ponikrf/frank/hardware/frank_m1/DOCS/back.png

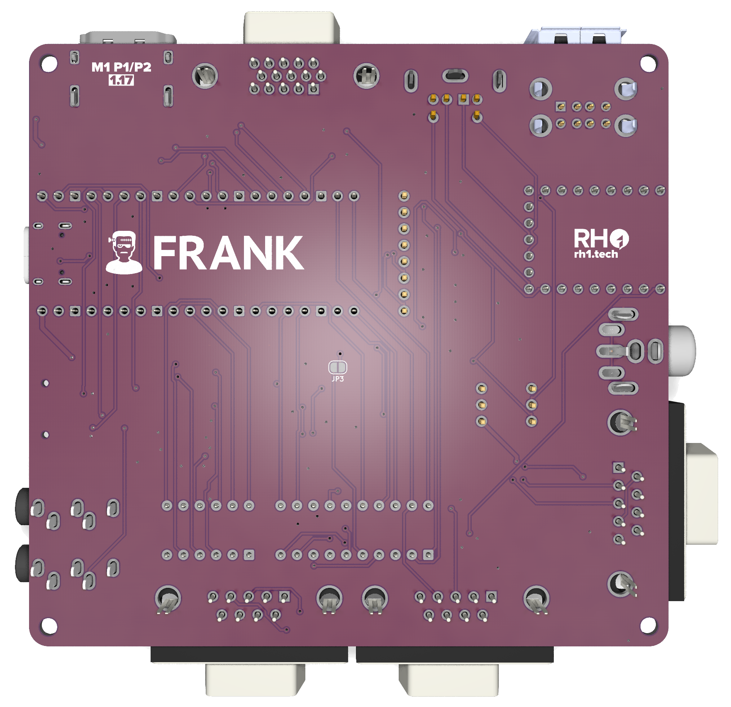
hardware/frank_m1/DOCS/back.png
