ponikrf/frank/hardware/frank_m2/DOCS/front.png

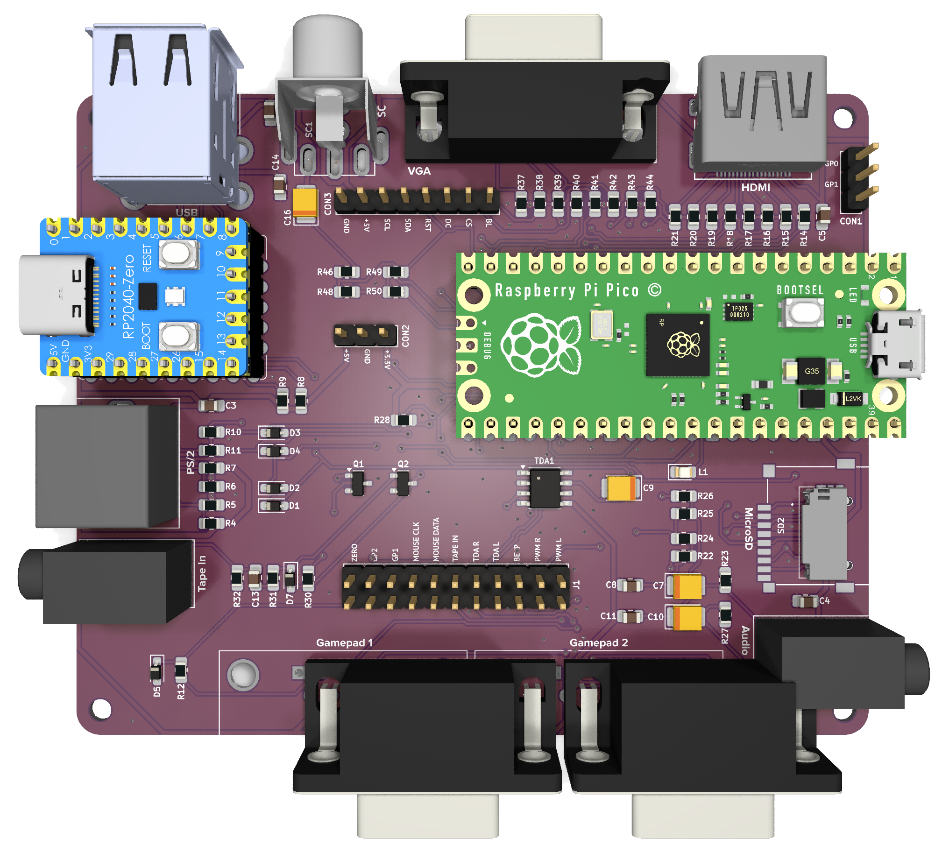
hardware/frank_m2/DOCS/front.png
