ponikrf/frank/hardware/minifrank_rm1/DOCS/front.png

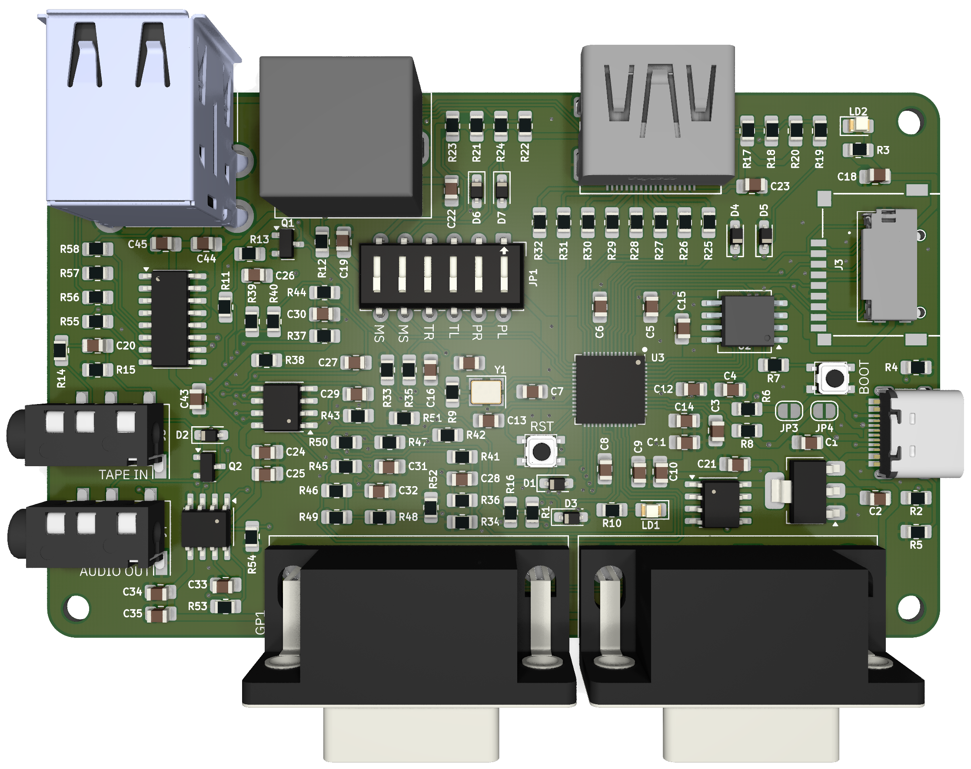
hardware/minifrank_rm1/DOCS/front.png
