ponikrf/frank/hardware/usb2ps2/DOCS/front.png

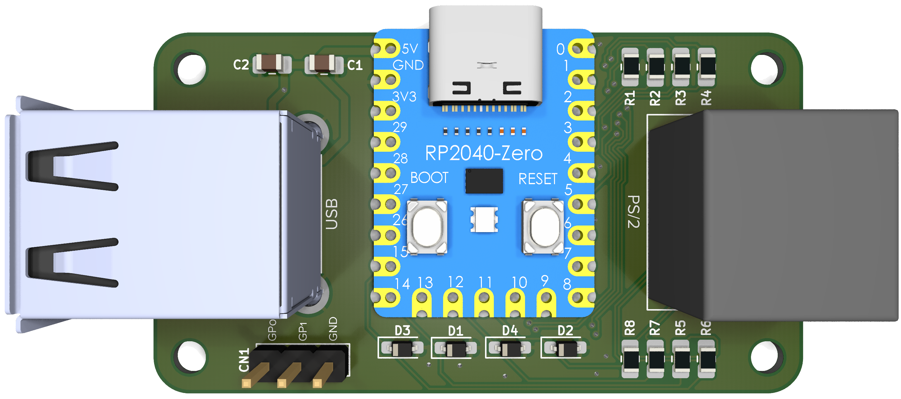
hardware/usb2ps2/DOCS/front.png
