ponikrf/frank/hardware/turbofrank/CASE/1_06/top.stl

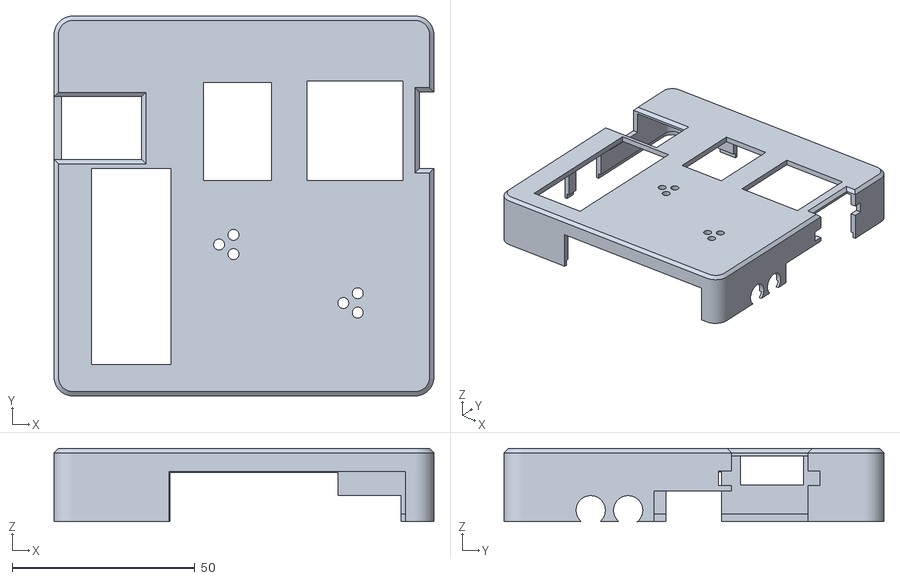
[picture p25: CAD file, 2025-05-07]
hardware/turbofrank/CASE/1_06/top.stl
104.0 x 104.0 x 20.0
