ponikrf/frank/hardware/frank_m1/3D/FHU-1x5.step

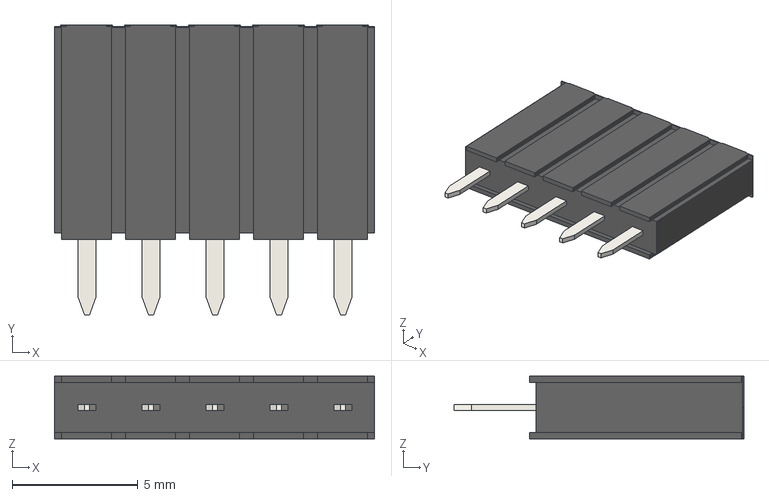
[picture p27: CAD file, 2025-05-07]
hardware/frank_m1/3D/FHU-1x5.step
12.7 x 11.5 x 2.50 mm
