ponikrf/frank/hardware/frank_m2/3D/FHU-1x20.step

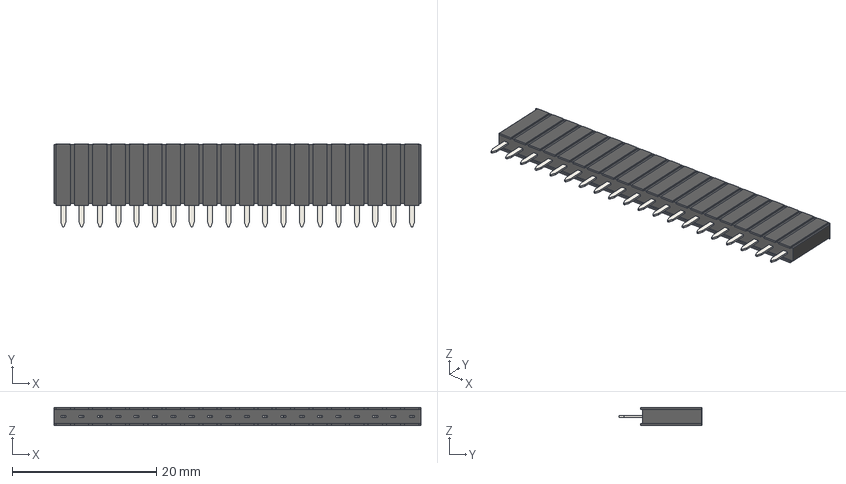
[picture p28: CAD file, 2025-05-07]
hardware/frank_m2/3D/FHU-1x20.step
50.8 x 11.5 x 2.50 mm
