ponikrf/frank/lab/minifrank_rm2/3D/DS05-127-2-04BK-SMT-TR.step

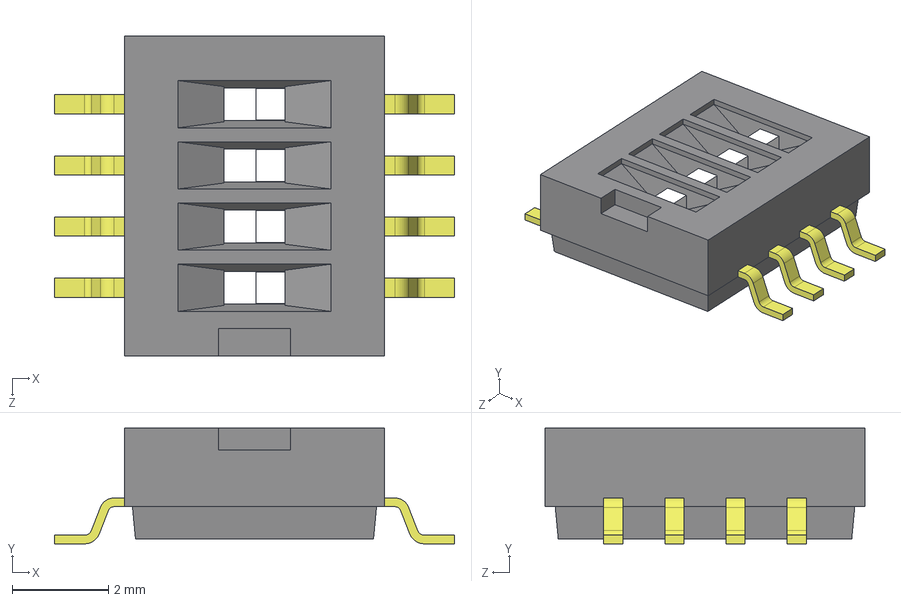
[picture p29: CAD file, 2025-05-07]
lab/minifrank_rm2/3D/DS05-127-2-04BK-SMT-TR.step
8.30 x 2.40 x 6.65 mm
