ponikrf/frank/hardware/turbofrank/3D/Micro_SD_Card_and_Holder.stp

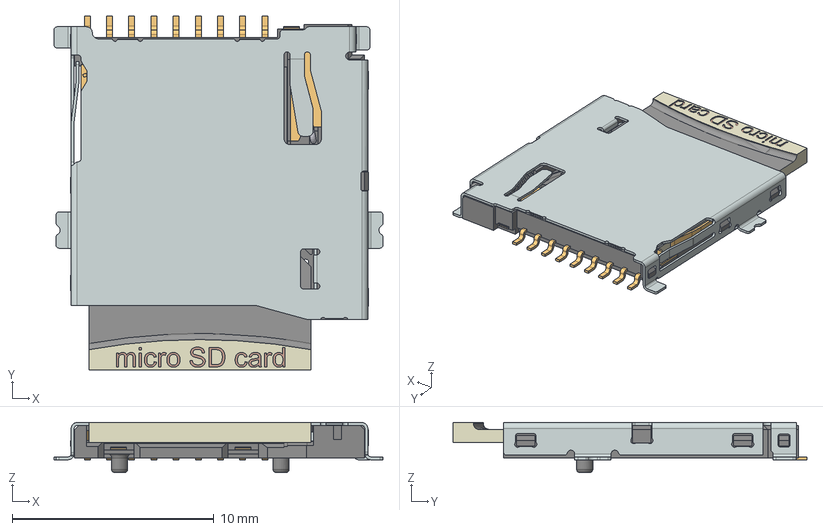
[picture p30: CAD file, 2025-05-07]
hardware/turbofrank/3D/Micro_SD_Card_and_Holder.stp
16.3 x 17.5 x 2.48 mm
693071020811_Housing
693071020811_Guide
693071020811_Spring
693071020811_Contact
693071020811_Hook
693071020811_Agraphe
693071020811_Shielding
MicroSD
