ponikrf/frank/lab/minifrank_rm2/3D/raspberry pi pico with contacts.step

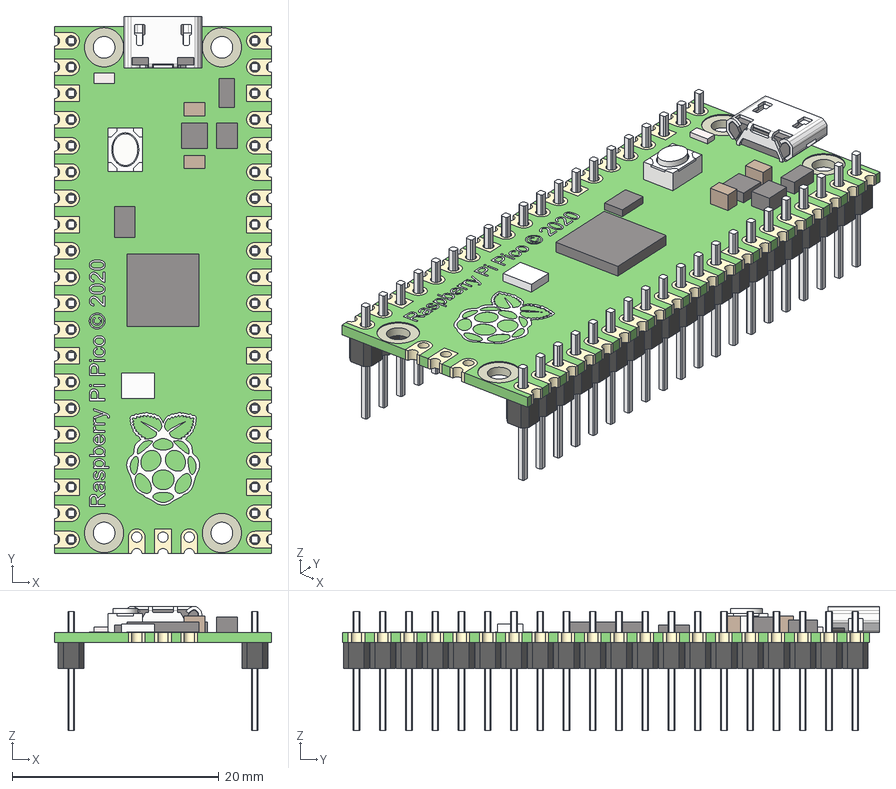
[picture p31: CAD file, 2025-05-07]
lab/minifrank_rm2/3D/raspberry pi pico with contacts.step
21.0 x 52.0 x 12.0 mm
ножка x 20
ножка v3(Mirror) x 20
