ponikrf/frank/hardware/frank_m2/3D/1x20 Male Pin Header.STEP

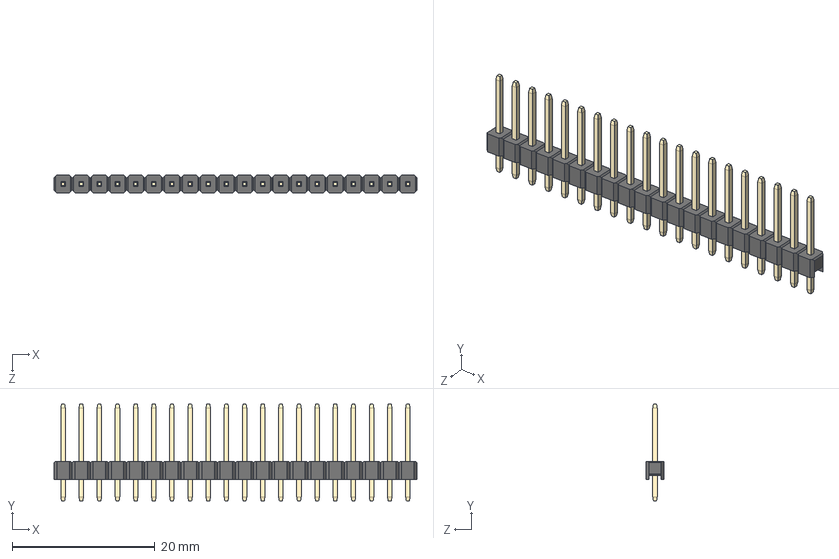
[picture p32: CAD file, 2025-05-07]
hardware/frank_m2/3D/1x20 Male Pin Header.STEP
50.8 x 13.5 x 2.50 mm
