ponikrf/frank/lab/minifrank_rm2/3D/soic-14.stp

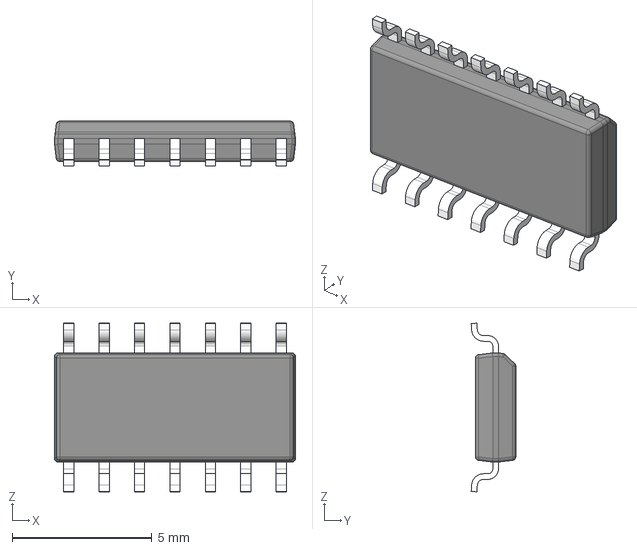
[picture p33: CAD file, 2025-05-07]
lab/minifrank_rm2/3D/soic-14.stp
8.64 x 1.60 x 6.05 mm
BODY_M14A_20
LEAD_M14A_46 x 14
