ponikrf/frank/lab/minifrank_rm2/3D/ESP8266-12E_ESP-12E.step

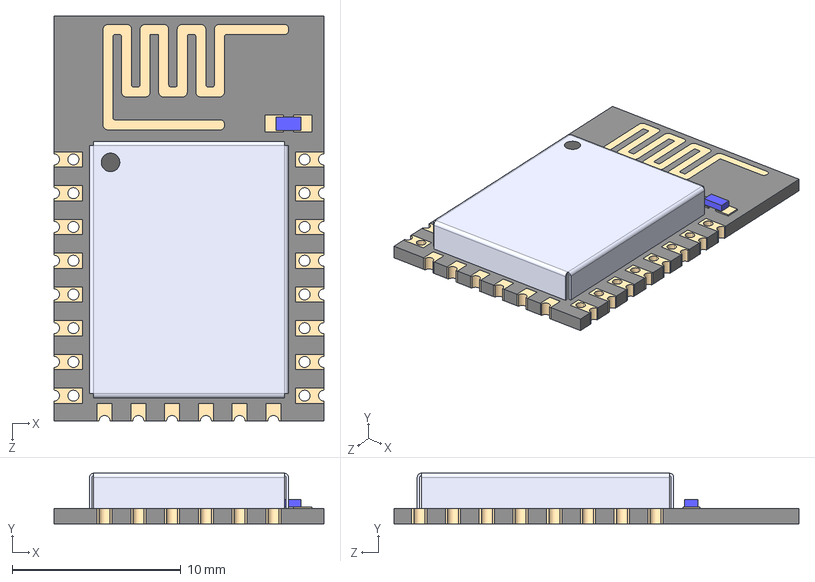
[picture p34: CAD file, 2025-05-07]
lab/minifrank_rm2/3D/ESP8266-12E_ESP-12E.step
16.0 x 3.00 x 24.0 mm
