ponikrf/frank/lab/minifrank_rm2/3D/LQH2MCN100K02L.step

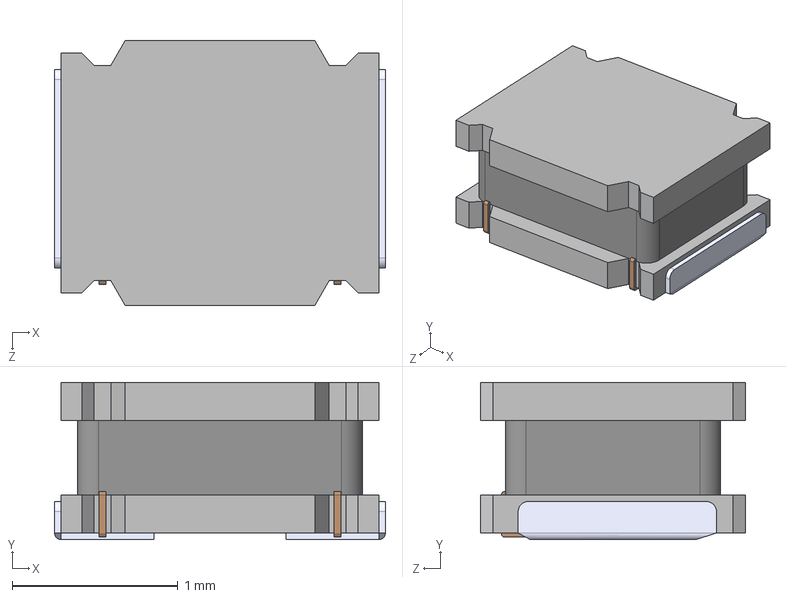
[picture p35: CAD file, 2025-05-07]
lab/minifrank_rm2/3D/LQH2MCN100K02L.step
2.00 x 0.95 x 1.60 mm
