ponikrf/frank/lab/minifrank_rm2/3D/Mini-DIN-6P.step

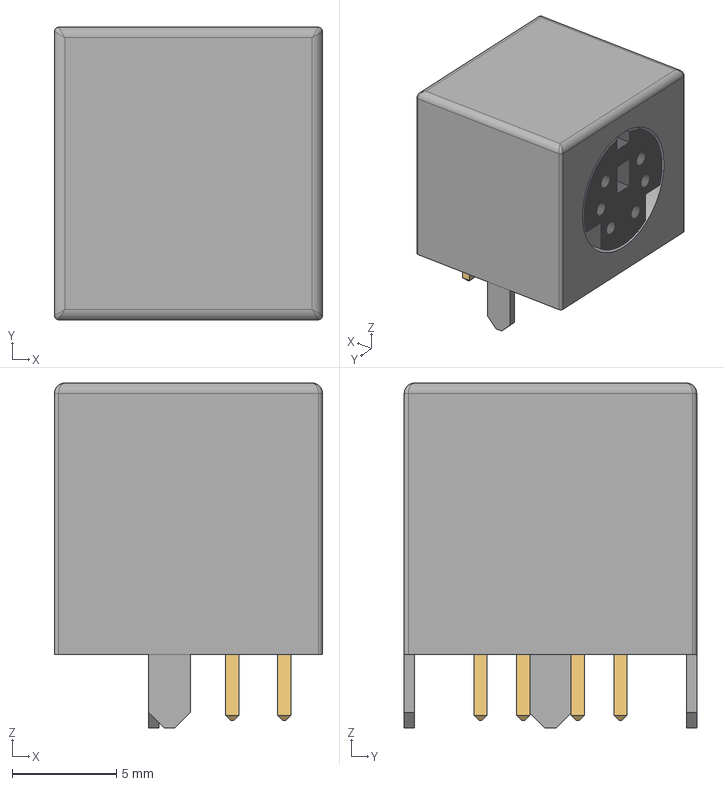
[picture p36: CAD file, 2025-03-16]
lab/minifrank_rm2/3D/Mini-DIN-6P.step
12.8 x 14.0 x 16.5 mm
