ponikrf/frank/lab/minifrank_rm2/3D/SJ1-3535NG.stp

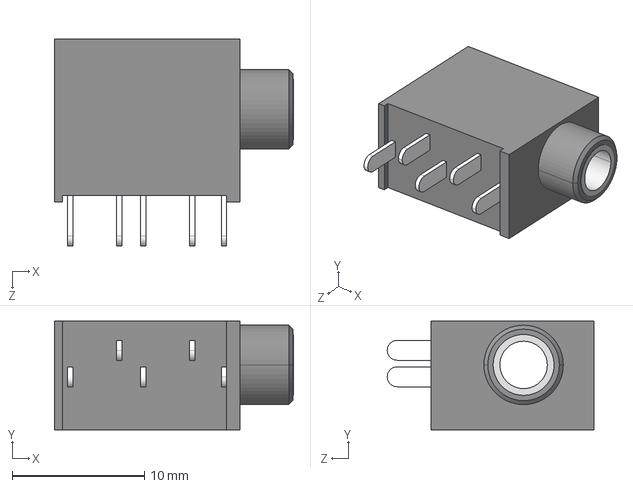
[picture p37: CAD file, 2025-03-16]
lab/minifrank_rm2/3D/SJ1-3535NG.stp
18.1 x 8.20 x 15.6 mm
