ponikrf/frank/lab/minifrank_rm2/3D/MAX232CSE+.stp

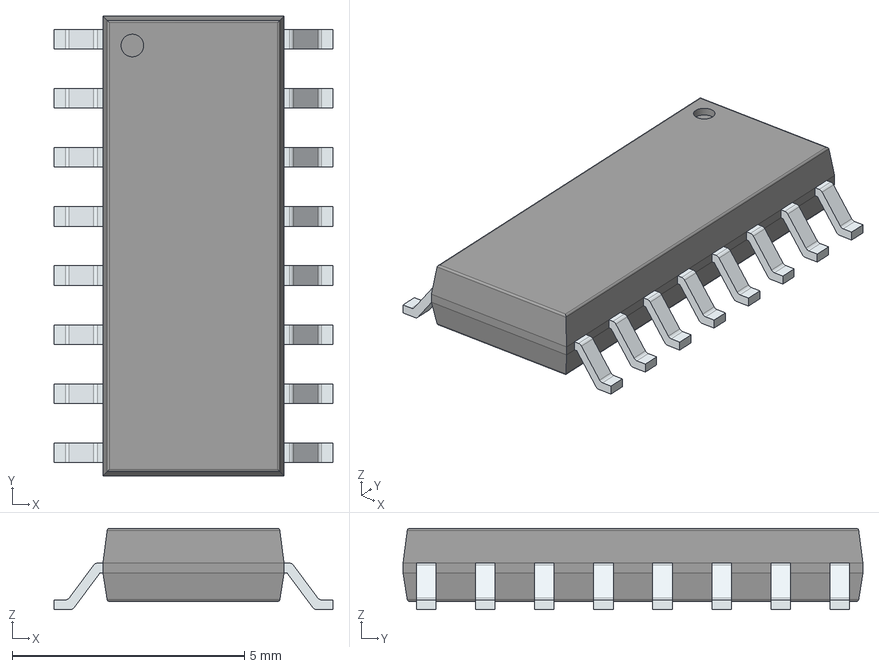
[picture p38: CAD file, 2025-03-16]
lab/minifrank_rm2/3D/MAX232CSE+.stp
6.00 x 9.90 x 1.75 mm
PinsArrayLR
