ponikrf/frank/lab/minifrank_rm2/3D/USB1035-GF-P-0-B-B.stp

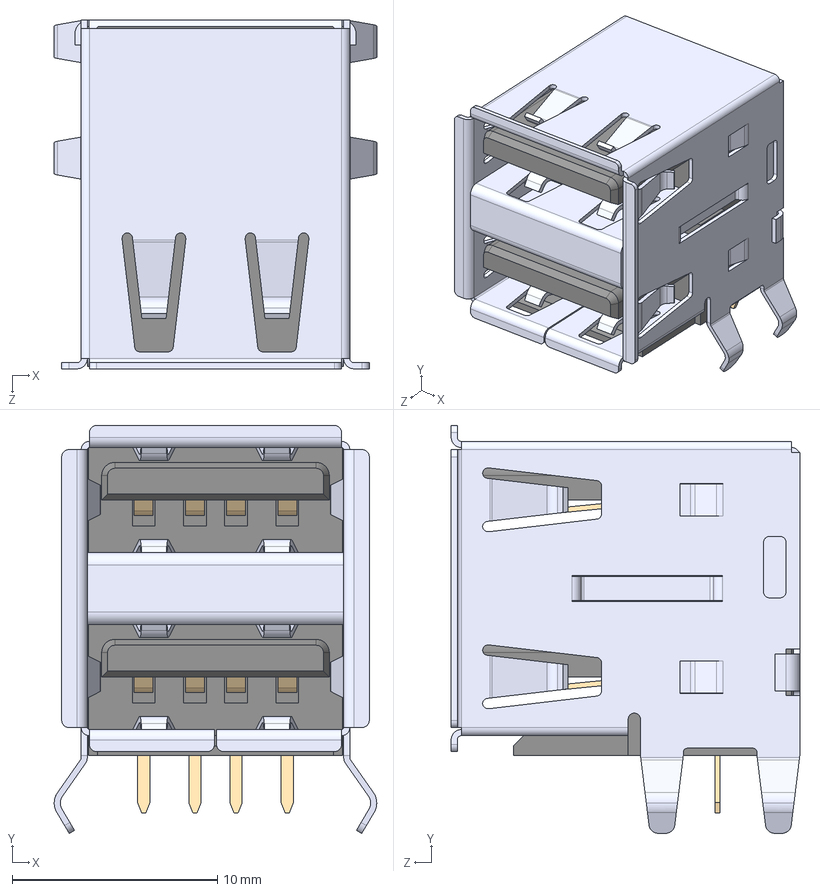
[picture p40: CAD file, 2025-03-16]
lab/minifrank_rm2/3D/USB1035-GF-P-0-B-B.stp
15.7 x 19.9 x 17.0 mm
