ponikrf/frank/lab/minifrank_rm2/3D/3225 SMD Crystal Oscillator.STEP

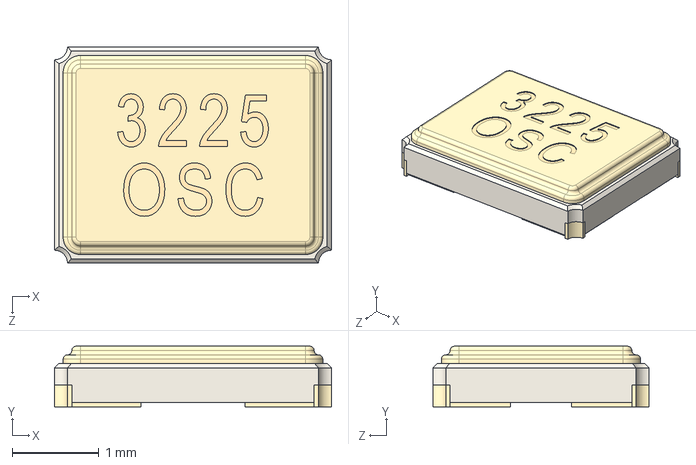
[picture p41: CAD file, 2025-03-16]
lab/minifrank_rm2/3D/3225 SMD Crystal Oscillator.STEP
3.20 x 0.7 x 2.50 mm
