ponikrf/frank/lab/minifrank_rm2/3D/PJ320D.STEP

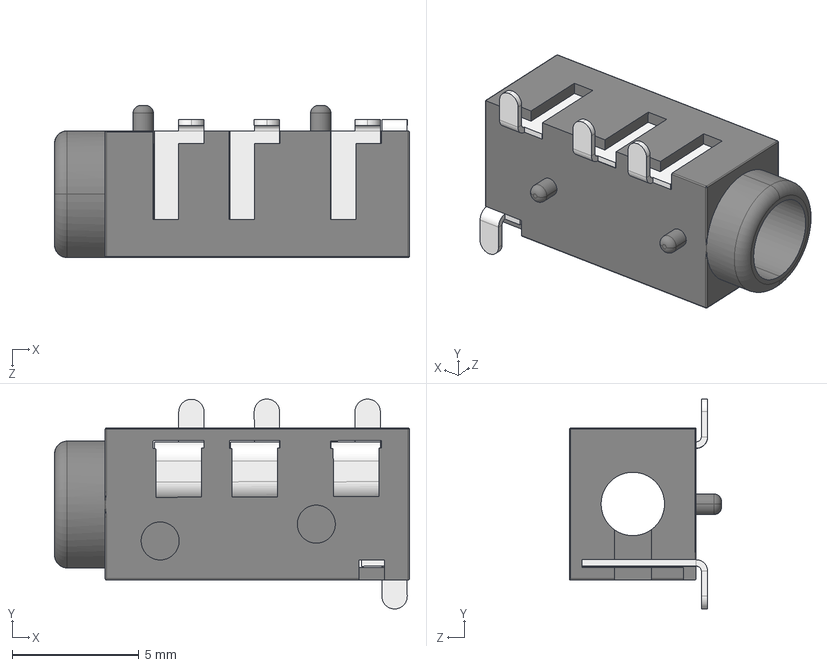
[picture p42: CAD file, 2025-03-16]
lab/minifrank_rm2/3D/PJ320D.STEP
14.0 x 8.28 x 6.00 mm
PJ320A
PJ320D-Pin x 3
PJ320D-Pin-B
