ponikrf/frank/lab/minifrank_rm2/3D/DSUB-15-HD_Male_Horizontal_P2.29x1.98mm_EdgePinOffset3.03mm_Housed_MountingHolesOffset4.94mm.step

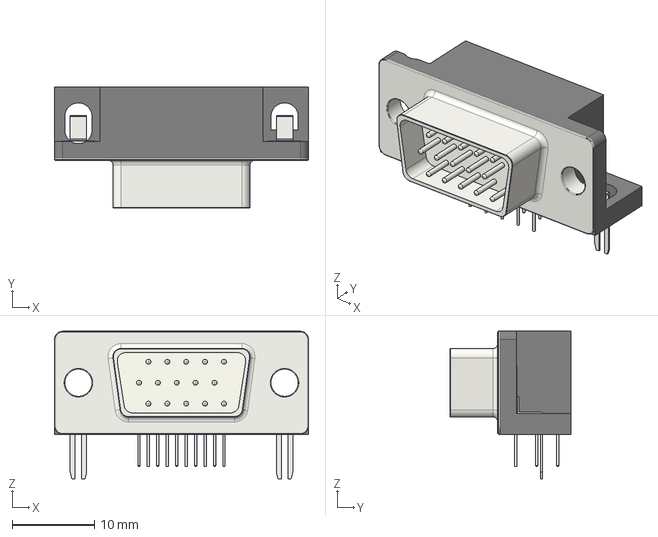
[picture p43: CAD file, 2025-03-16]
lab/minifrank_rm2/3D/DSUB-15-HD_Male_Horizontal_P2.29x1.98mm_EdgePinOffset3.03mm_Housed_MountingHolesOffset4.94mm.step
30.8 x 14.7 x 17.9 mm
