ponikrf/frank/lab/minifrank_rm2/3D/W25Q128JVSIQ.stp

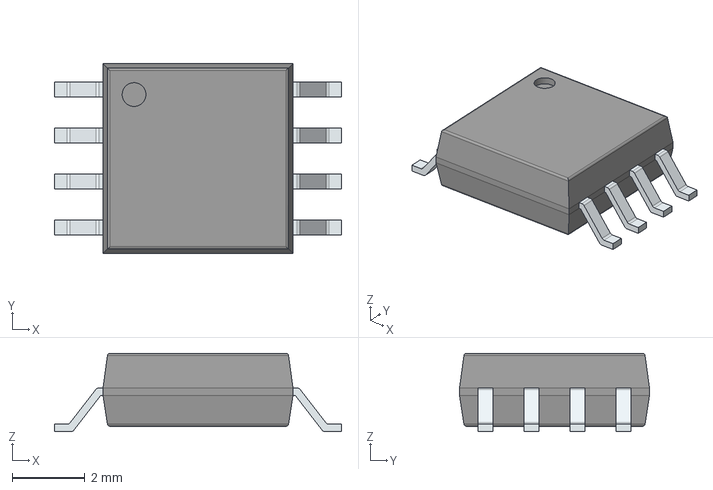
[picture p44: CAD file, 2025-03-16]
lab/minifrank_rm2/3D/W25Q128JVSIQ.stp
7.90 x 5.23 x 2.16 mm
PinsArrayLR
