ponikrf/frank/lab/minifrank_rm2/3D/CUI_DEVICES_RCJ-013.step

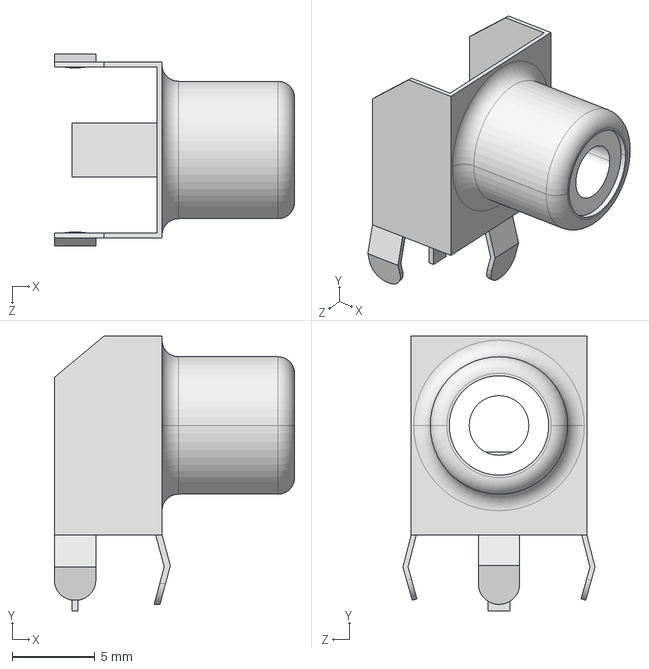
[picture p45: CAD file, 2025-03-16]
lab/minifrank_rm2/3D/CUI_DEVICES_RCJ-013.step
14.5 x 16.6 x 11.6 mm
