ponikrf/frank/lab/minifrank_rm2/3D/HRO_TYPE-C-31-M-12.step

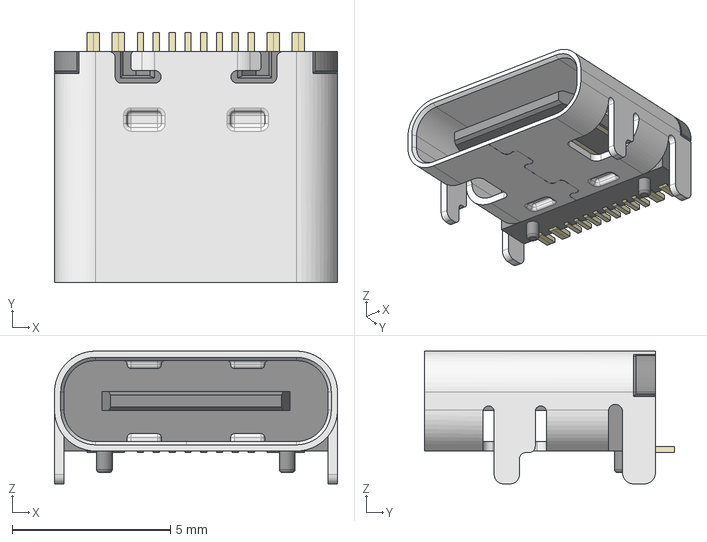
[picture p46: CAD file, 2025-03-16]
lab/minifrank_rm2/3D/HRO_TYPE-C-31-M-12.step
8.95 x 7.90 x 4.20 mm
