ponikrf/frank/lab/minifrank_rm2/3D/SO-8_5.3x6.2mm_P1.27mm.step

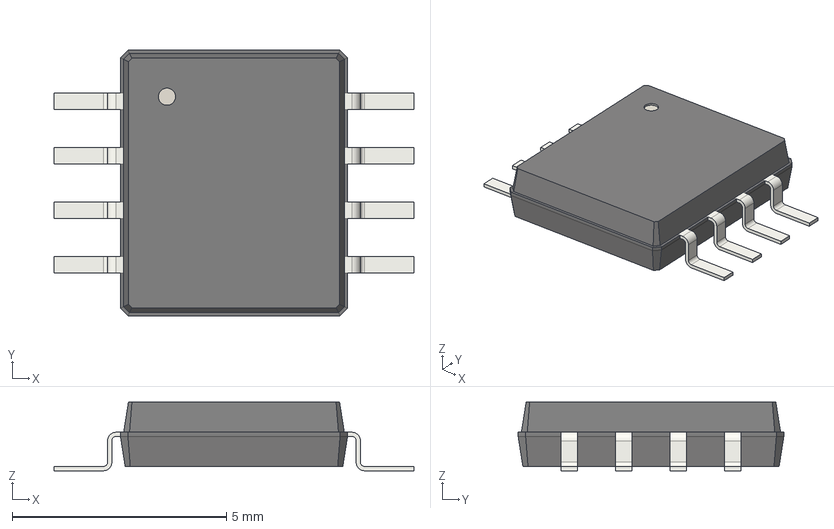
[picture p47: CAD file, 2025-03-16]
lab/minifrank_rm2/3D/SO-8_5.3x6.2mm_P1.27mm.step
8.40 x 6.20 x 1.60 mm
