ponikrf/frank/lab/minifrank_rm2/3D/Ts-1233_1.5.stp

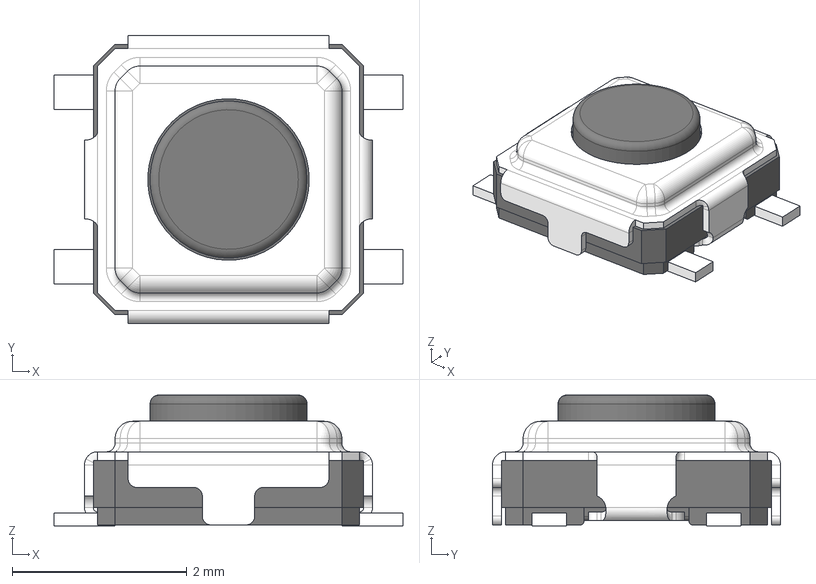
[picture p48: CAD file, 2025-03-16]
lab/minifrank_rm2/3D/Ts-1233_1.5.stp
4.00 x 3.30 x 1.50 mm
