ponikrf/frank/hardware/minifrank_rm1/DOCS/2_04/minifrank_rm1.pdf

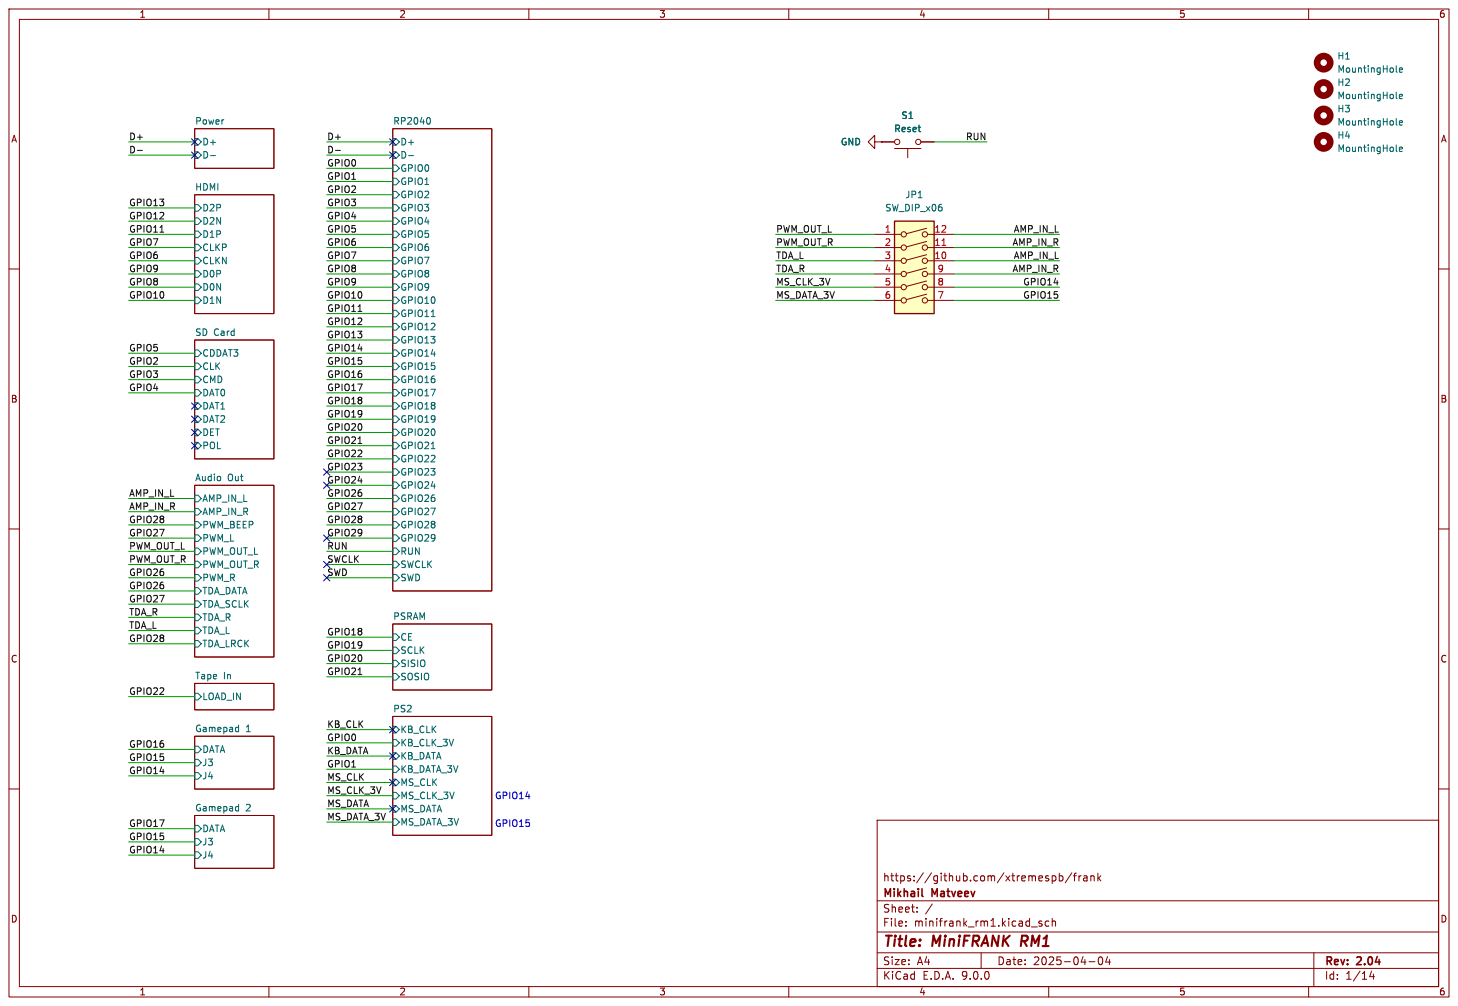
[picture p108: page 1]

https://github.com/xtremespb/frank

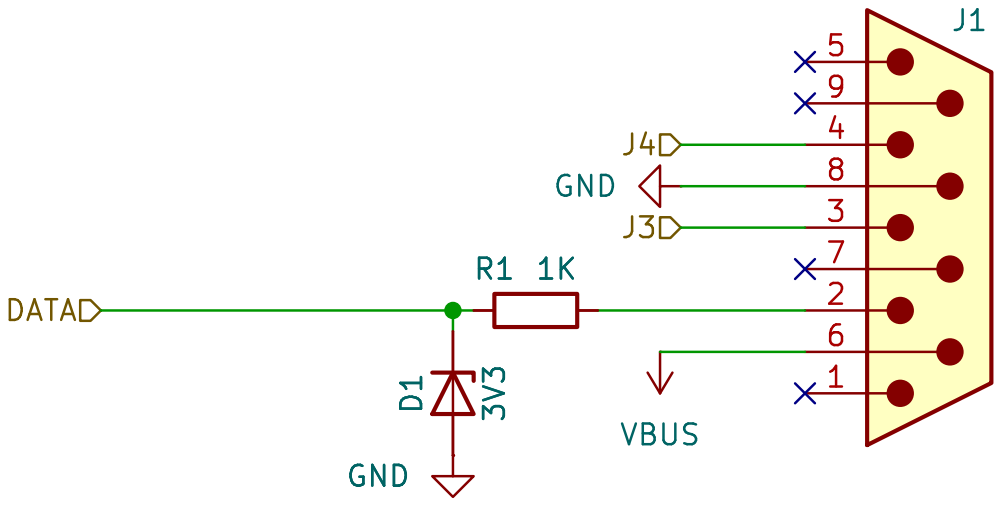
[picture p109: page 2]

https://github.com/xtremespb/frank

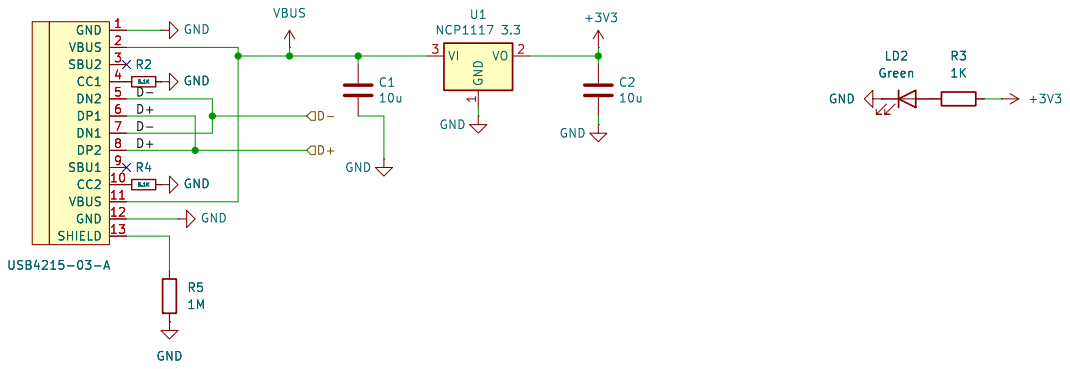
[picture p110: page 3]

https://github.com/xtremespb/frank

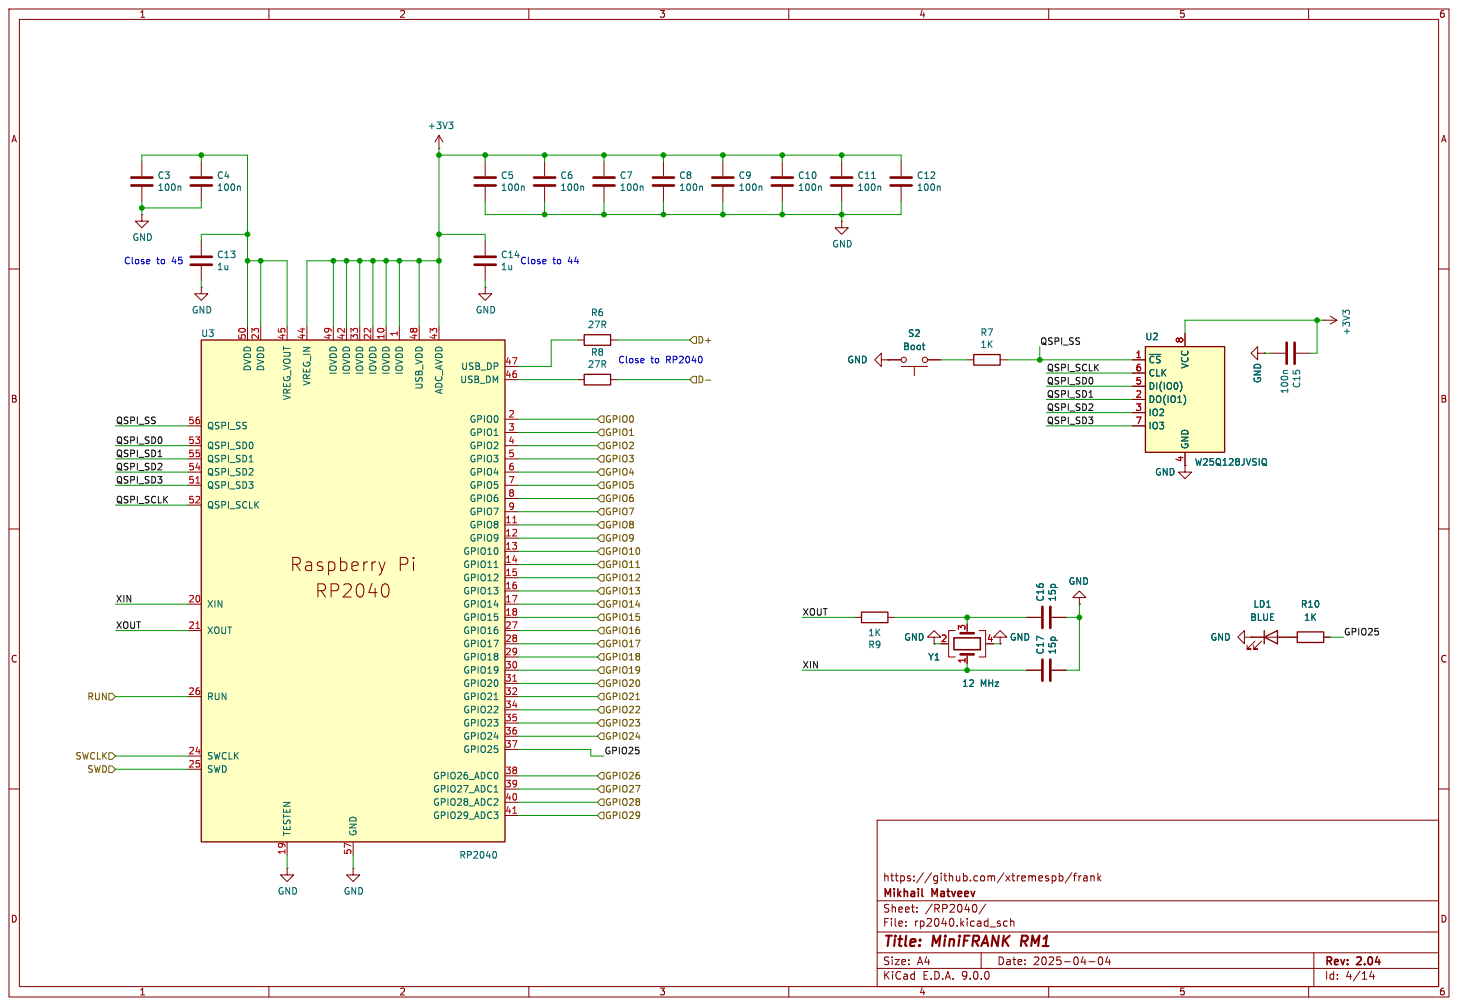
[picture p111: page 4]

https://github.com/xtremespb/frank GND

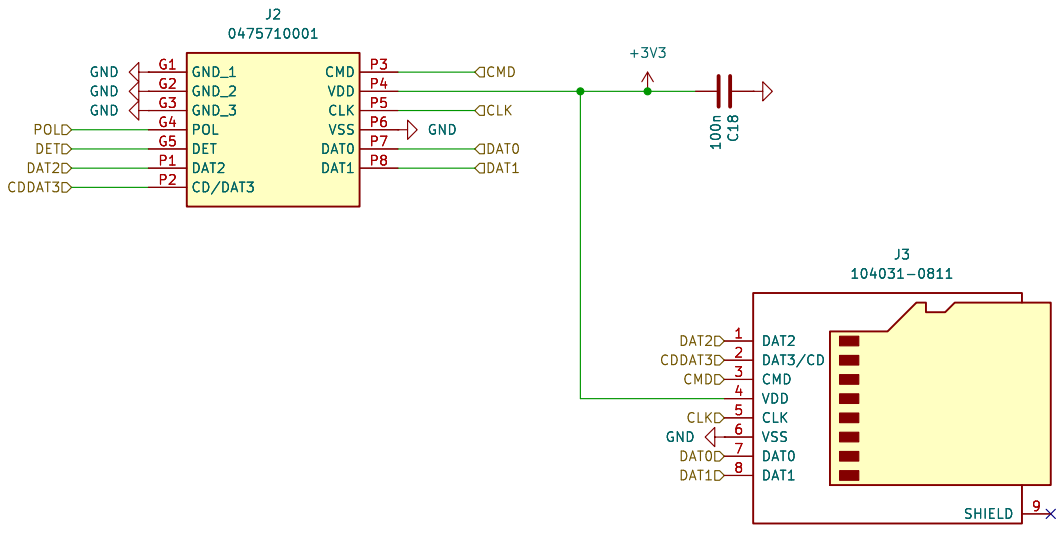
[picture p112: page 5]

https://github.com/xtremespb/frank GND

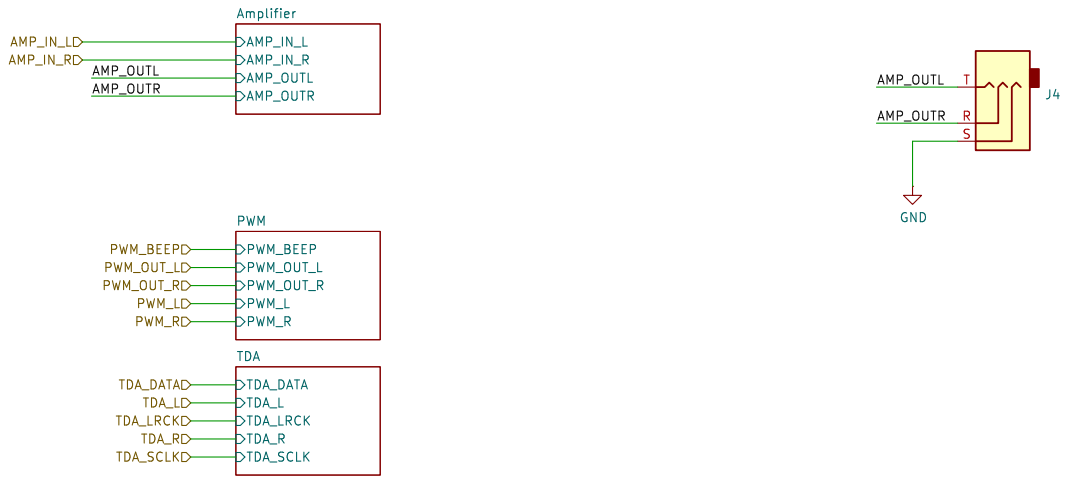
[picture p113: page 6]

https://github.com/xtremespb/frank

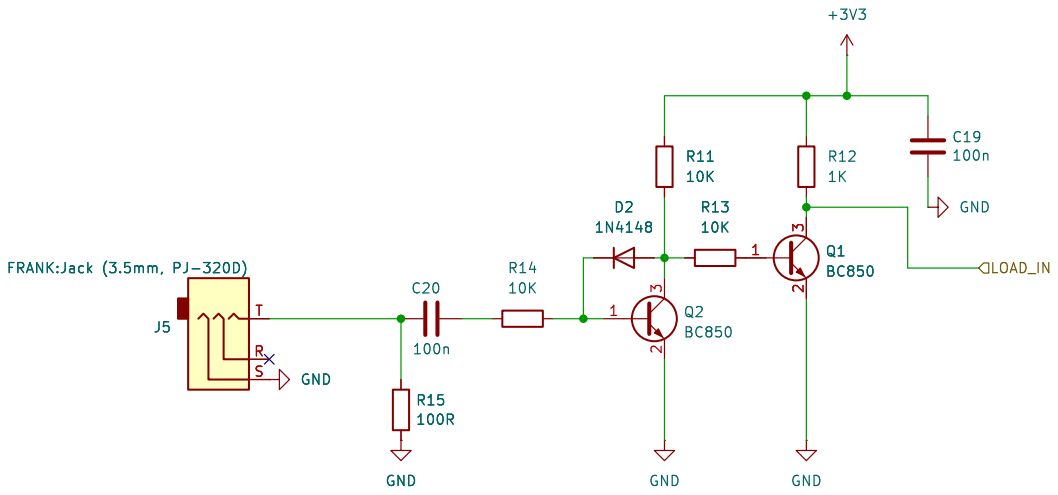
[picture p114: page 7]

https://github.com/xtremespb/frank GND

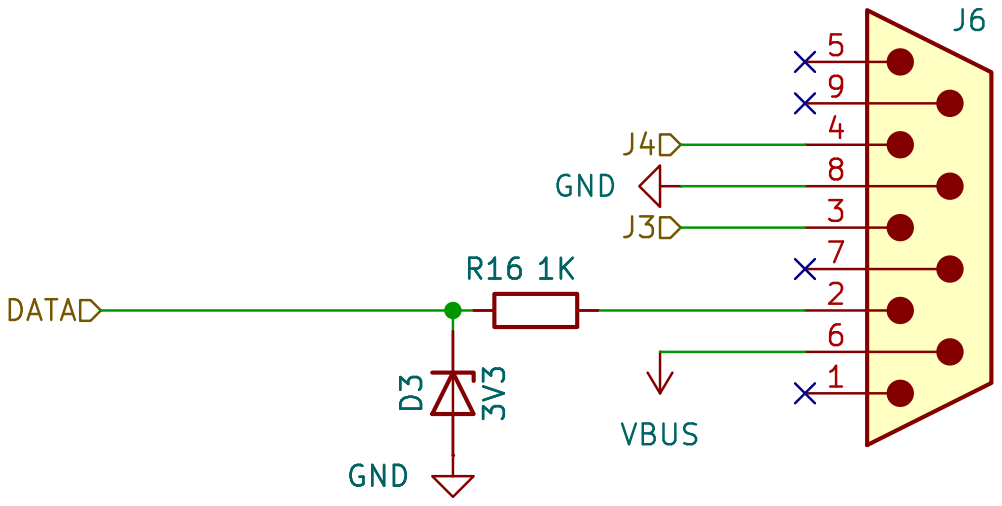
[picture p115: page 8]

https://github.com/xtremespb/frank

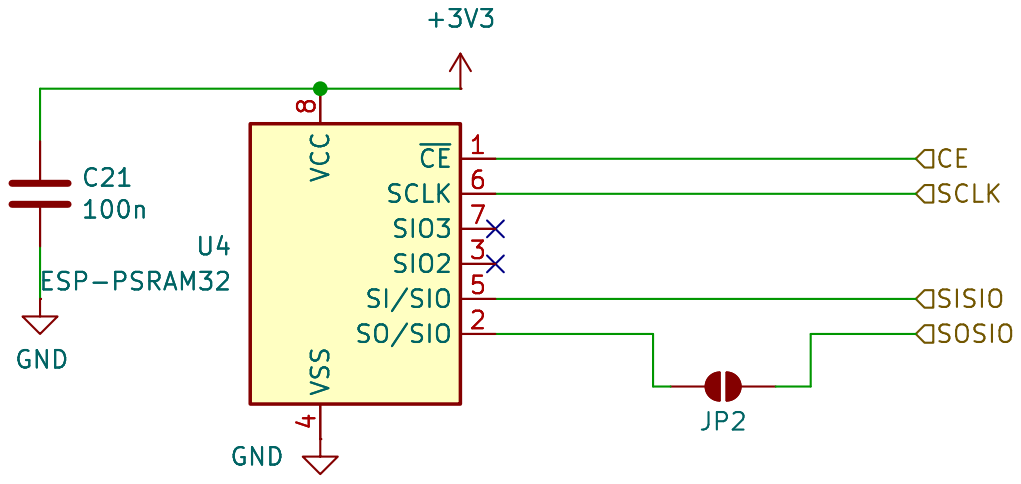
[picture p116: page 9]

4 ~{CE}1 SCLK 6 SIO3 7 SIO2 3 SI/SIO 5 SO/SIO 2 +3V3

4 ~{CE}1 SCLK 6 SIO3 7 SIO2 3 SI/SIO 5 SO/SIO 2 U4 ESP-PSRAM32 GND

https://github.com/xtremespb/frank

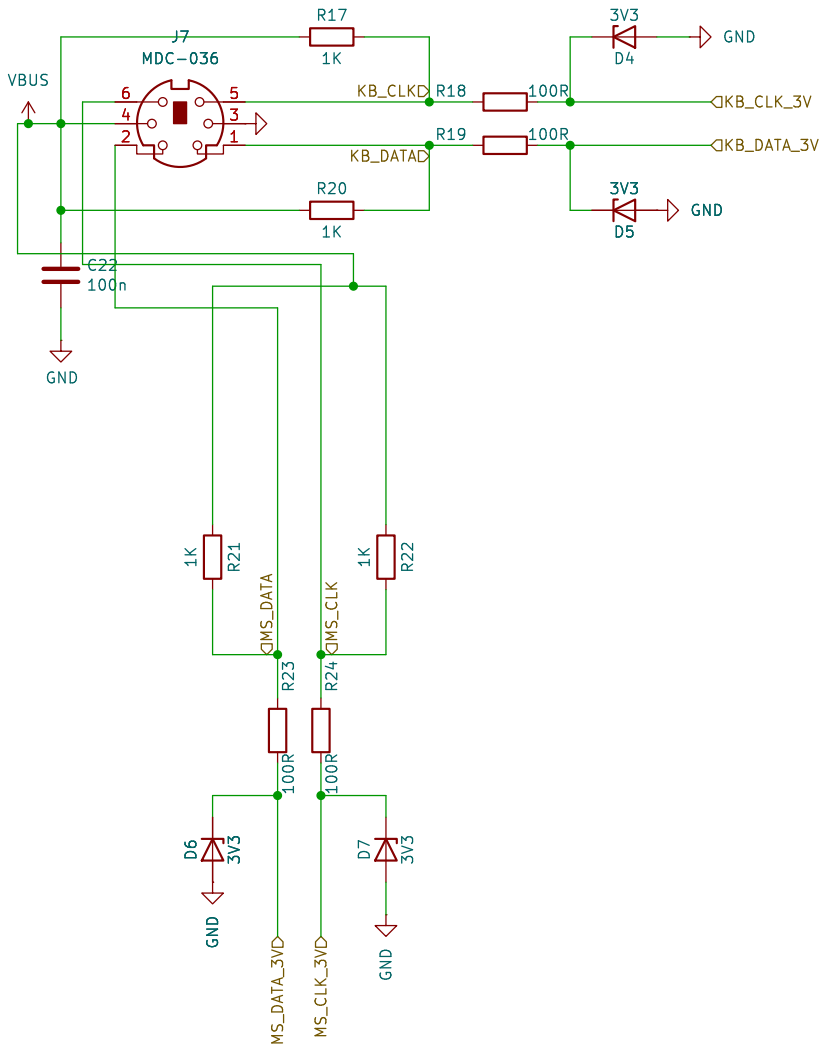
[picture p117: page 10]

https://github.com/xtremespb/frank R22 1K GND

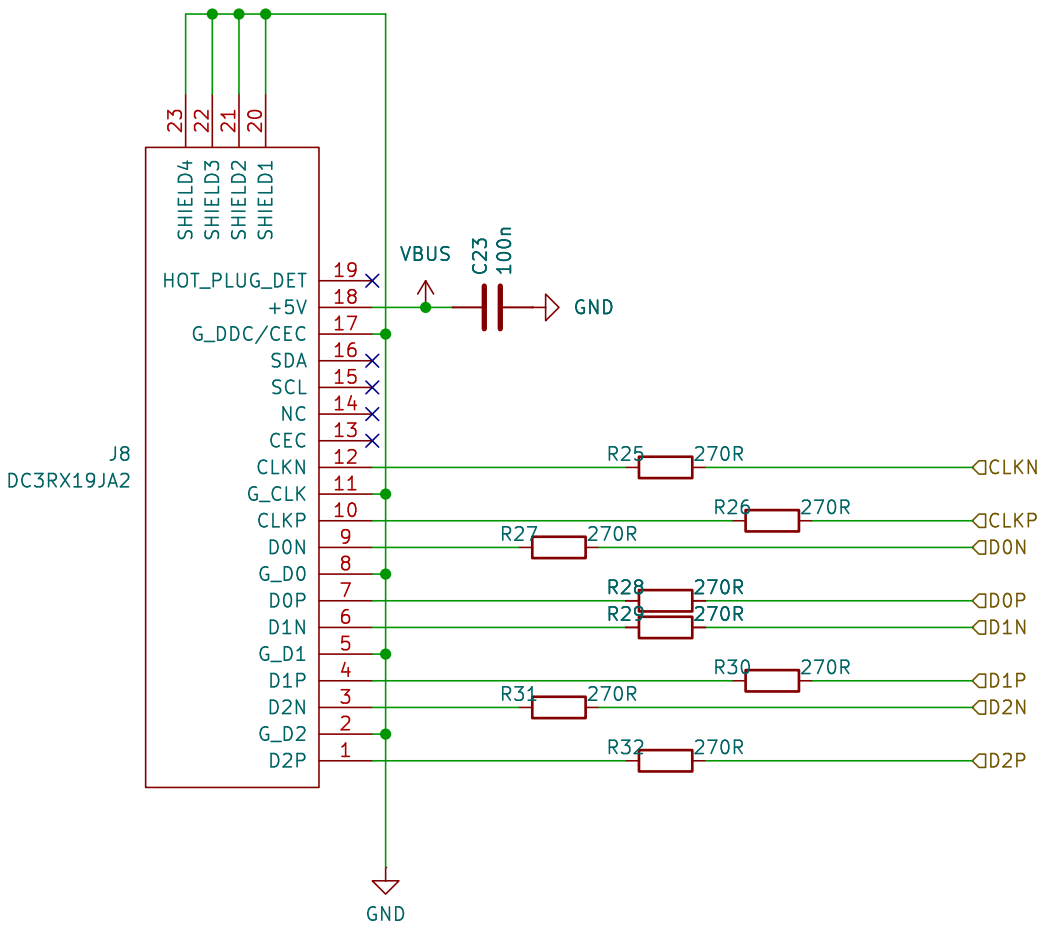
[picture p118: page 11]

https://github.com/xtremespb/frank

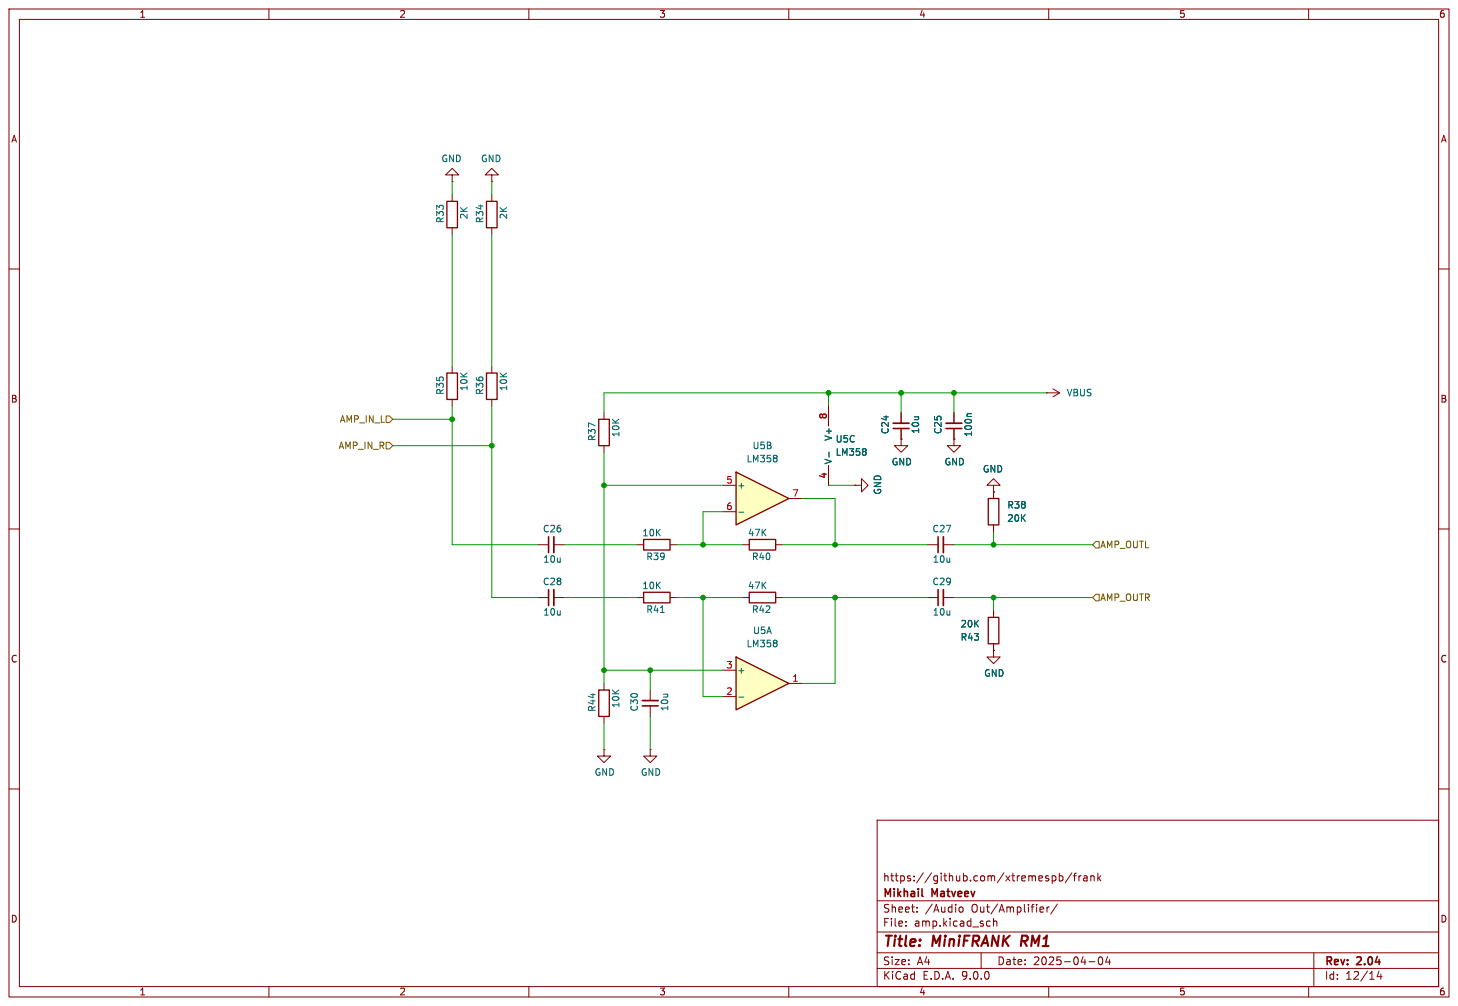
[picture p119: page 12]

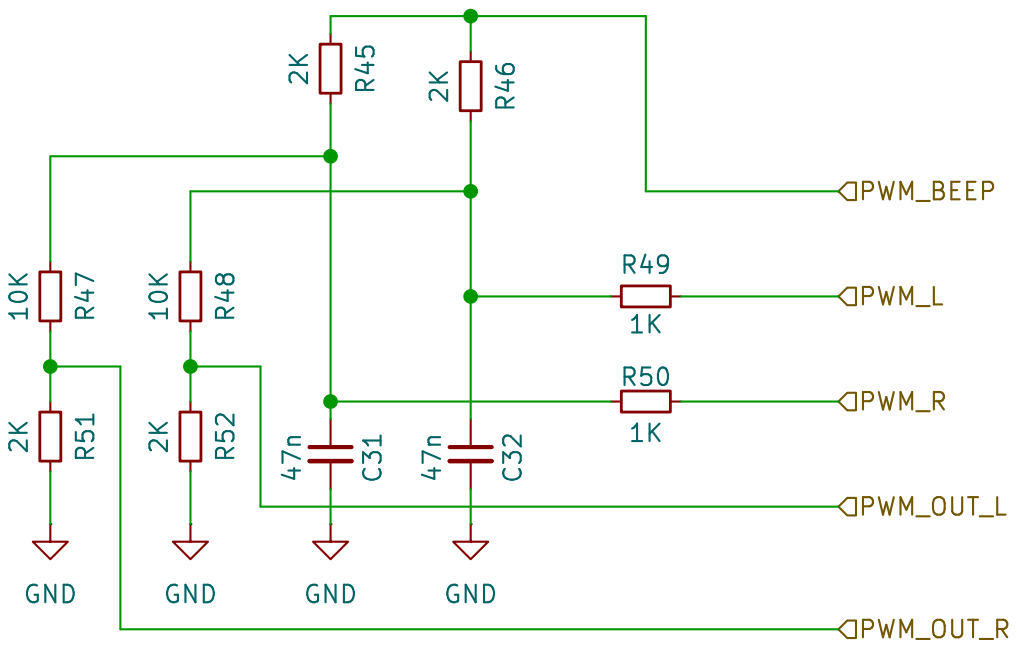
[picture p120: page 13]

https://github.com/xtremespb/frank R49

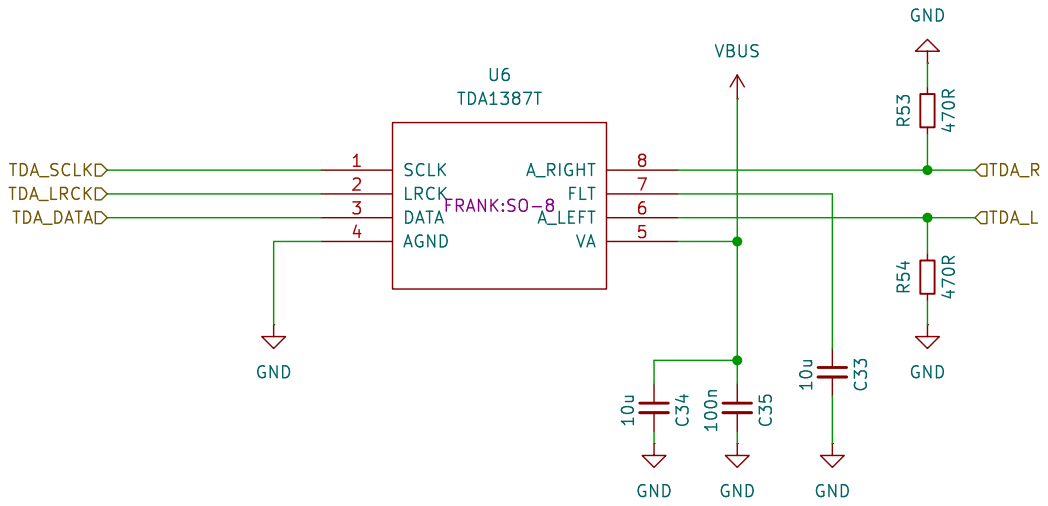
[picture p121: page 14]
