ponikrf/frank/hardware/minifrank_rm1/DOCS/2_05/assembly.pdf

## LD2 S²

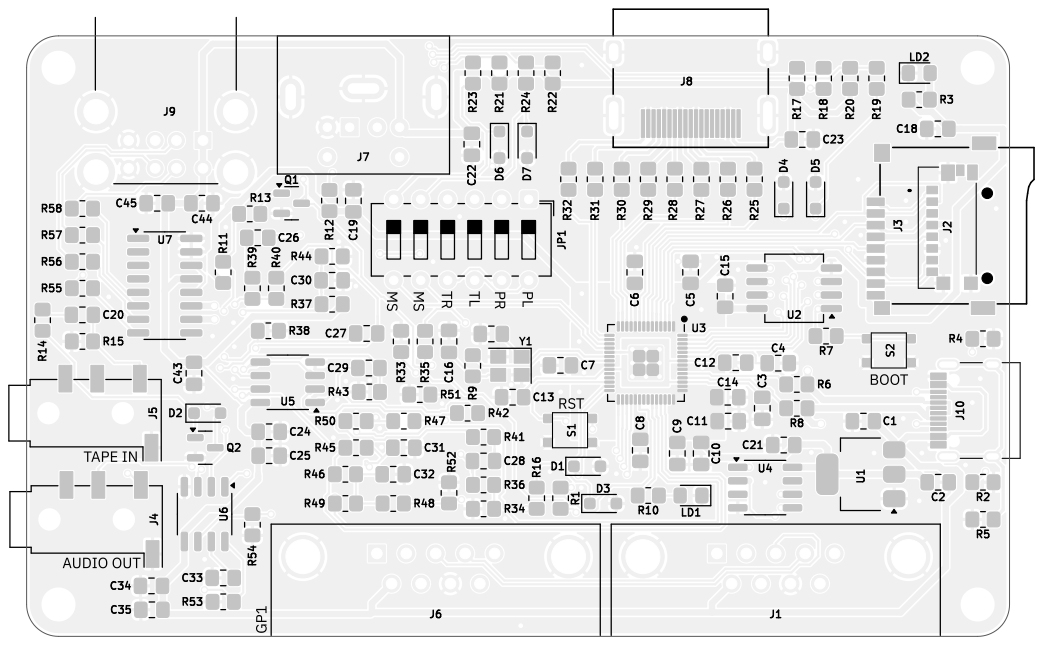
[picture p122: page 1]

https://github.com/xtremespb/frank Black And White TOP - Page 1/4

File: minifrank_rm1.kicad_pcb Sheet: Black And White TOP Mikhail Matveev

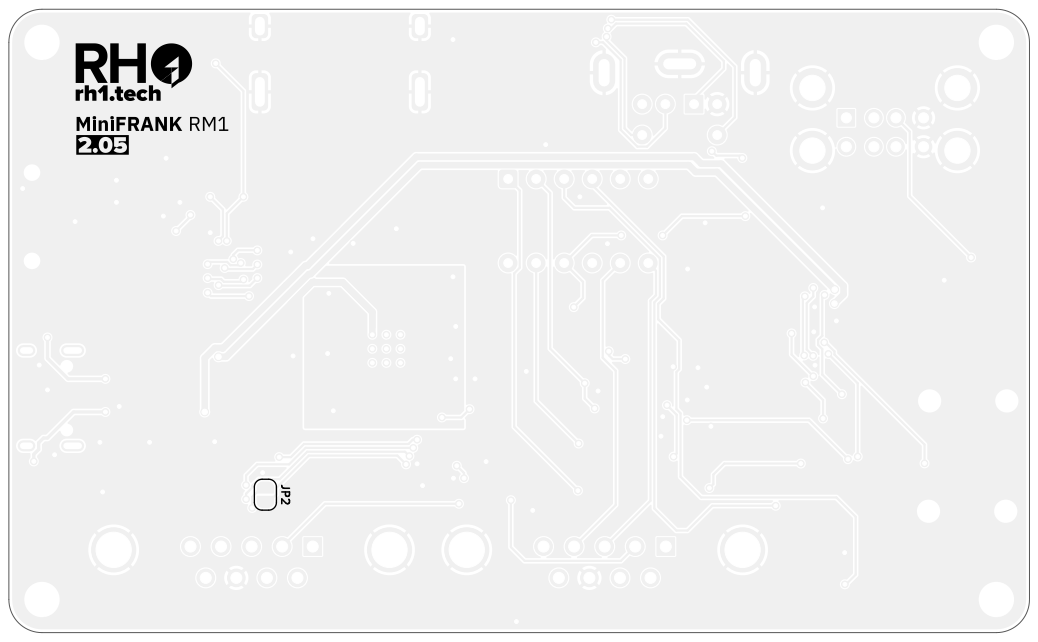
[picture p123: page 2]
D Date: 2025-04-07 KiCad; E.D.A. 9.0.0 Size: A4; Rev: 2.05; File: minifrank_rm1.kicad_pcb Sheet: Black; And; White; BOT Mikhail; Matveev; https://github.com/xtremespb/frank Black; BOT -; Page 2/4

Id: /1 Title: MiniFRANK RM1

## LD2 S²

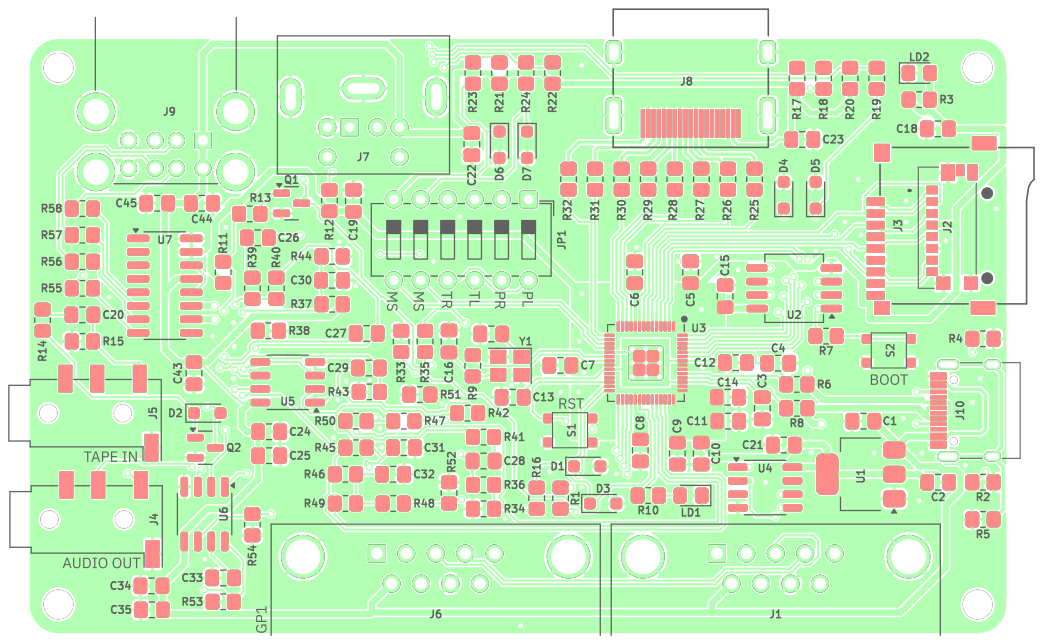
[picture p124: page 3]

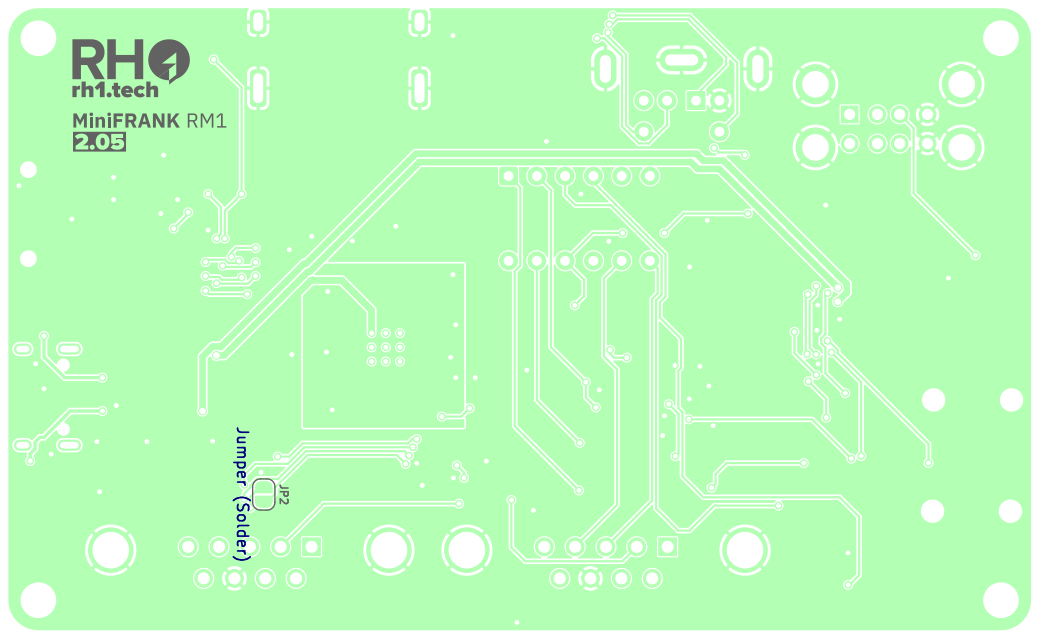
[picture p125: page 4]
D Date: 2025-04-07 KiCad; E.D.A. 9.0.0 Size: A4; Rev: 2.05; File: minifrank_rm1.kicad_pcb Sheet: Colored; BOT Mikhail; Matveev; https://github.com/xtremespb/frank Colored; BOT -; Page 4/4 Jumper (Solder)

Id: /1 Title: MiniFRANK RM1
