ponikrf/frank/hardware/minifrank_rm1/DOCS/2_05/minifrank_rm1.pdf

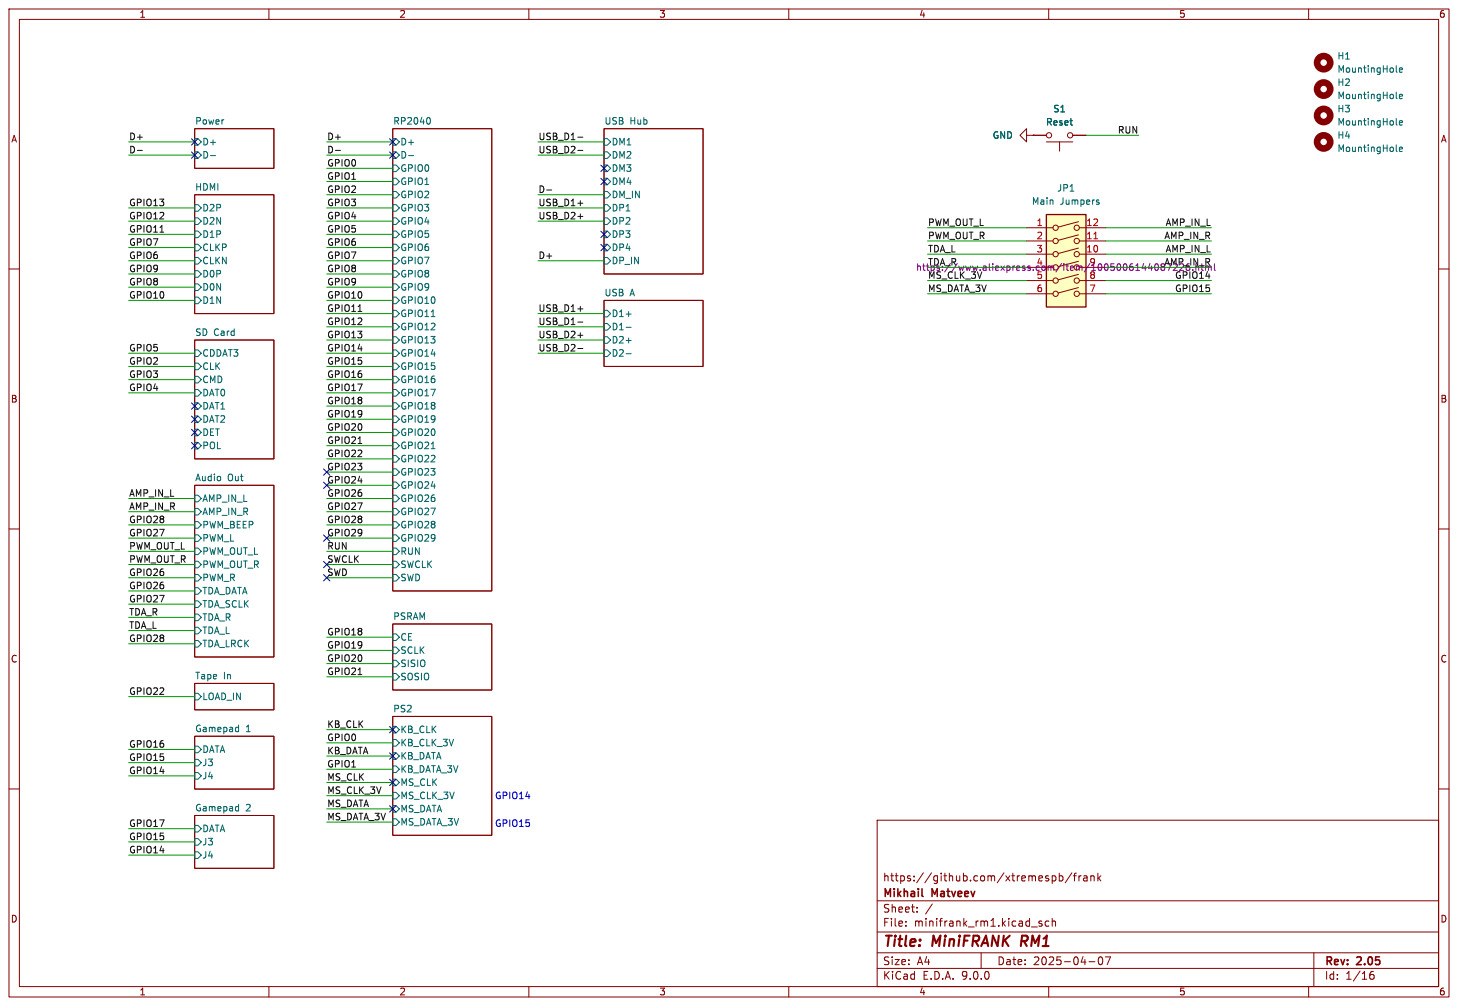
[picture p126: page 1]

PSRAM
https://github.com/xtremespb/frank CE
SCLK
SISIO
SOSIO


https://github.com/xtremespb/frank


https://github.com/xtremespb/frank

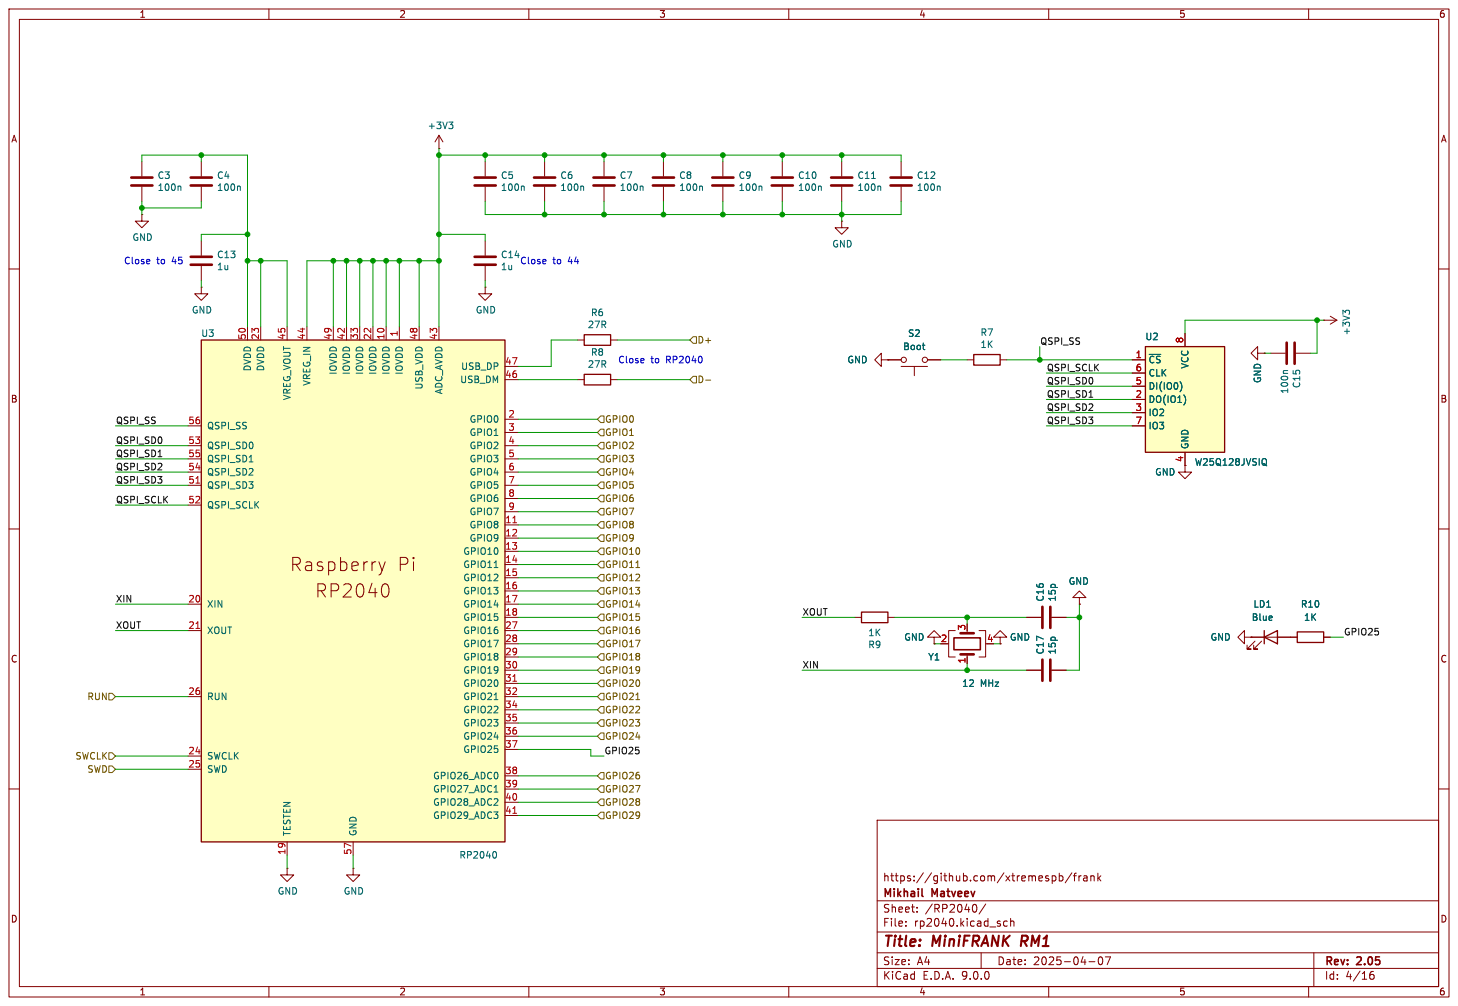
[picture p127: page 4]

https://github.com/xtremespb/frank GND



https://github.com/xtremespb/frank

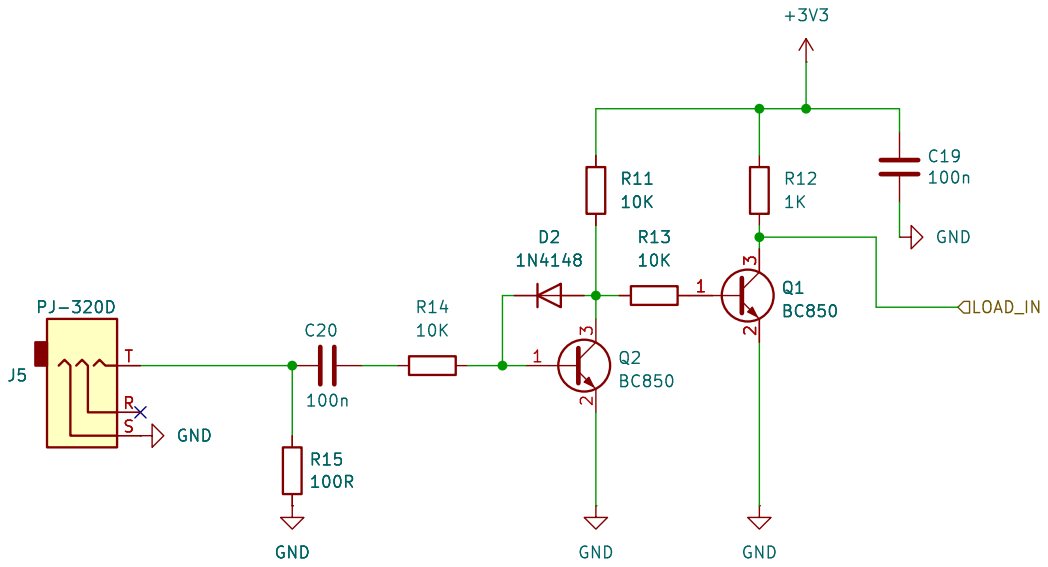
[picture p128: page 7]

https://github.com/xtremespb/frank GND


https://github.com/xtremespb/frank


4 ~{CE}1 SCLK 6 SIO3 7 SIO2 3 SI/SIO 5 SO/SIO 2 +3V3

4 ~{CE}1 SCLK 6 SIO3 7 SIO2 3 SI/SIO 5 SO/SIO 2 U4 ESP-PSRAM32 GND

https://github.com/xtremespb/frank


https://github.com/xtremespb/frank R22 1K GND

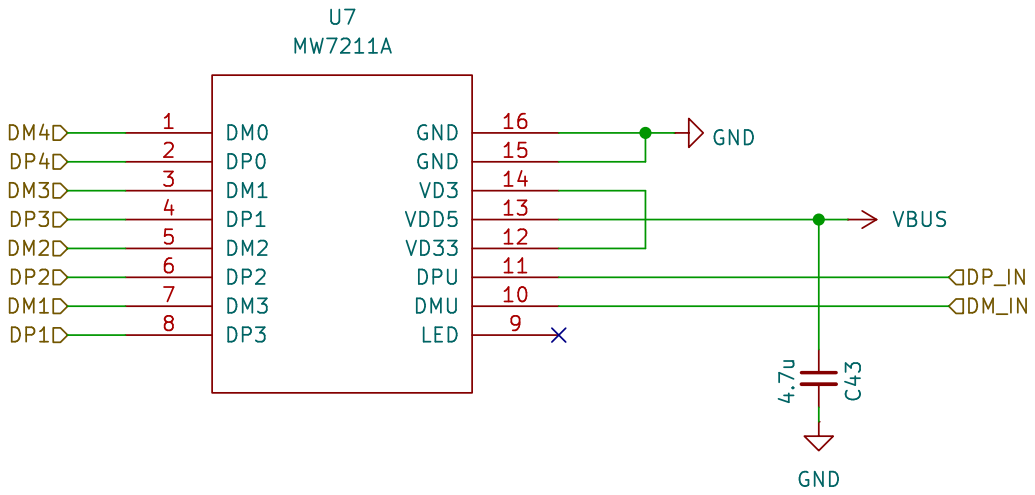
[picture p129: page 11]

https://github.com/xtremespb/frank

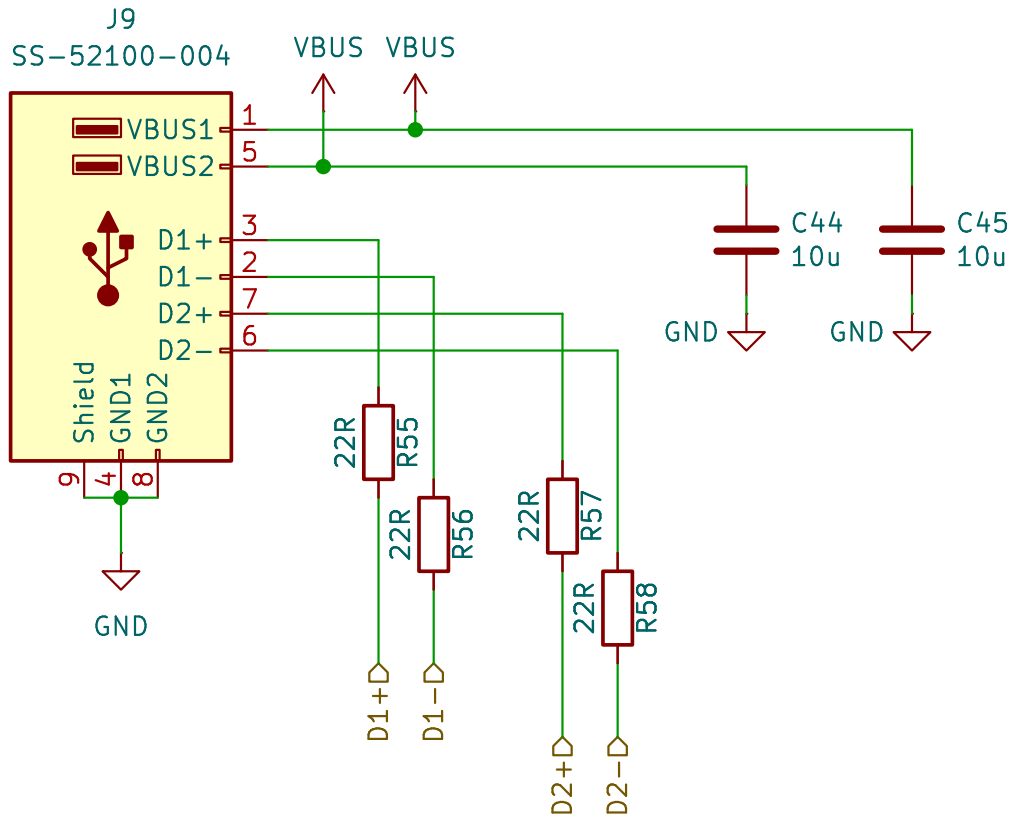
[picture p130: page 12]


https://github.com/xtremespb/frank

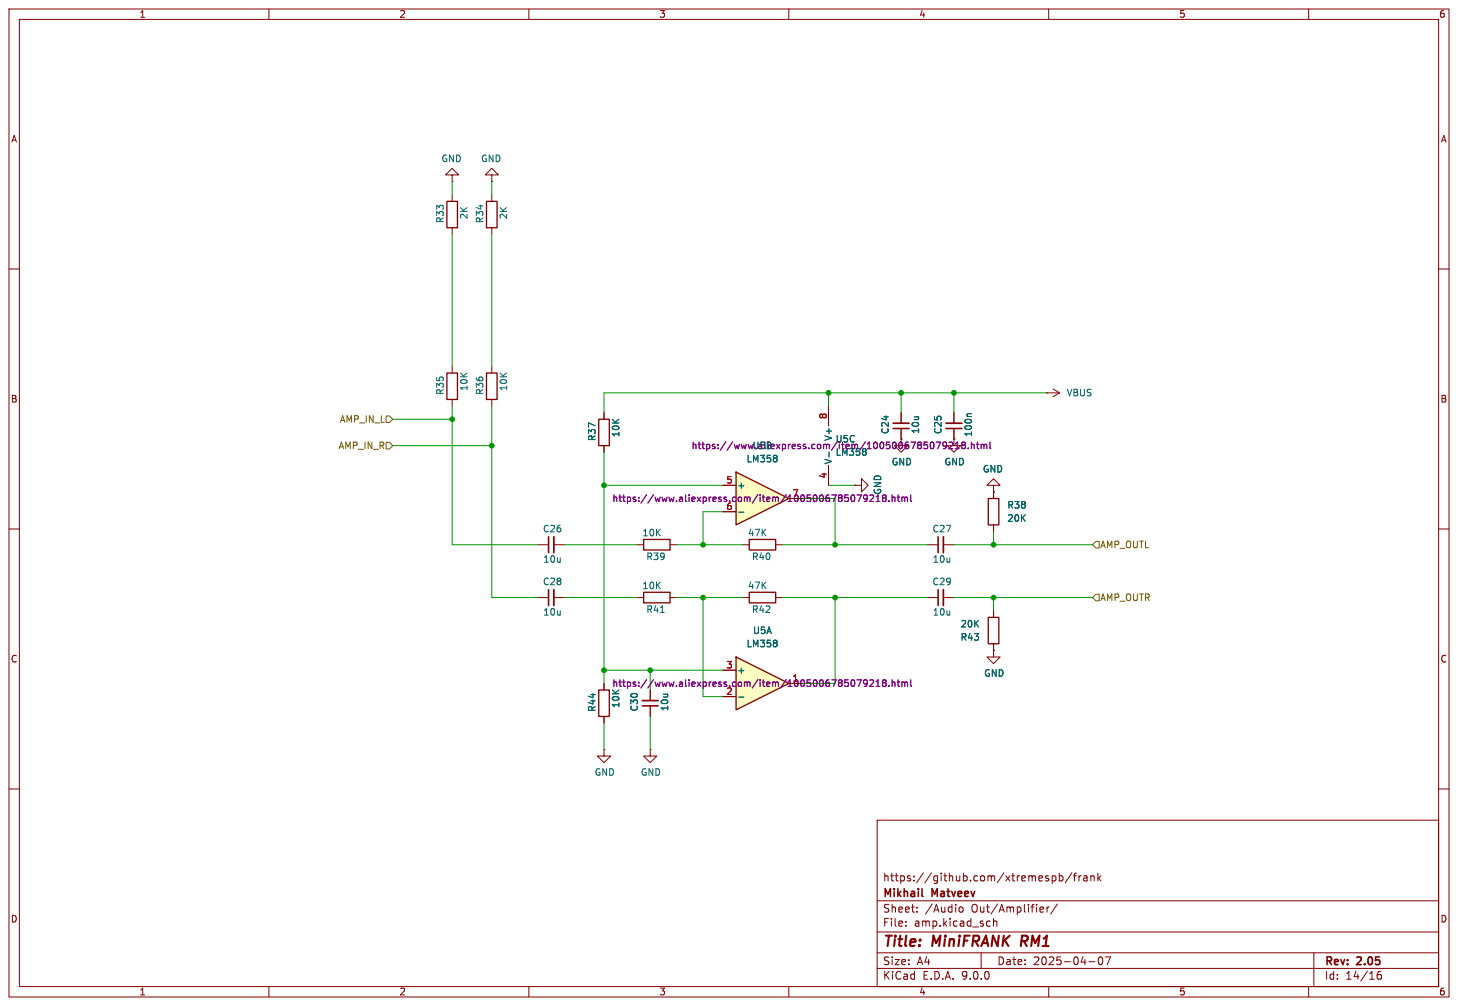
[picture p131: page 14]

LM358 https://www.aliexpress.com/item/1005006785079218.html V+

https://www.aliexpress.com/item/1005006785079218.html +

https://github.com/xtremespb/frank


https://github.com/xtremespb/frank R49
