ponikrf/frank/hardware/minifrank_rm1/DOCS/2_07/minifrank_rm1.pdf

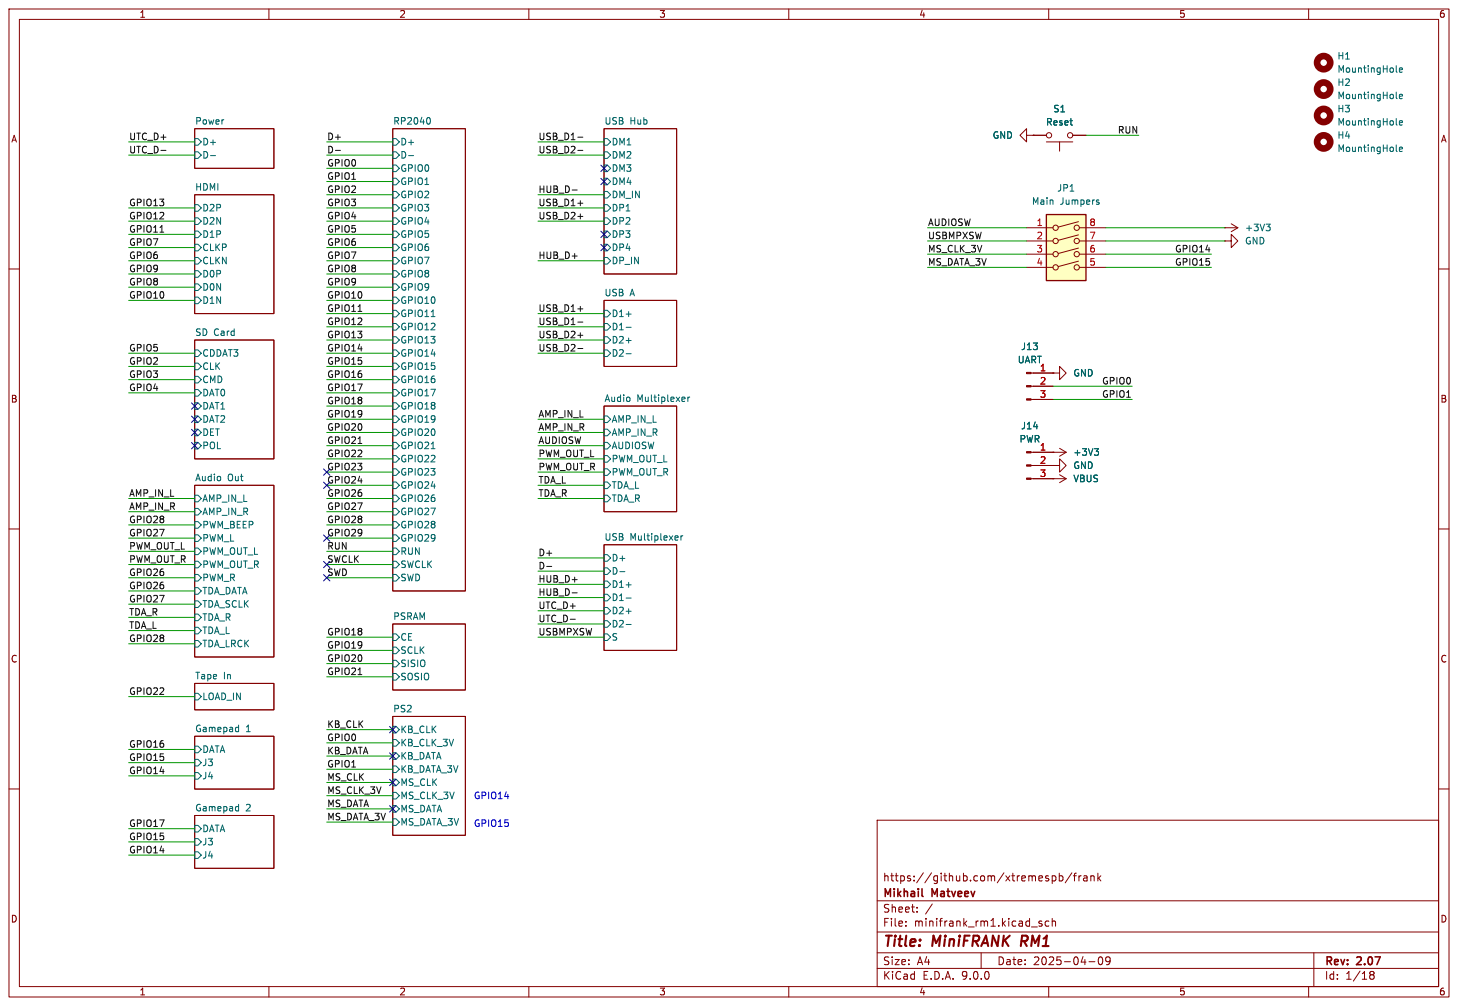
[picture p132: page 1]

https://github.com/xtremespb/frank

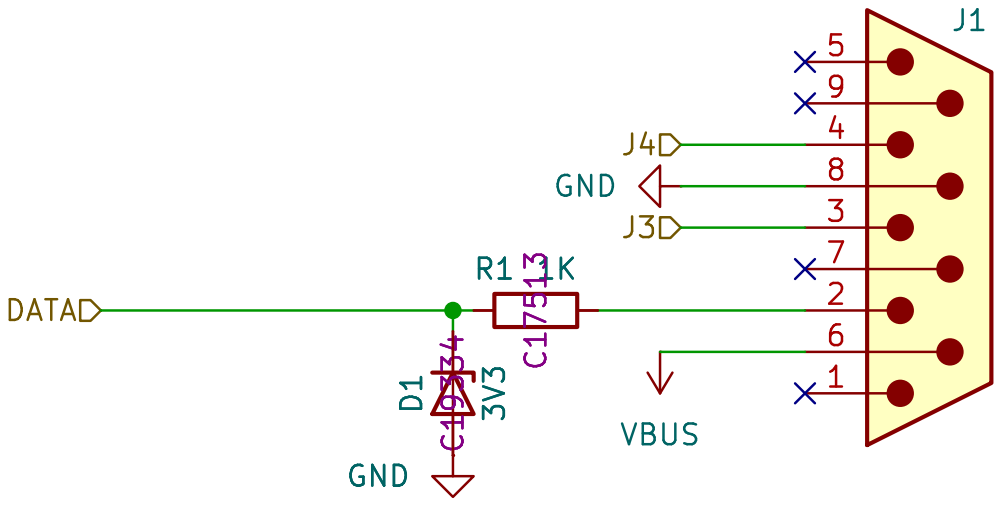
[picture p133: page 2]

https://github.com/xtremespb/frank

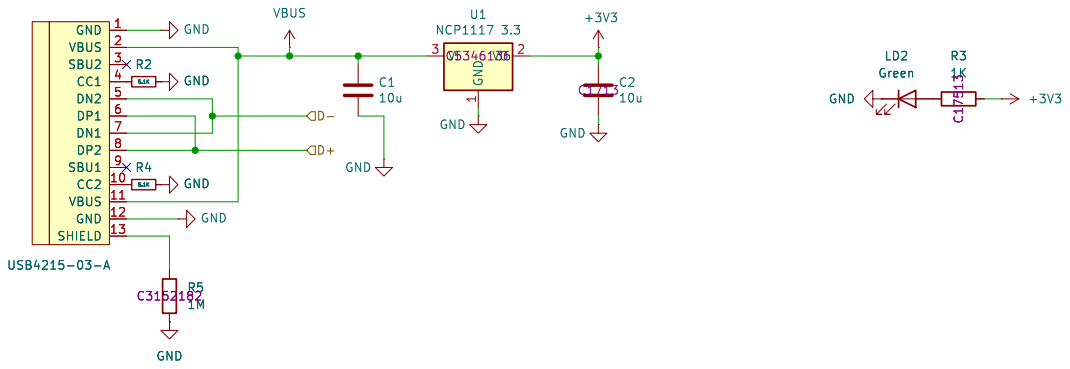
[picture p134: page 3]

https://github.com/xtremespb/frank

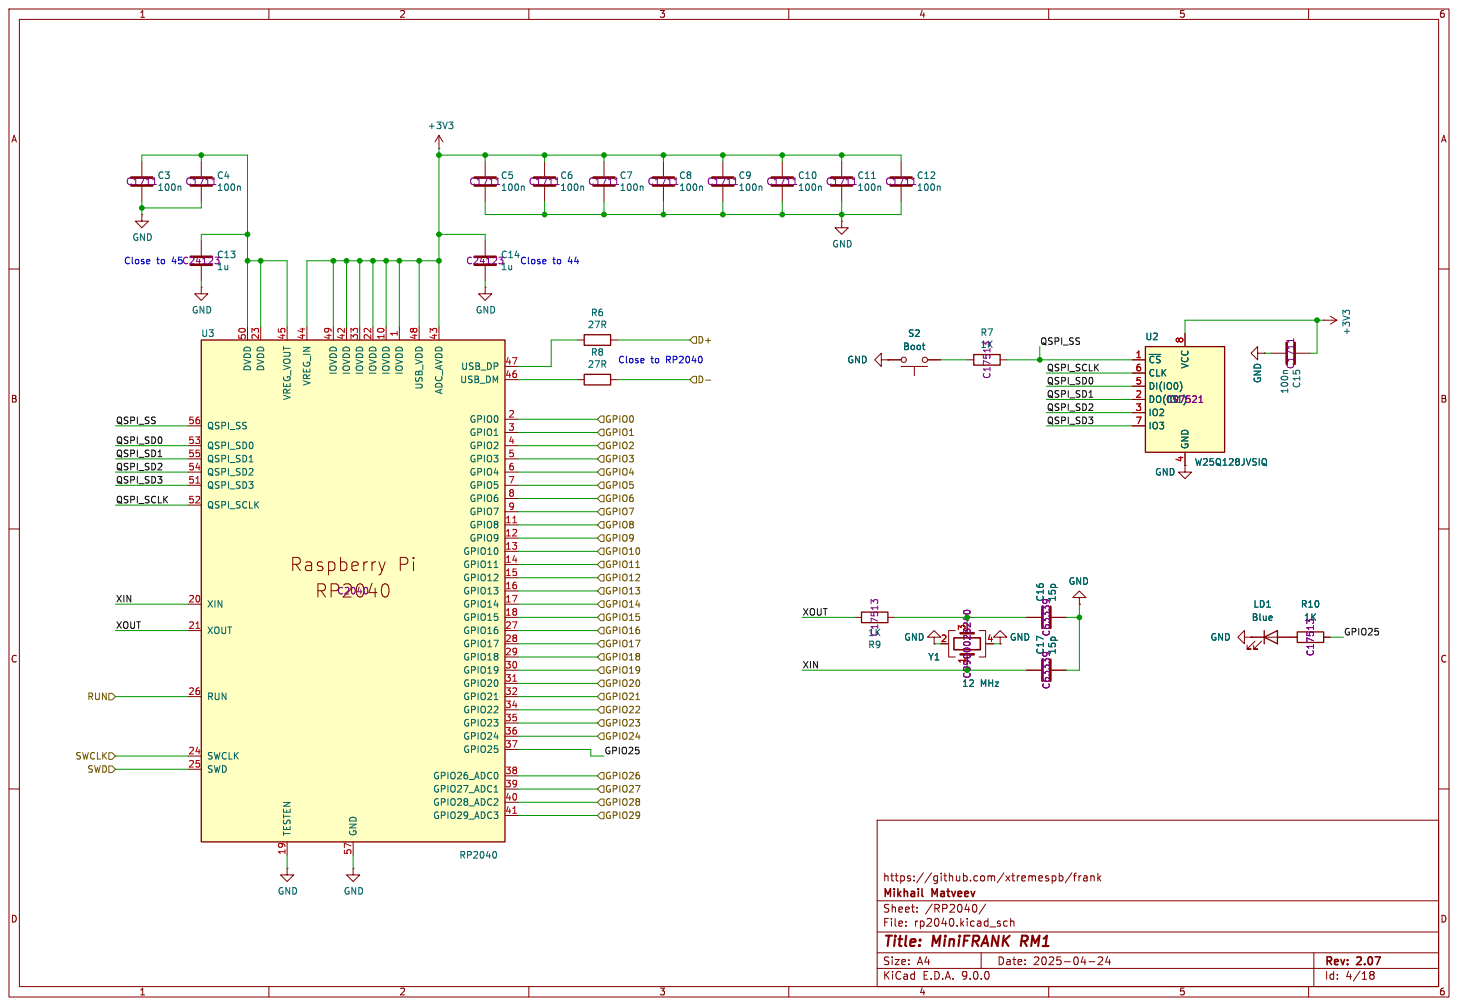
[picture p135: page 4]

https://github.com/xtremespb/frank GND

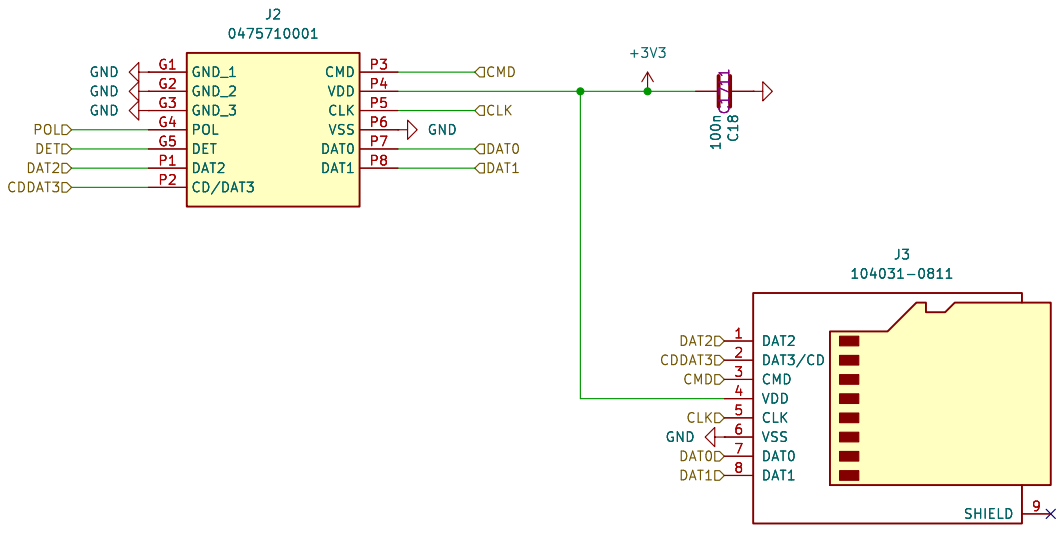
[picture p136: page 5]

https://github.com/xtremespb/frank GND

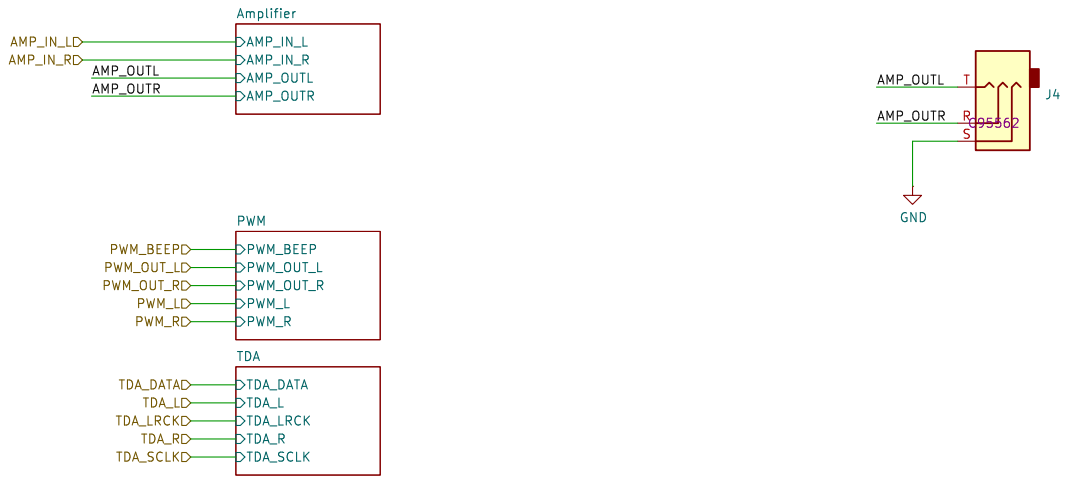
[picture p137: page 6]

https://github.com/xtremespb/frank

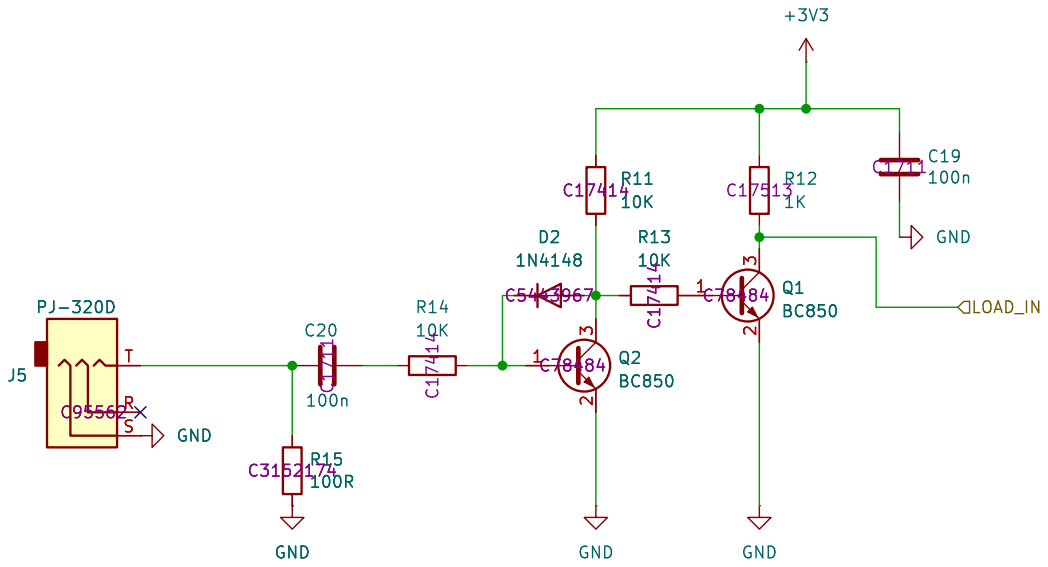
[picture p138: page 7]

https://github.com/xtremespb/frank

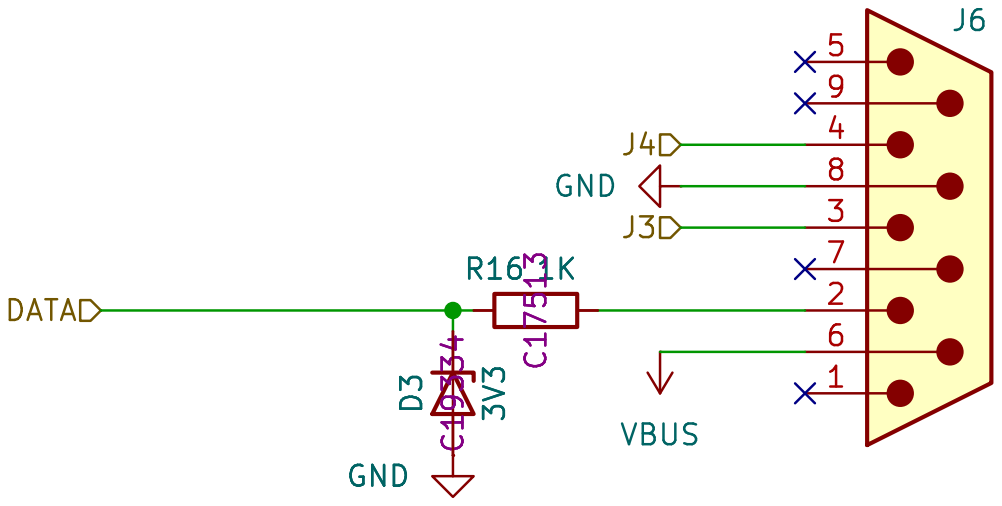
[picture p139: page 8]

https://github.com/xtremespb/frank

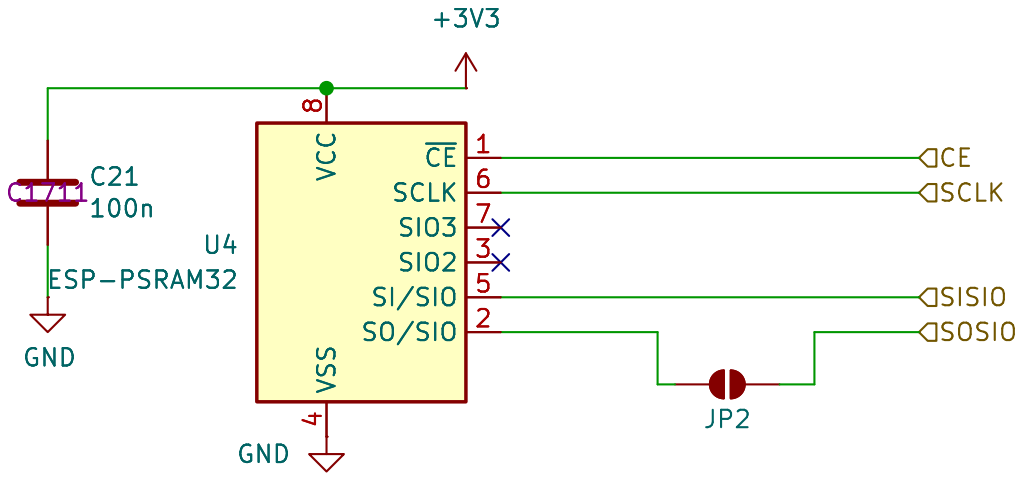
[picture p140: page 9]

4 ~{CE}1 SCLK 6 SIO3 7 SIO2 3 SI/SIO 5 SO/SIO 2 +3V3

4 ~{CE}1 SCLK 6 SIO3 7 SIO2 3 SI/SIO 5 SO/SIO 2 U4 ESP-PSRAM32 GND

https://github.com/xtremespb/frank

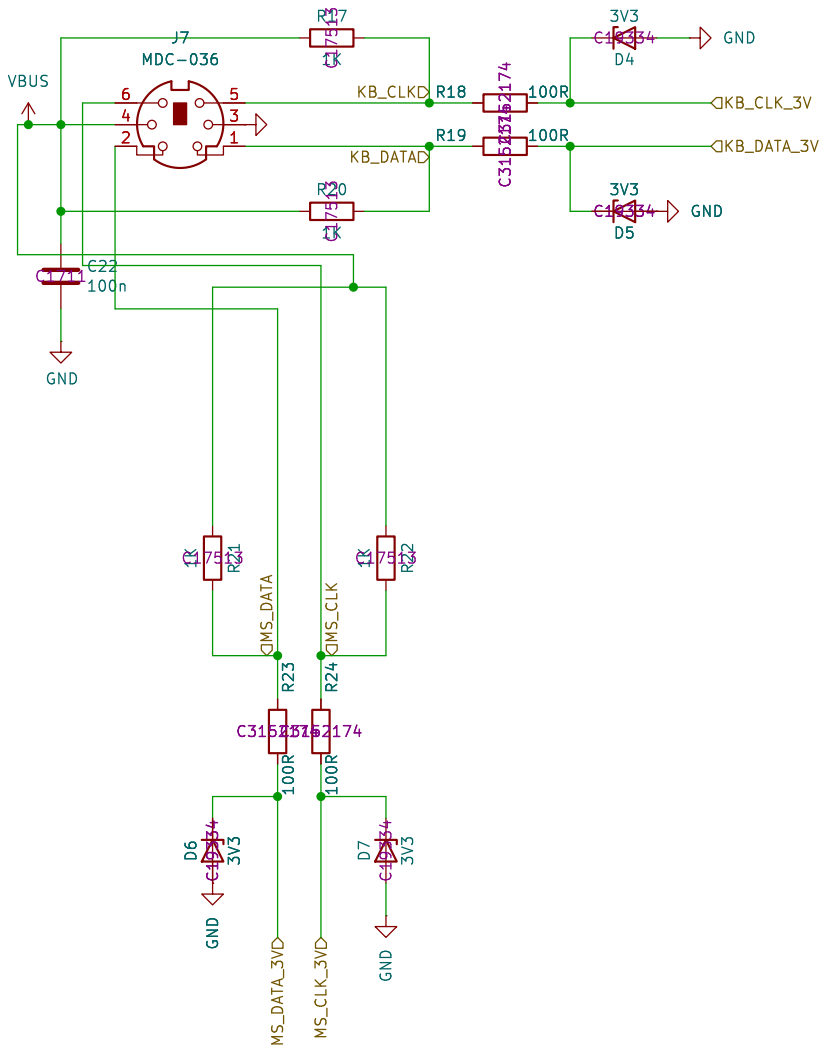
[picture p141: page 10]

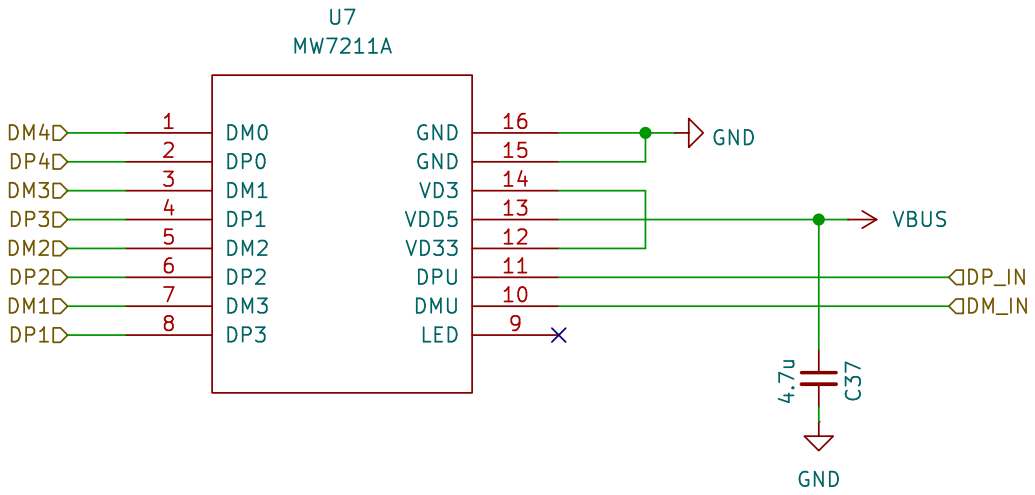
[picture p142: page 11]

https://github.com/xtremespb/frank

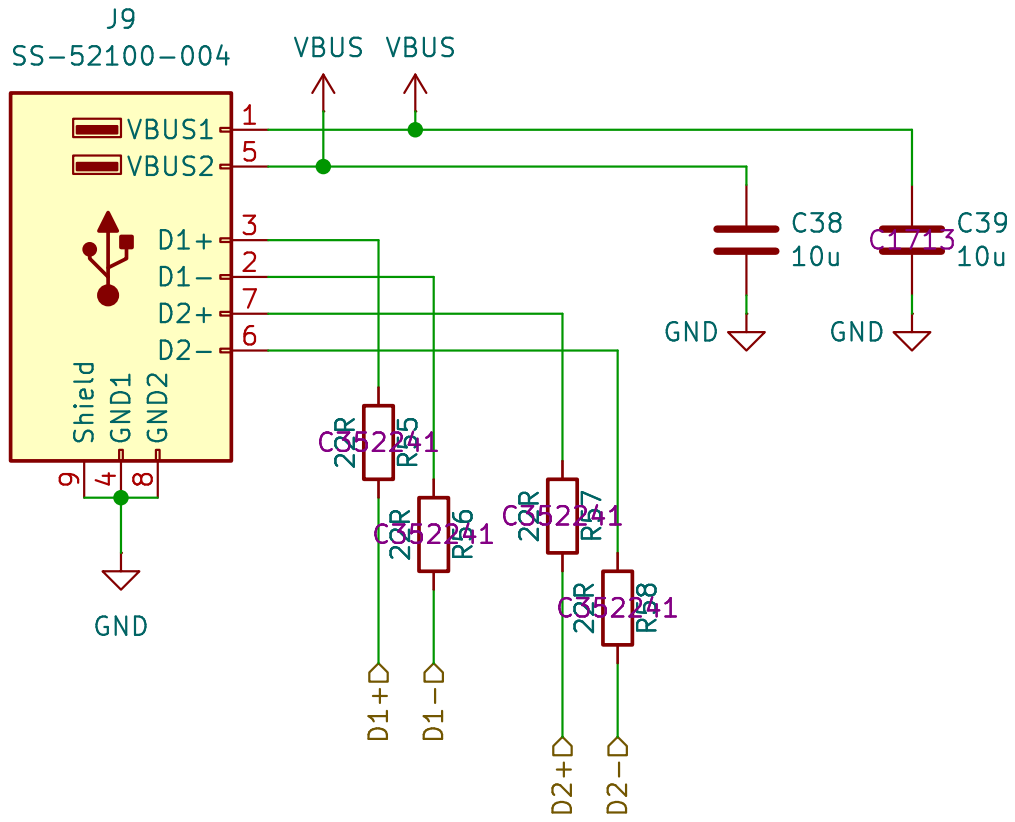
[picture p143: page 12]

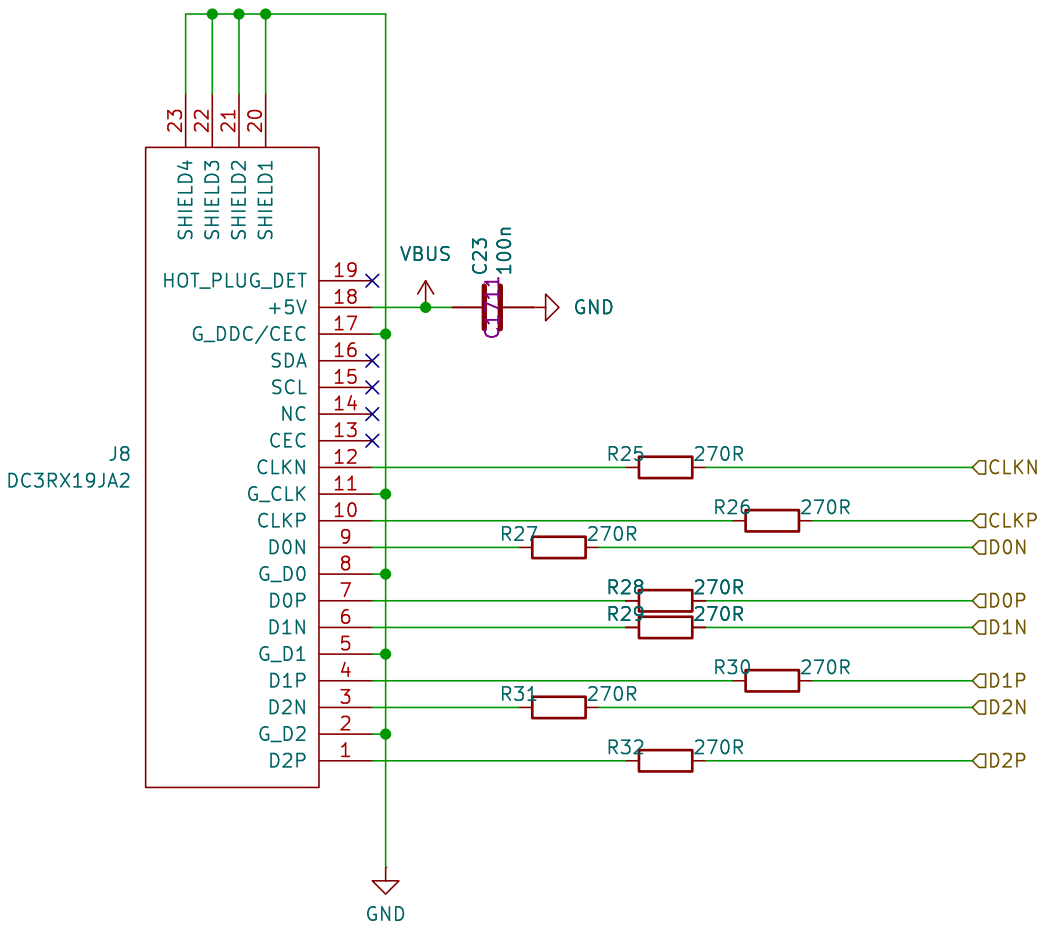
[picture p144: page 13]

https://github.com/xtremespb/frank

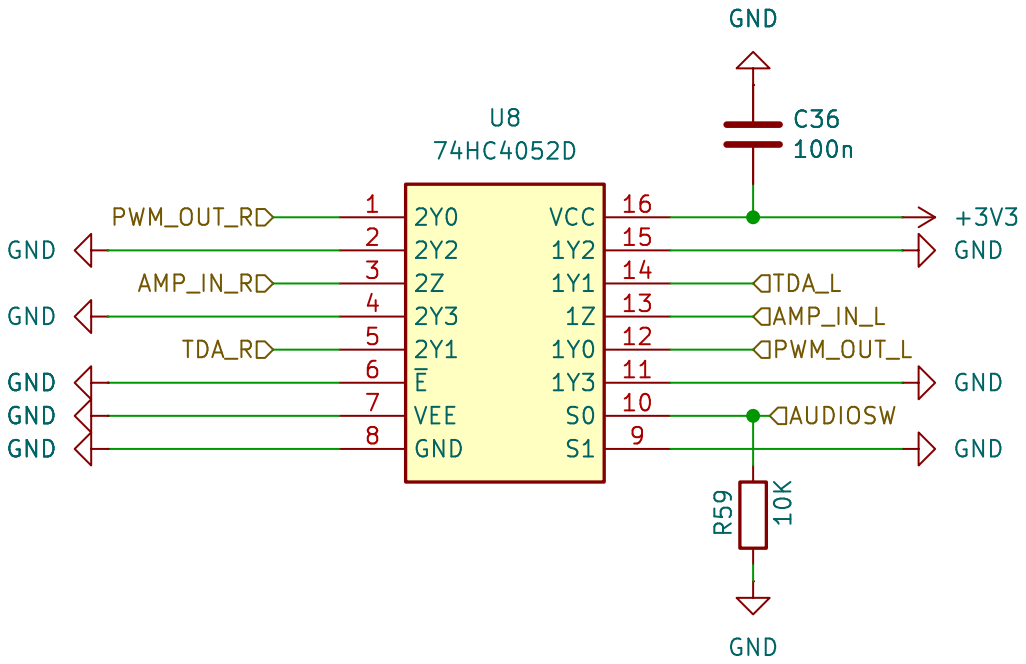
[picture p145: page 14]

+3V3 GND GND GND GND GND

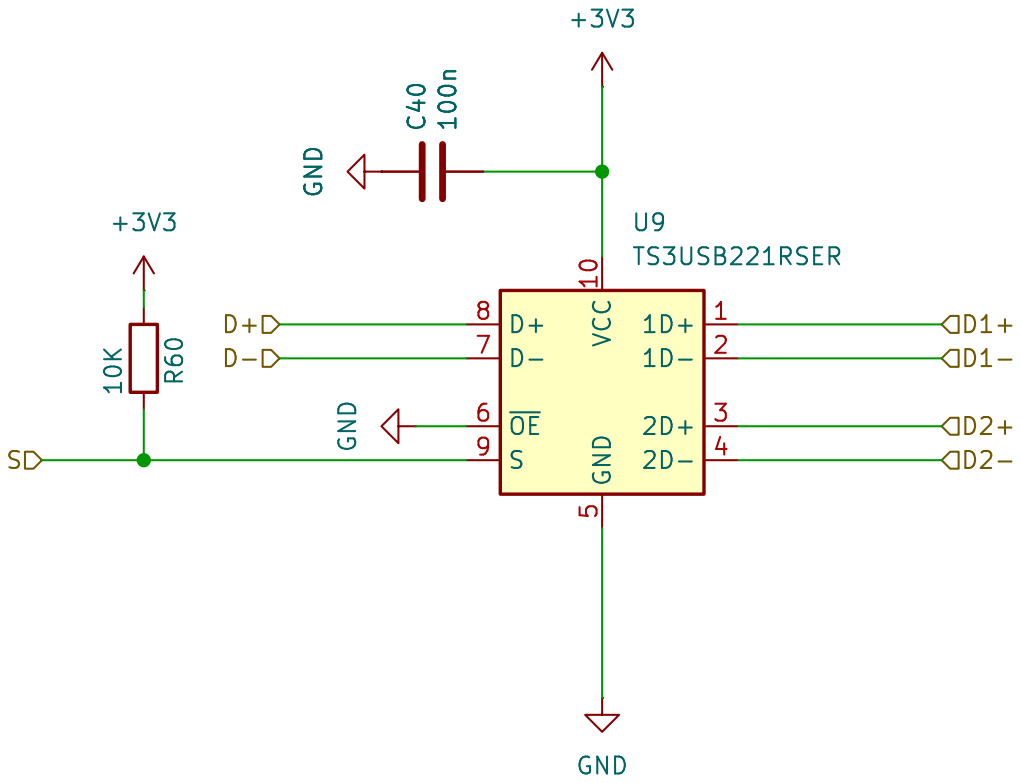
[picture p146: page 15]

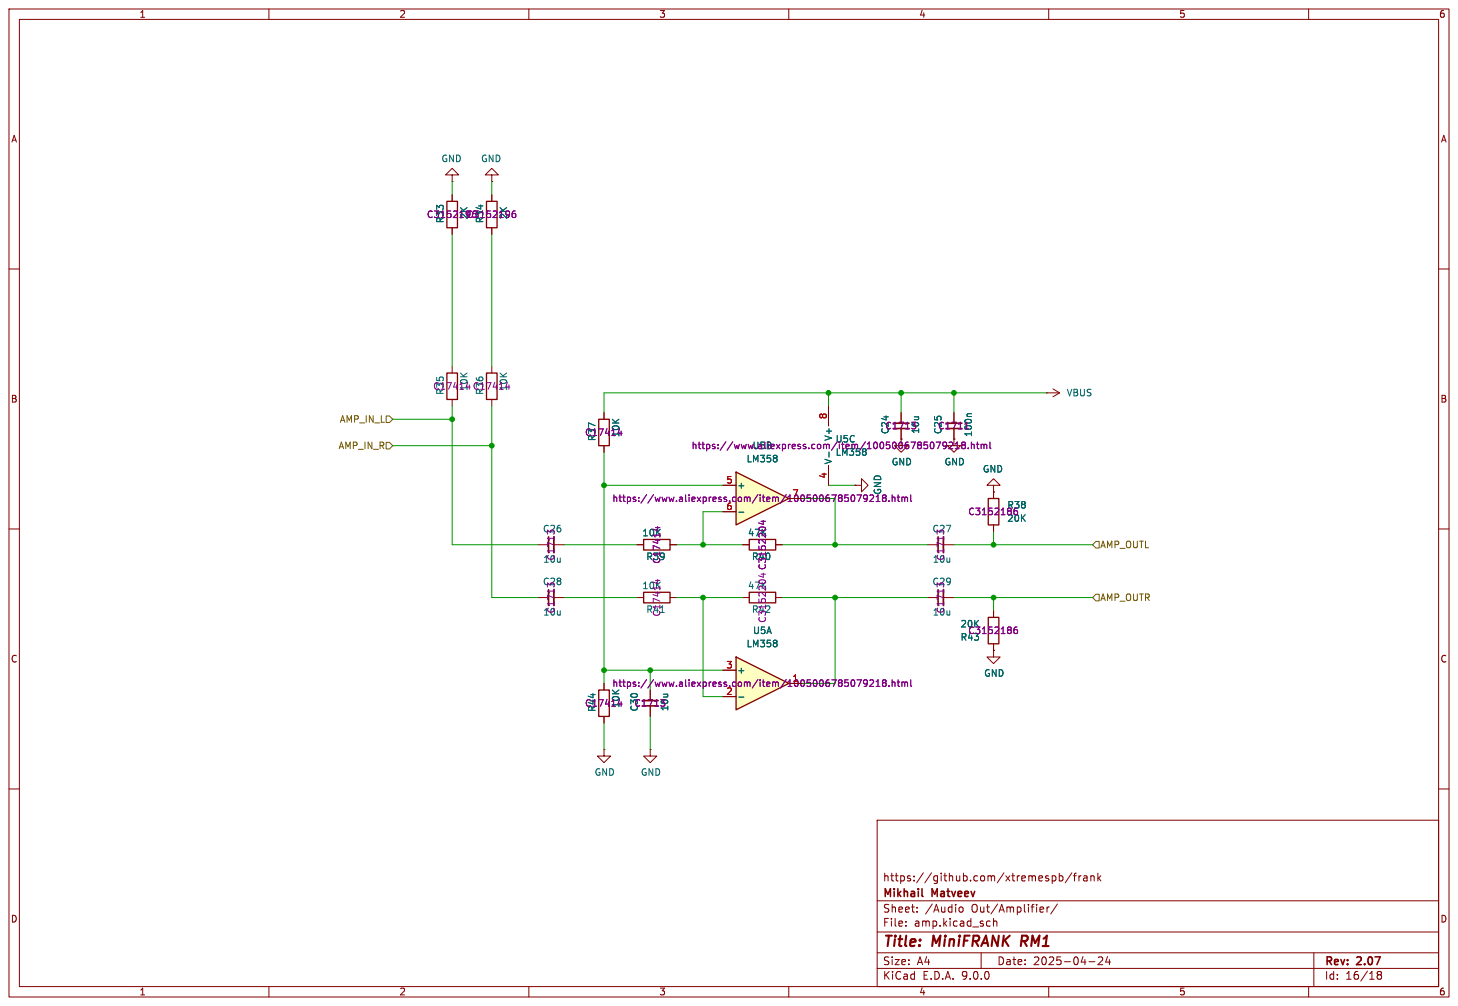
[picture p147: page 16]

LM358 https://www.aliexpress.com/item/1005006785079218.html V+
LM358 https://www.aliexpress.com/item/1005006785079218.html C27

https://www.aliexpress.com/item/1005006785079218.html +

https://www.aliexpress.com/item/1005006785079218.html R41

https://github.com/xtremespb/frank

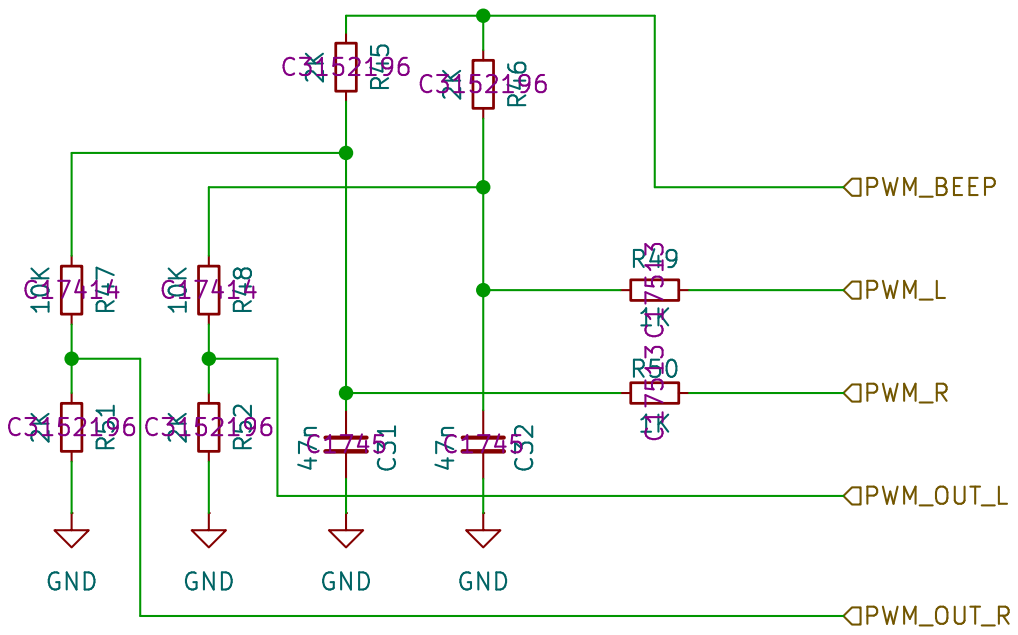
[picture p148: page 17]

https://github.com/xtremespb/frank R49

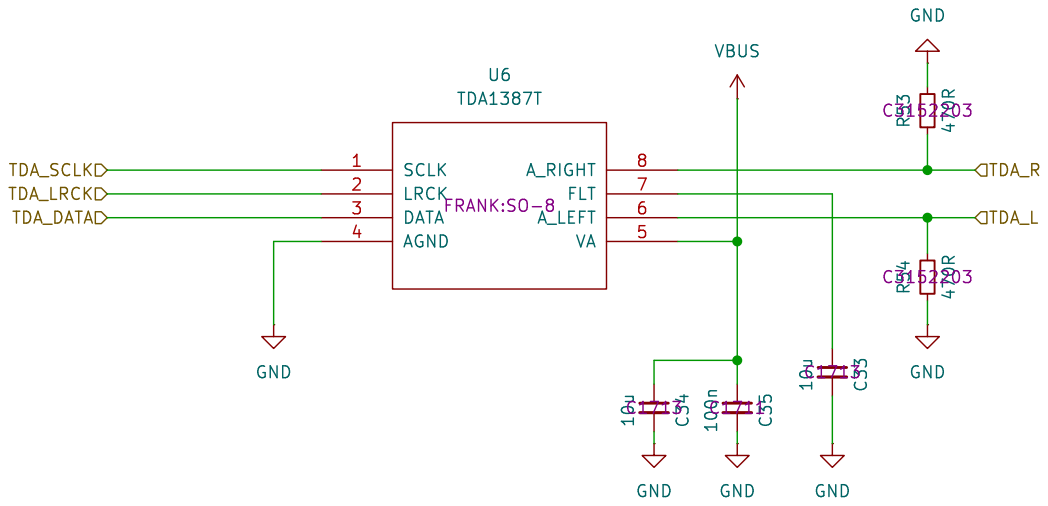
[picture p149: page 18]
