ponikrf/frank/hardware/turbofrank/DOCS/1_05/assembly.pdf

1 | 2 | 3 | 4 | 5 | 6

A

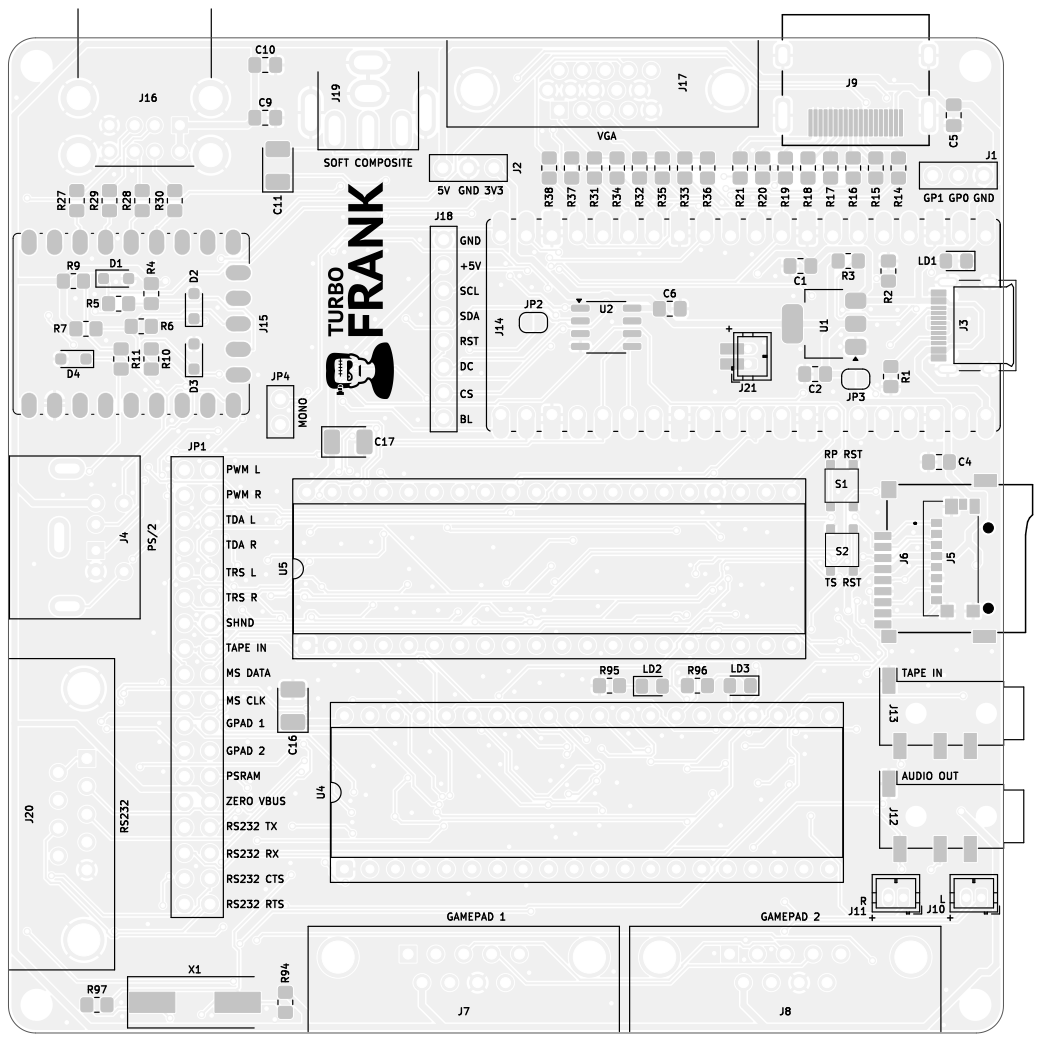
[picture p150: page 1]

https://github.com/xtremespb/frank Black And White TOP - Page 1/4

File: turbofrank.kicad_pcb Sheet: Black And White TOP Mikhail Matveev

R116 R68 R79 R22 C26 | R104 C30R86 | U10 | R42 R39 C34R107 1 | 2 | 3 | 4 | 5 | 6 1 | 2 | 3 | 4 | 5 | 6 ABCD | ABCD Date: 2025-04-05 KiCad E.D.A. 9.0.0 Size: A4 | Rev: 1.05

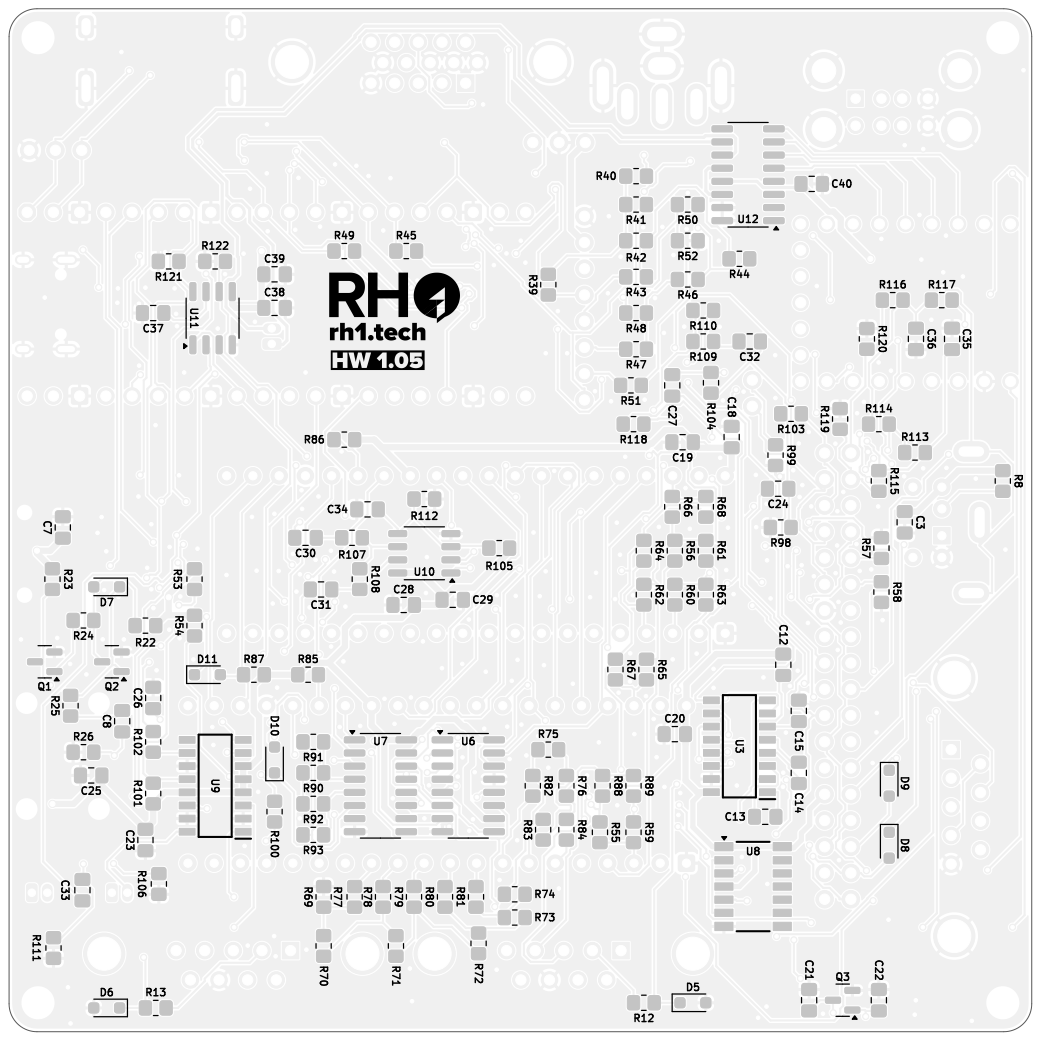
[picture p151: page 2]

https://github.com/xtremespb/frank Black And White BOT - Page 2/4

File: turbofrank.kicad_pcb Sheet: Black And White BOT Mikhail Matveev

1 | 2 | 3 | 4 | 5 | 6

A

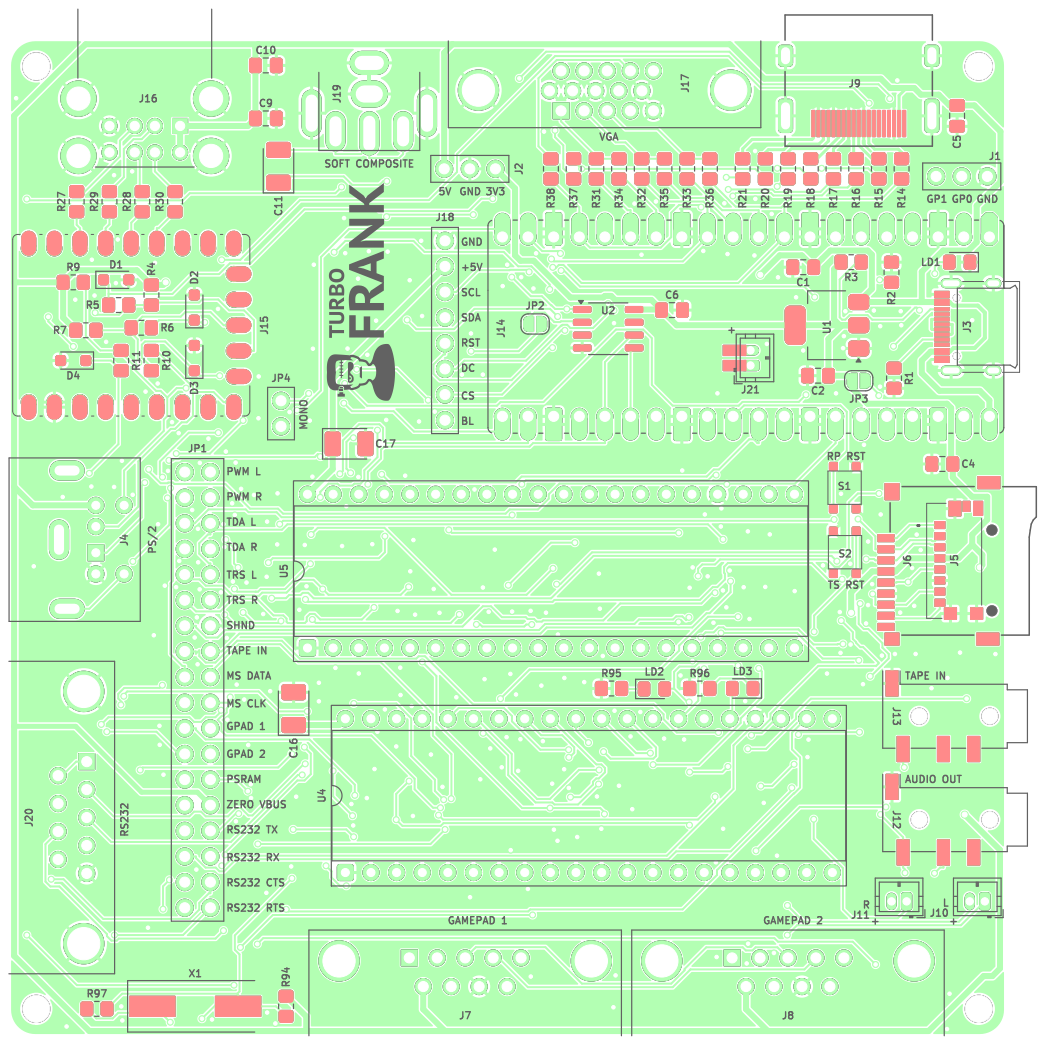
[picture p152: page 3]

R116 R68 R79 R22 C26 | R104 C30R86 | U10 | R42 R39 C34R107 1 | 2 | 3 | 4 | 5 | 6 1 | 2 | 3 | 4 | 5 | 6 ABCD | ABCD Date: 2025-04-05 KiCad E.D.A. 9.0.0 Size: A4 | Rev: 1.05
R40 | 300R

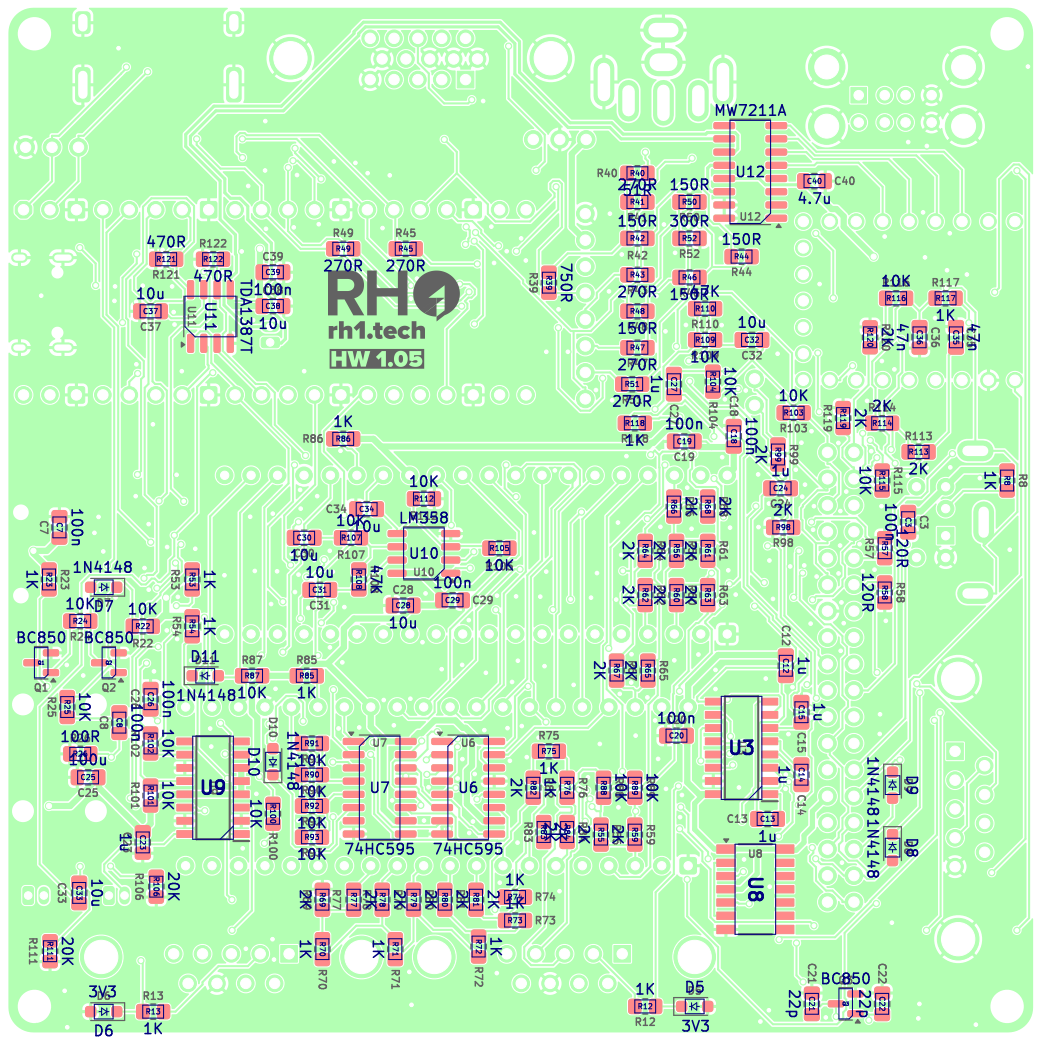
[picture p153: page 4]

https://github.com/xtremespb/frank Colored BOT - Page 4/4

File: turbofrank.kicad_pcb Sheet: Colored BOT Mikhail Matveev
