ponikrf/frank/hardware/turbofrank/DOCS/1_05/turbofrank.pdf

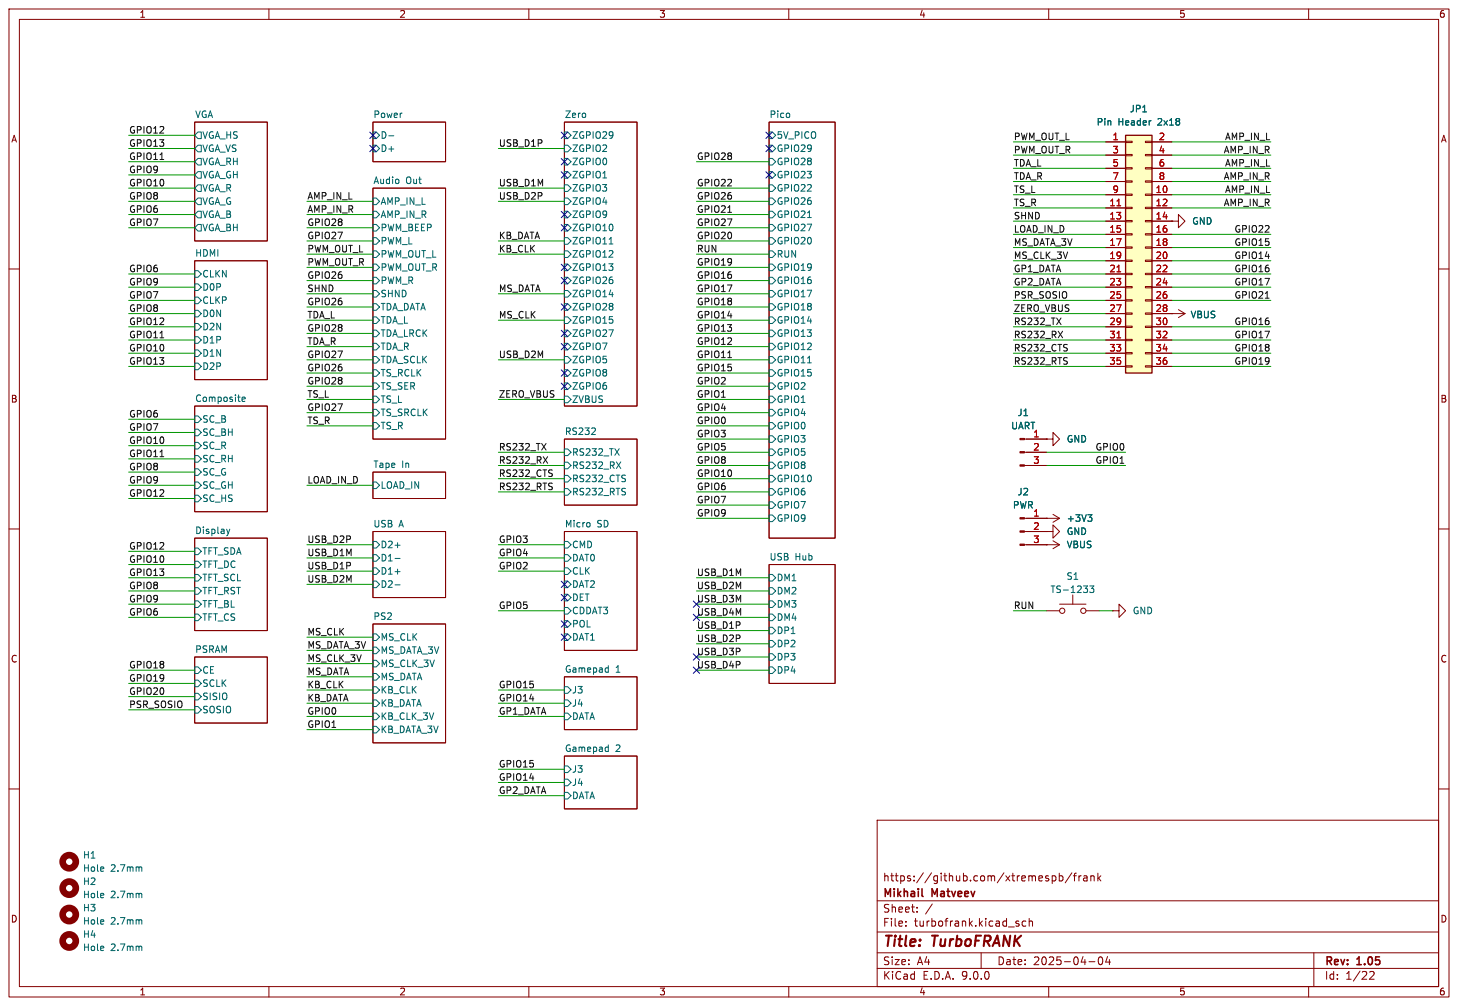
[picture p154: page 1]

Tape In D2+ D1- D1+ D2- USB A D- D+ Power
USB_D2P GP2_DATA GP1_DATA USB_D2M

DAT0 CLK DAT2 DET CDDAT3 POL DAT1 Micro SD

https://github.com/xtremespb/frank

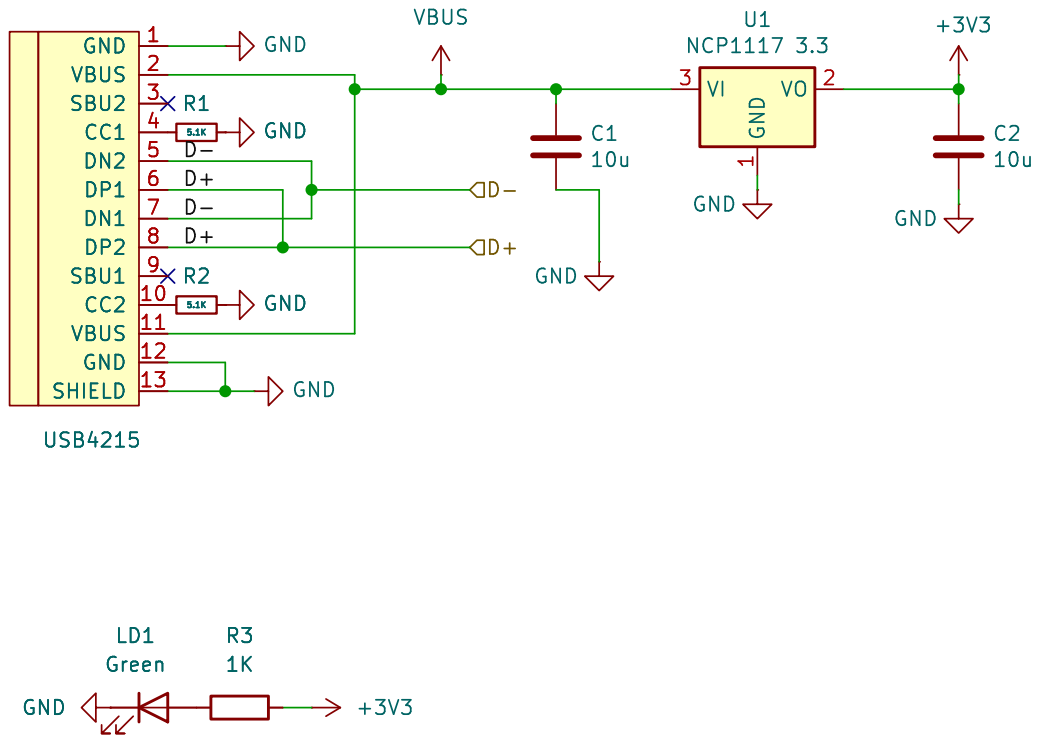
[picture p155: page 2]

https://github.com/xtremespb/frank

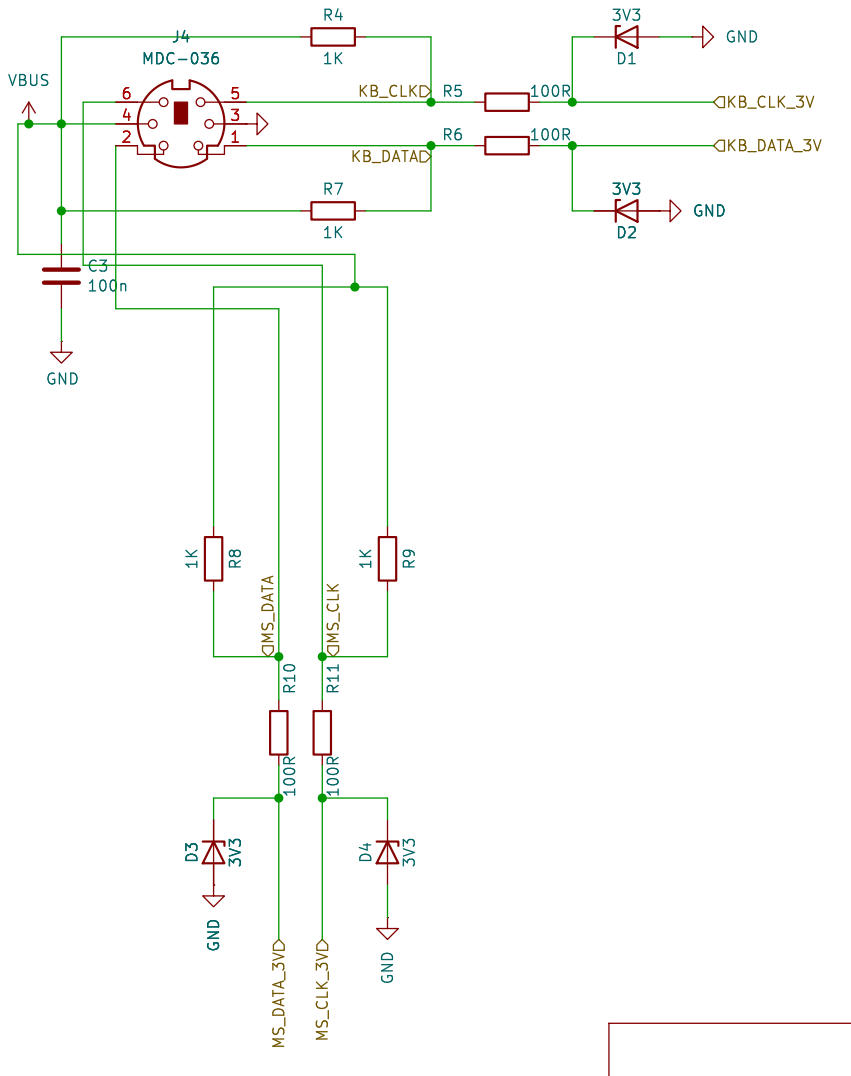
[picture p156: page 3]

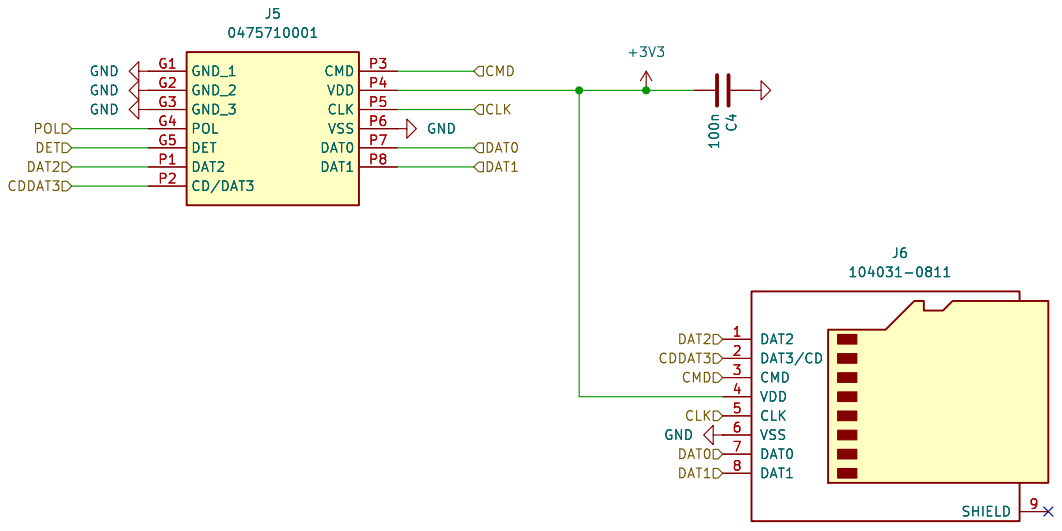
[picture p157: page 4]

https://github.com/xtremespb/frank

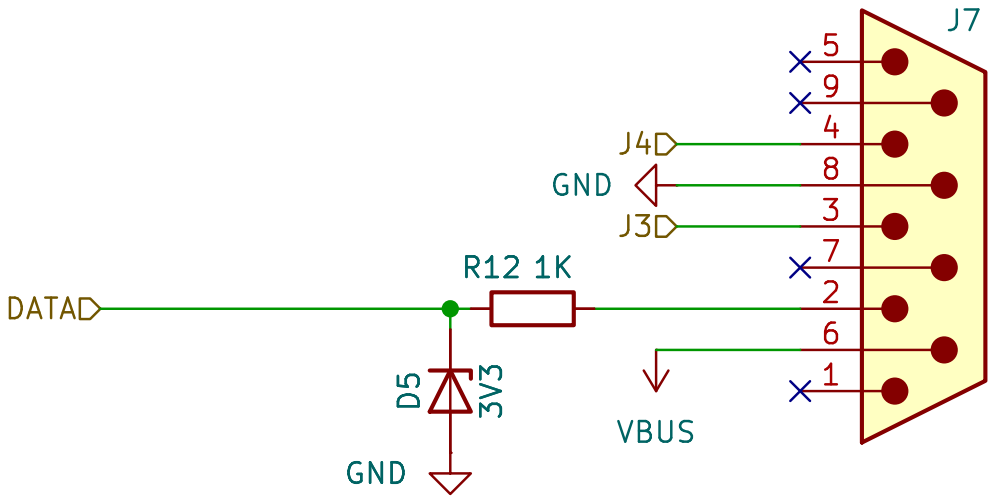
[picture p158: page 5]

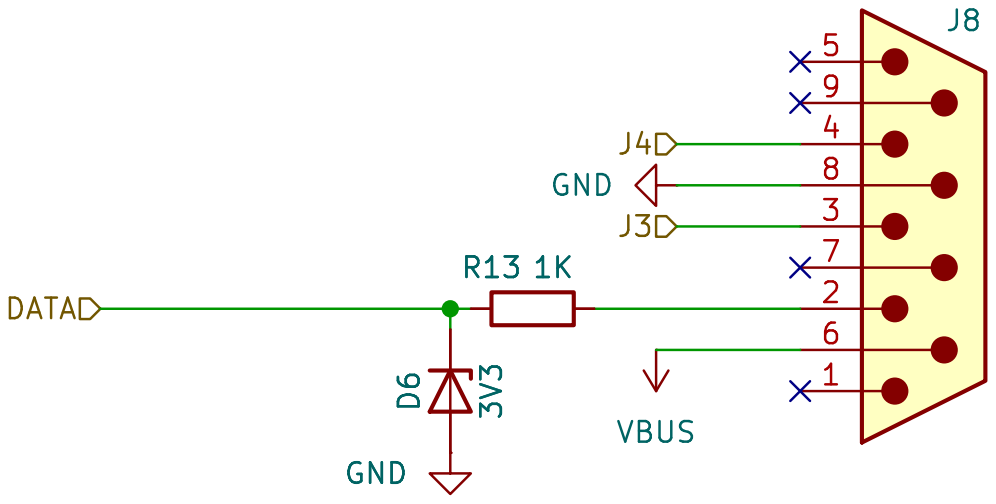
[picture p159: page 6]

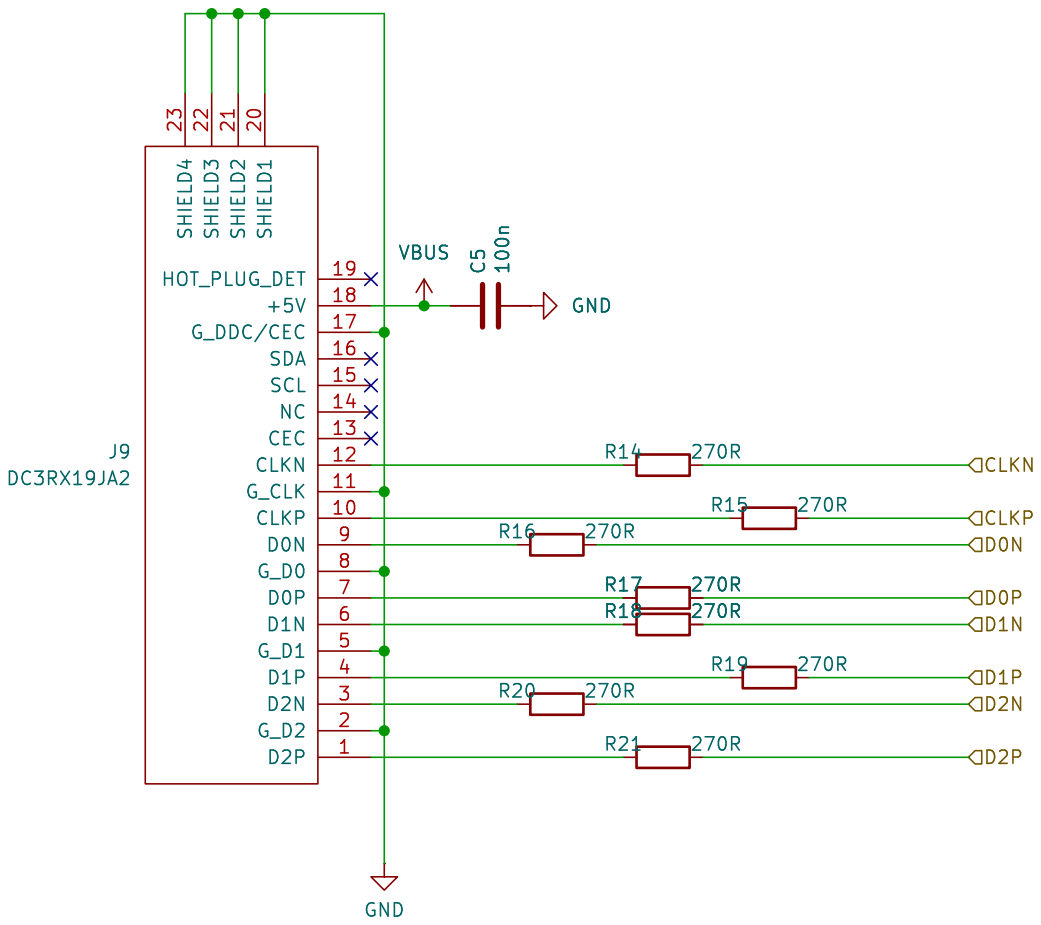
[picture p160: page 7]

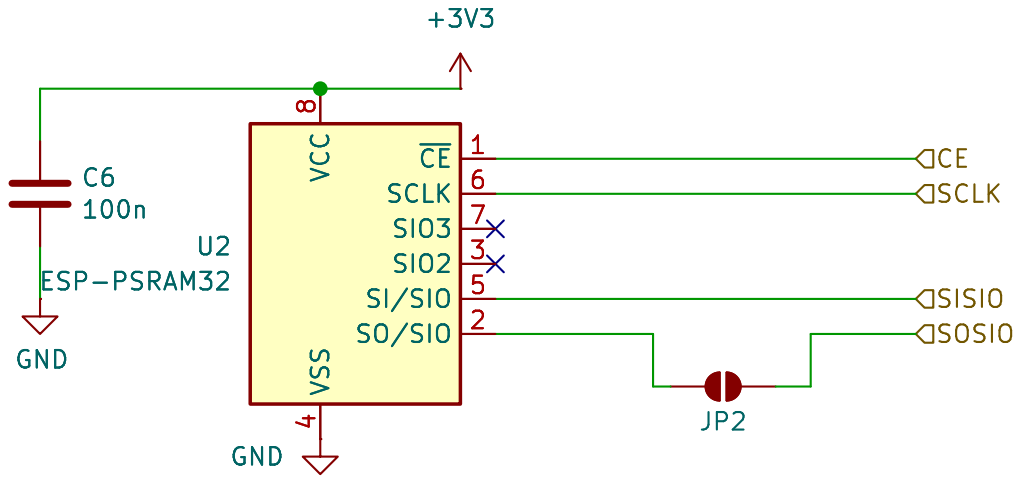
[picture p161: page 8]

4 ~{CE}1 SCLK 6 SIO3 7 SIO2 3 SI/SIO 5 SO/SIO 2 U2 ESP-PSRAM32 C6

4 ~{CE}1 SCLK 6 SIO3 7 SIO2 3 SI/SIO 5 SO/SIO 2 GND

https://github.com/xtremespb/frank

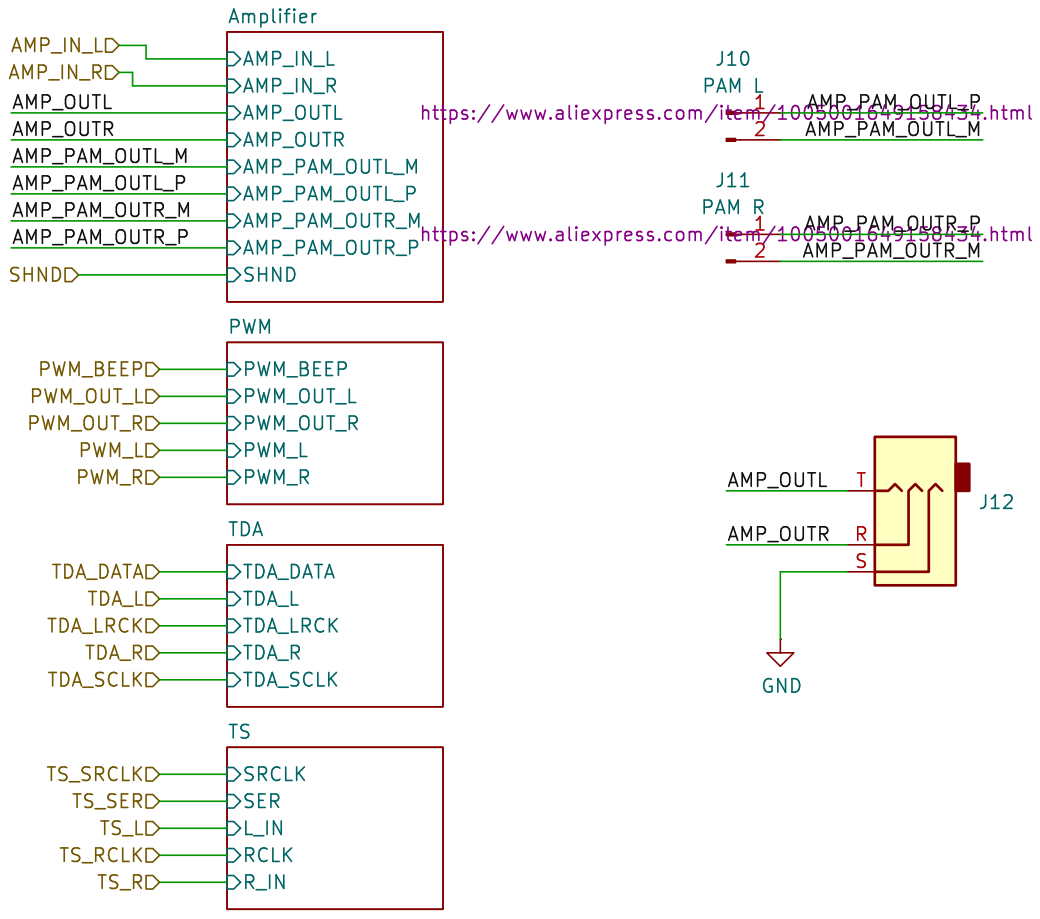
[picture p162: page 9]

https://www.aliexpress.com/item/1005001649158434.html 1

https://github.com/xtremespb/frank

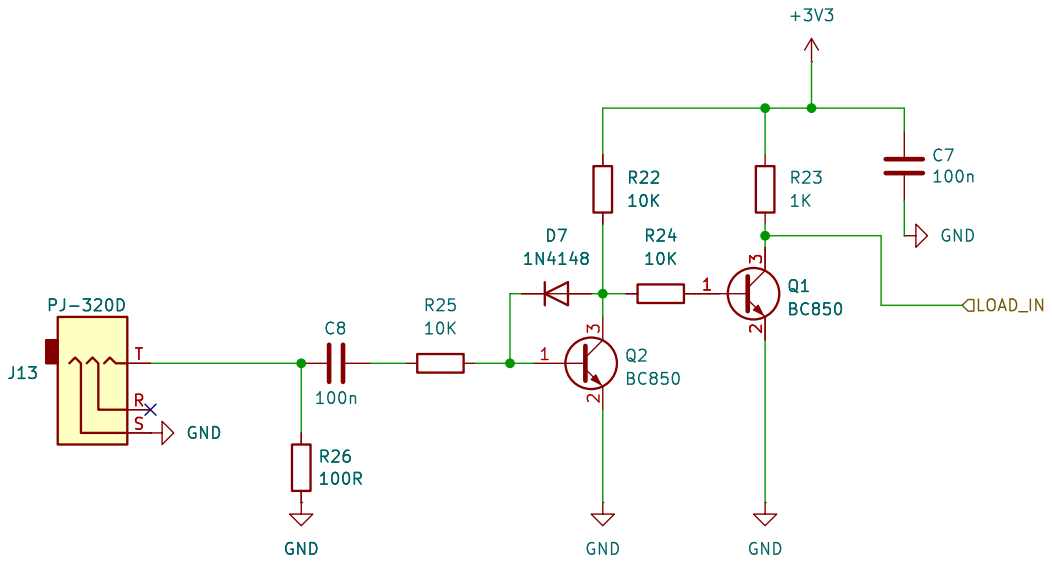
[picture p163: page 10]

https://github.com/xtremespb/frank GND

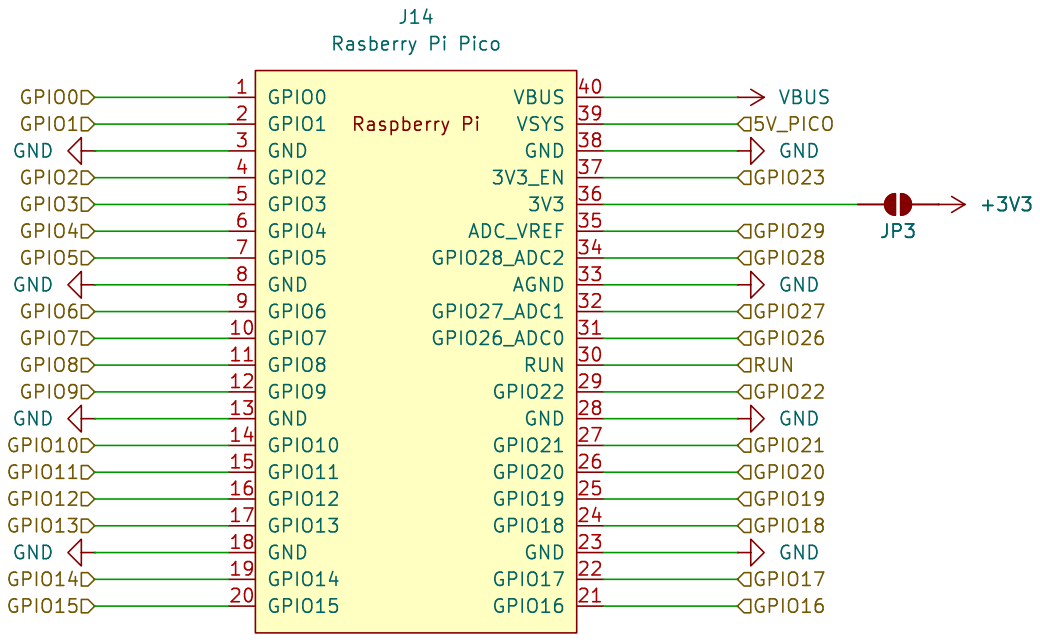
[picture p164: page 11]

VBUS GND GND GND GND

https://github.com/xtremespb/frank

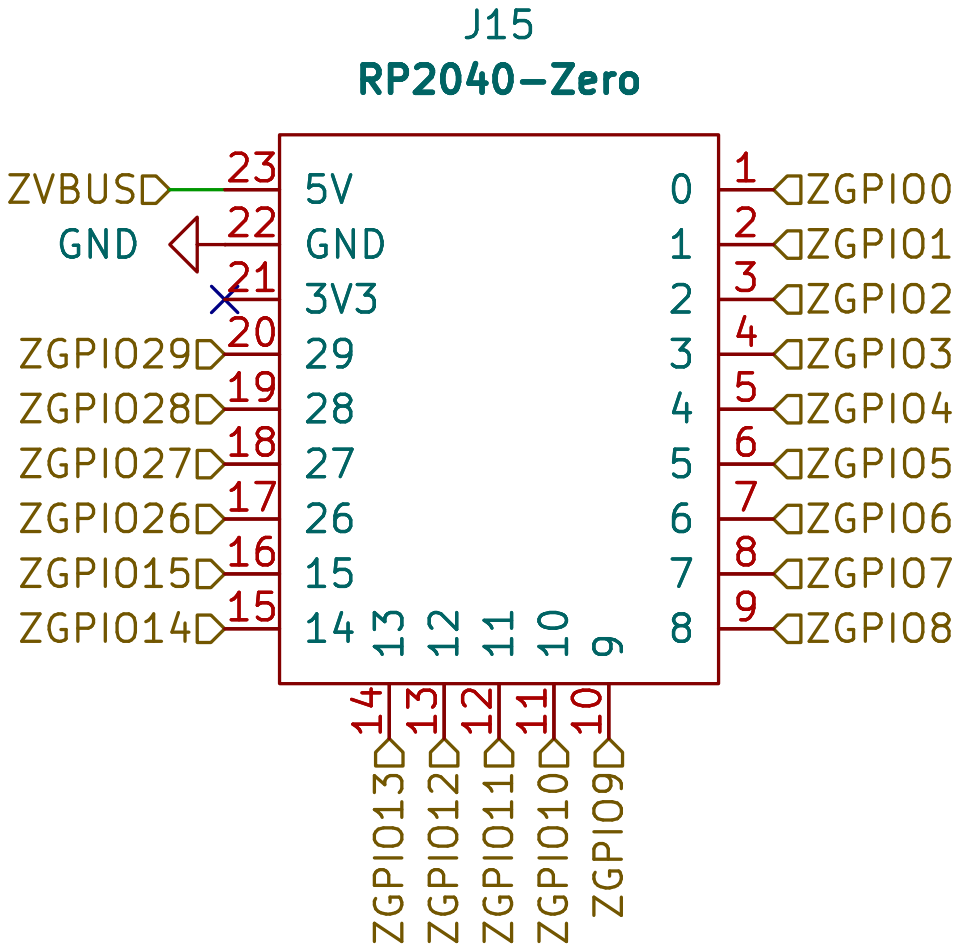
[picture p165: page 12]

https://github.com/xtremespb/frank

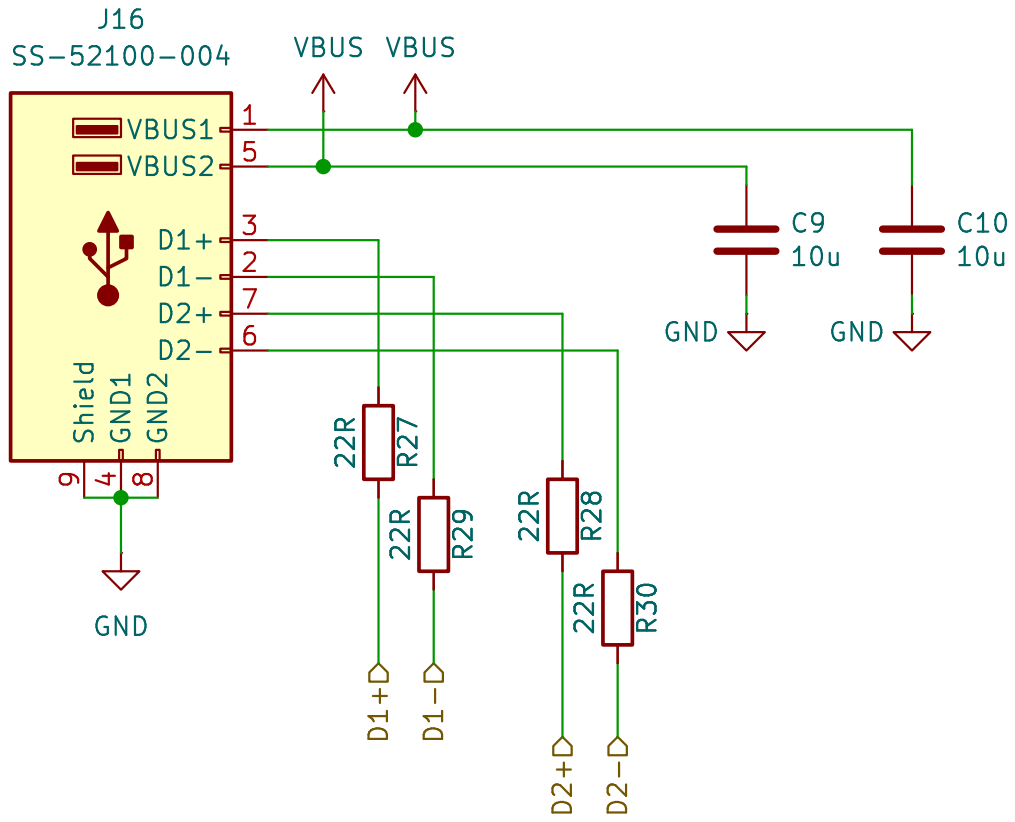
[picture p166: page 13]

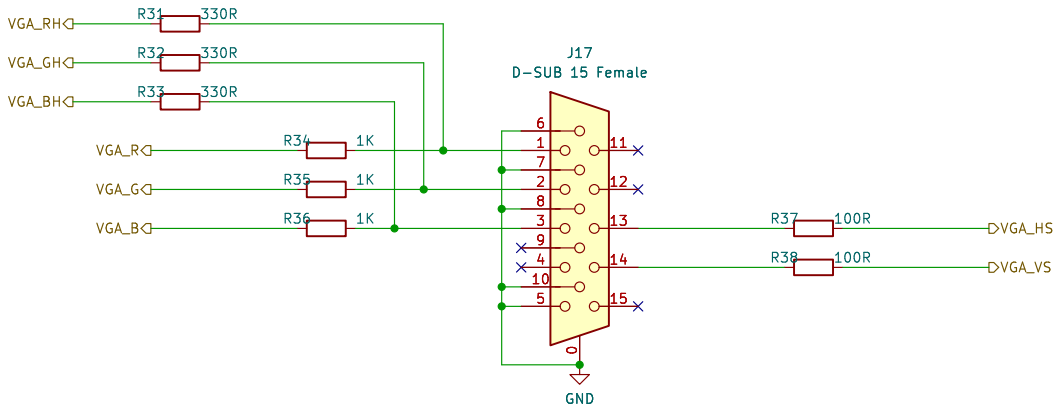
[picture p167: page 14]

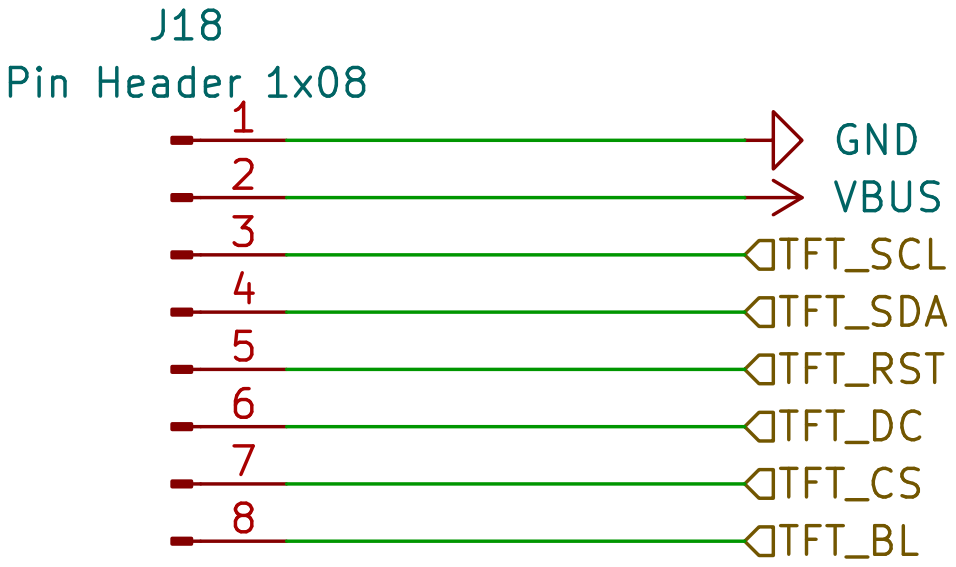
[picture p168: page 15]

https://github.com/xtremespb/frank GND
VBUS

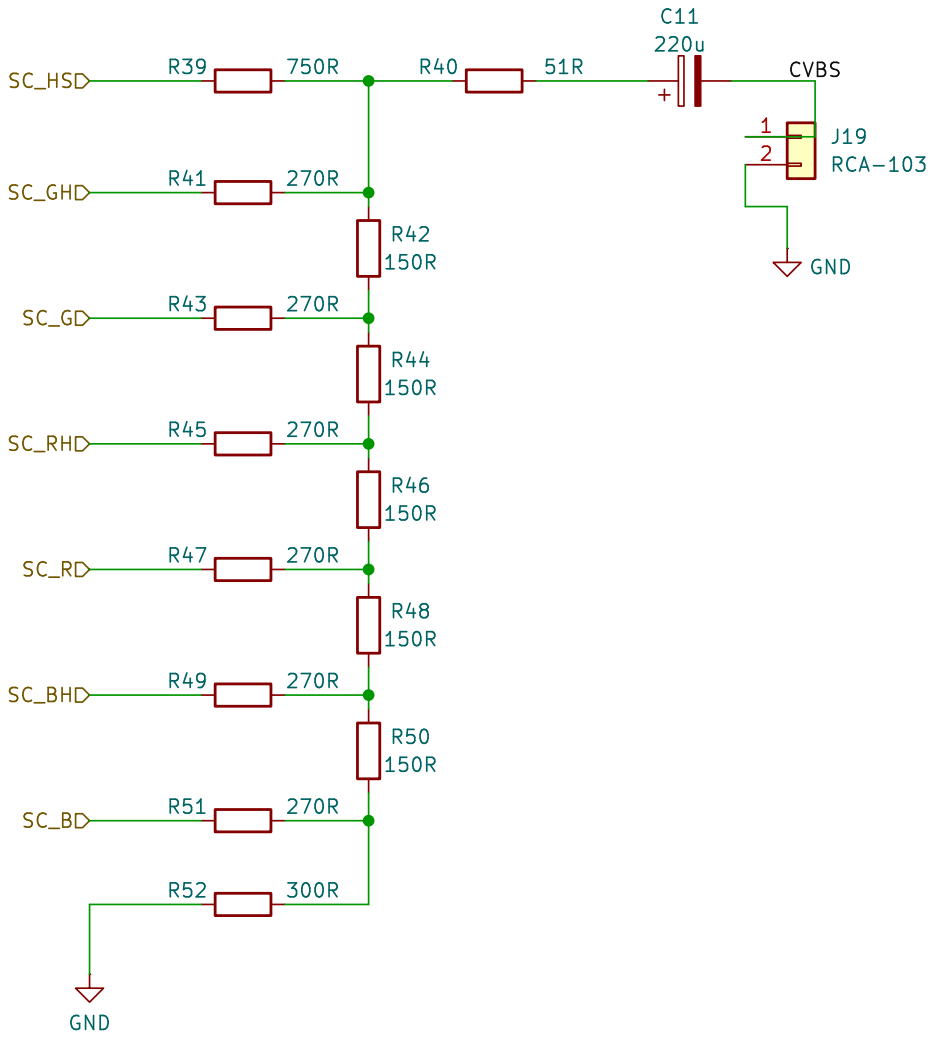
[picture p169: page 16]

https://github.com/xtremespb/frank

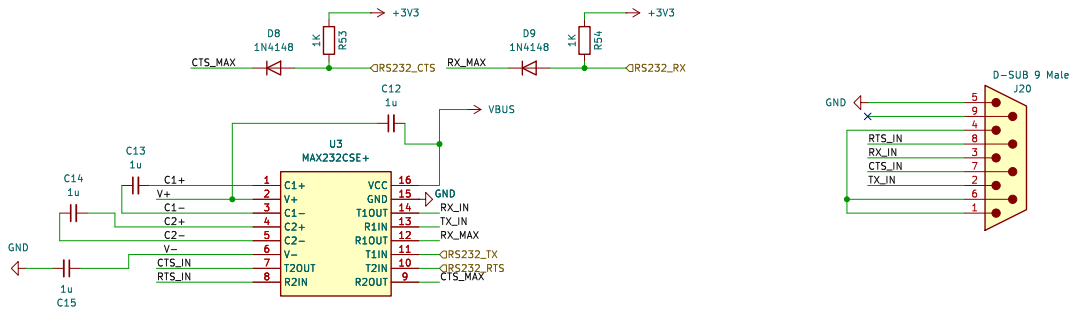
[picture p170: page 17]

https://github.com/xtremespb/frank R53 1K

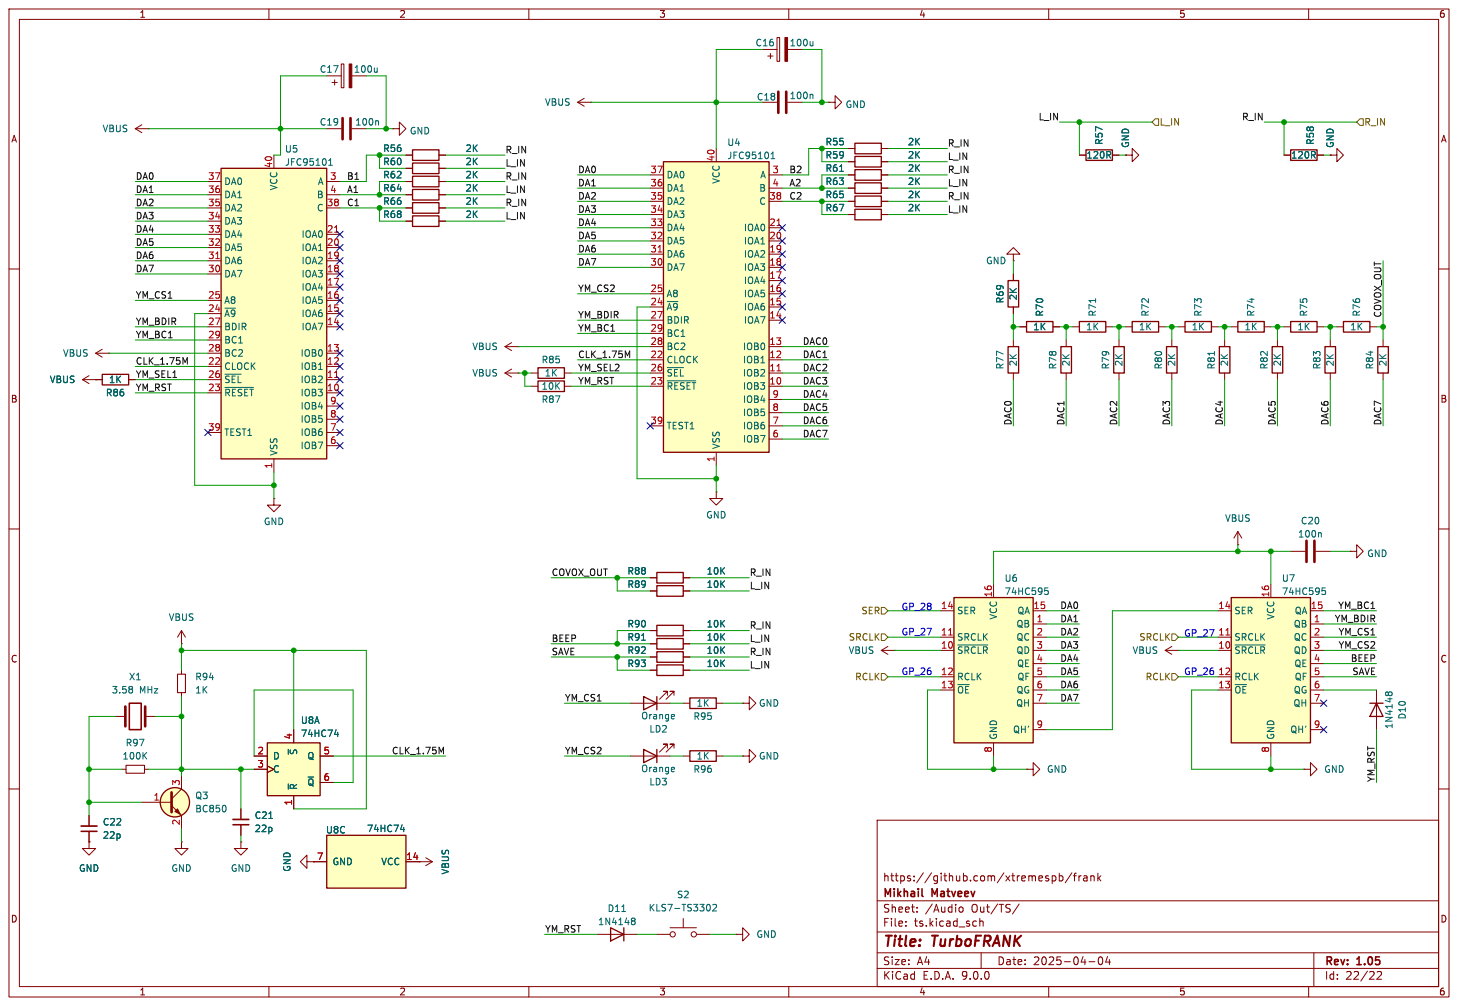
[picture p171: page 18]

https://github.com/xtremespb/frank

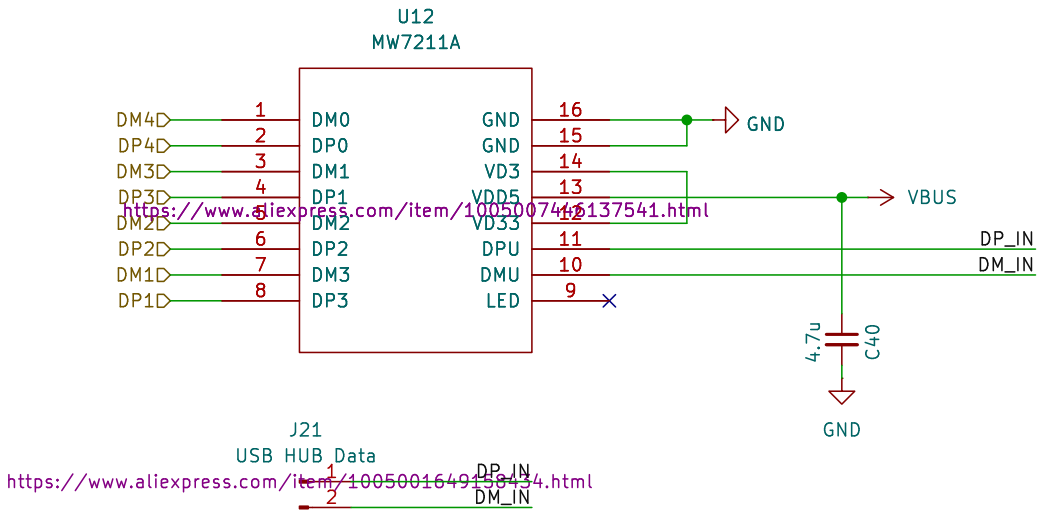
[picture p172: page 19]

https://github.com/xtremespb/frank

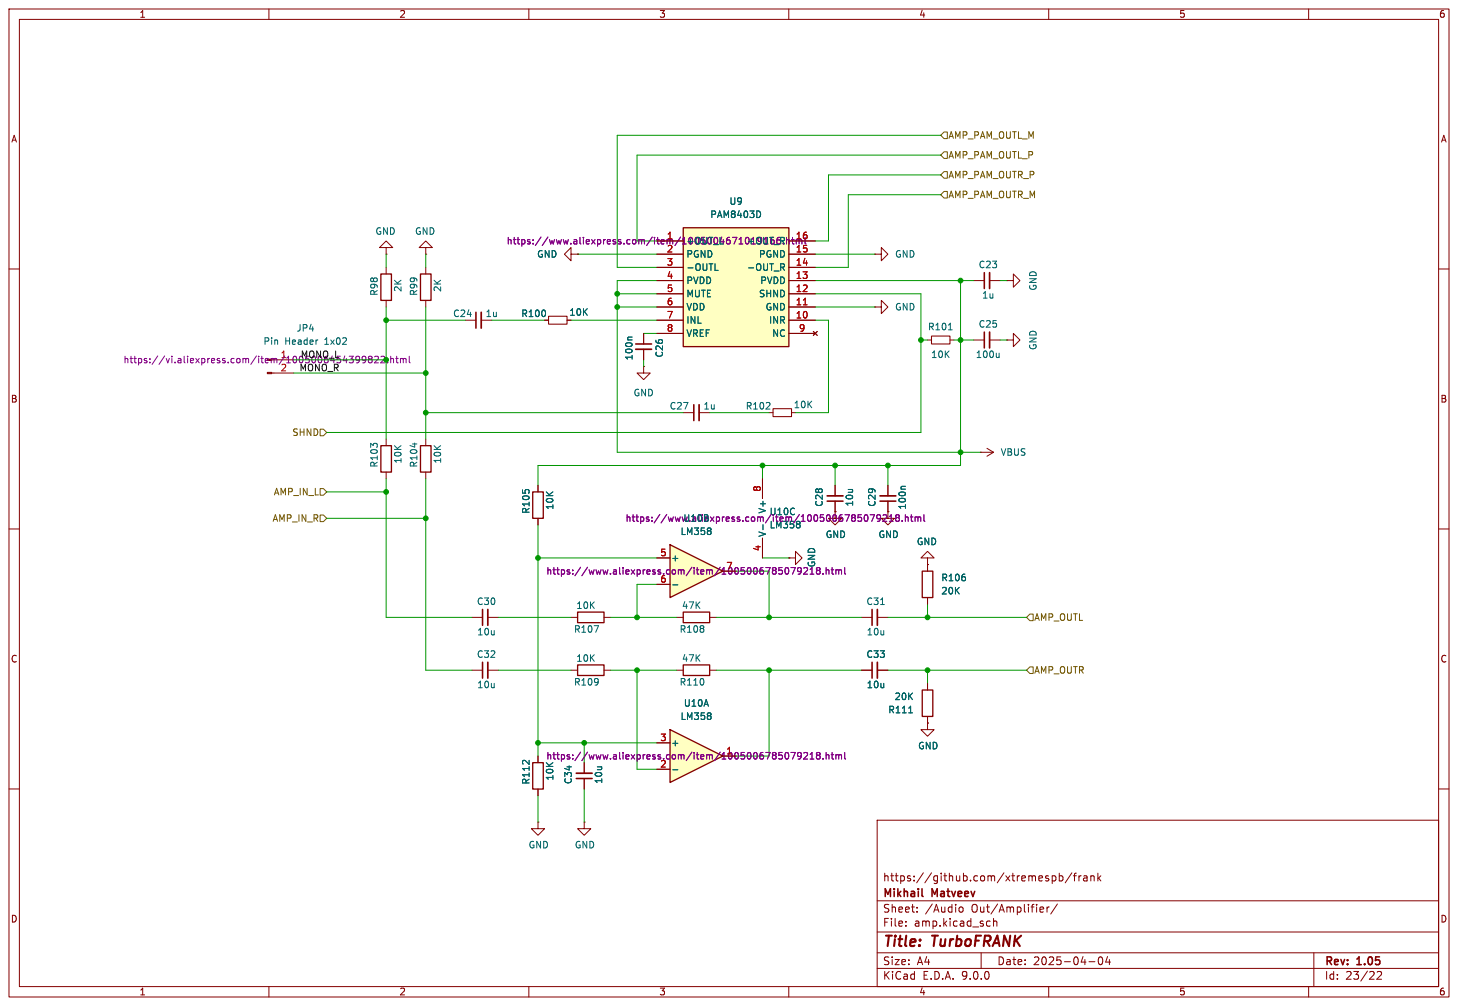
[picture p173: page 20]

LM358 https://www.aliexpress.com/item/1005006785079218.html V+
LM358 https://www.aliexpress.com/item/1005006785079218.html +

https://www.aliexpress.com/item/1005006785079218.html +
https://www.aliexpress.com/item/1005006785079218.html R108

https://www.aliexpress.com/item/1005006785079218.html R107

https://github.com/xtremespb/frank

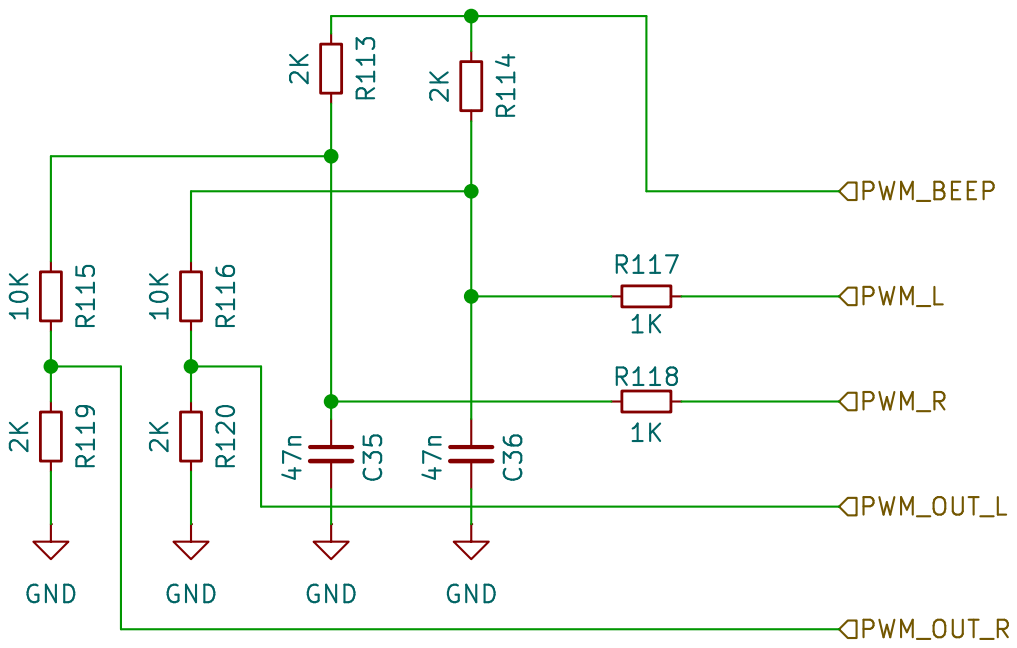
[picture p174: page 21]

https://github.com/xtremespb/frank R117

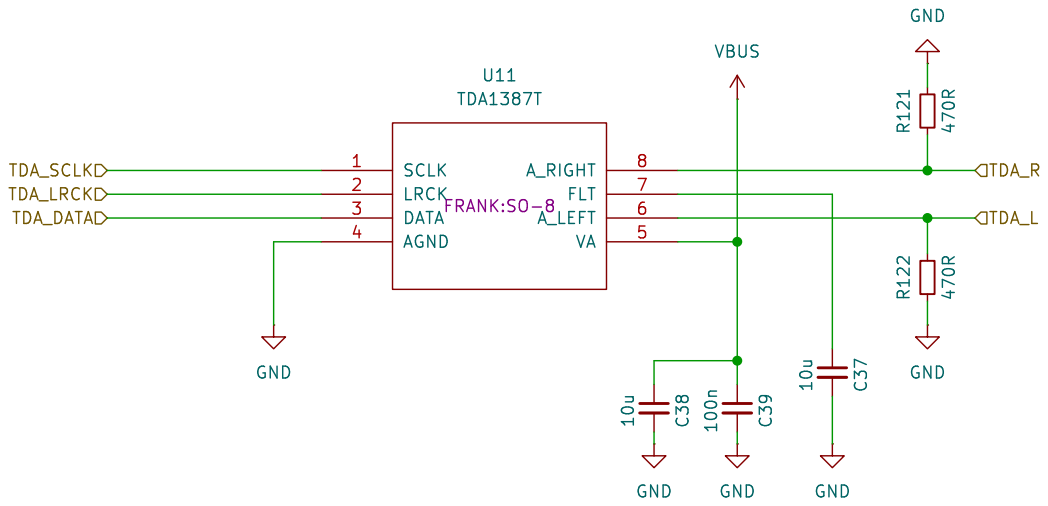
[picture p175: page 22]
