ponikrf/frank/hardware/turbofrank/DOCS/1_06/assembly.pdf

1 | 2 | 3 | 4 | 5 | 6

A

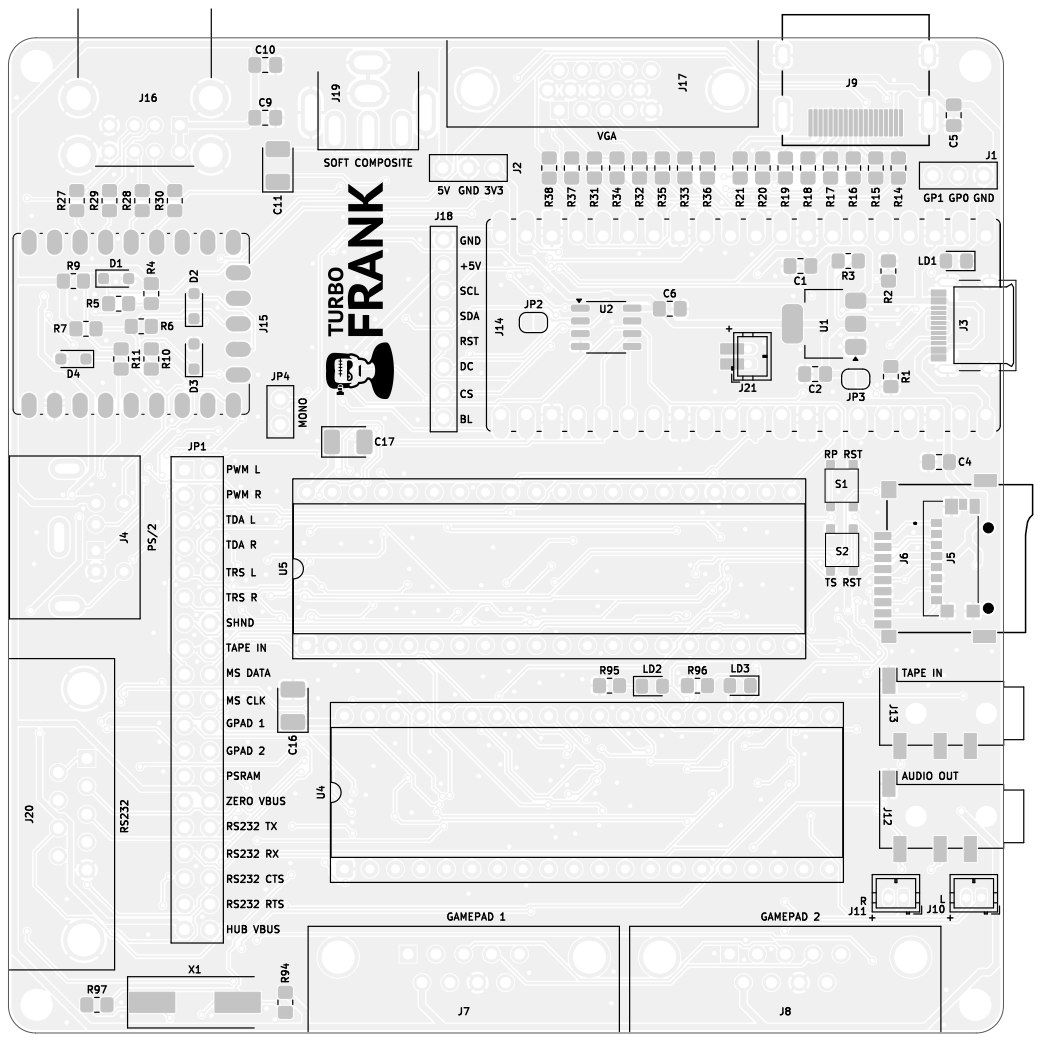
[picture p176: page 1]

https://github.com/xtremespb/frank Black And White TOP - Page 1/4

File: turbofrank.kicad_pcb Sheet: Black And White TOP Mikhail Matveev

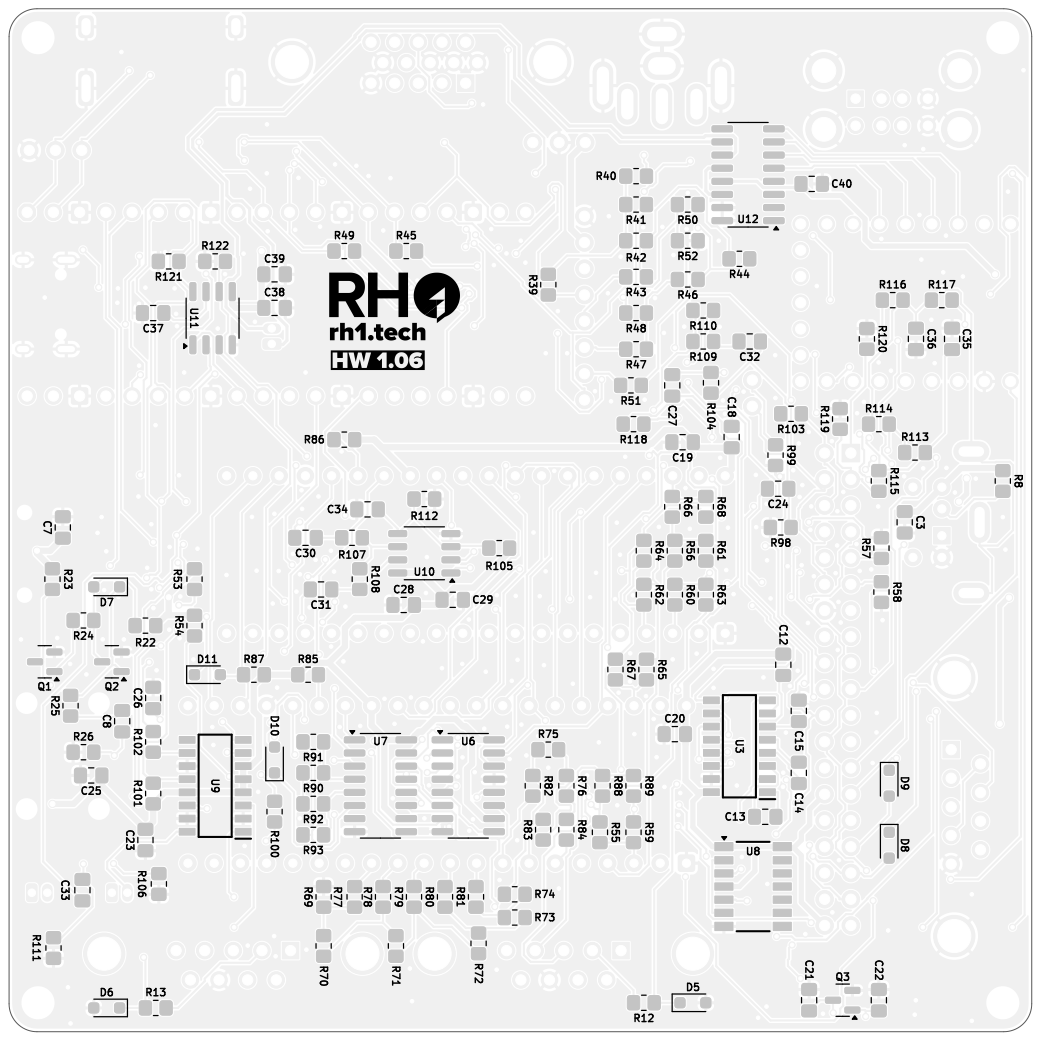
[picture p177: page 2]

https://github.com/xtremespb/frank Black And White BOT - Page 2/4

File: turbofrank.kicad_pcb Sheet: Black And White BOT Mikhail Matveev

1 | 2 | 3 | 4 | 5 | 6

A

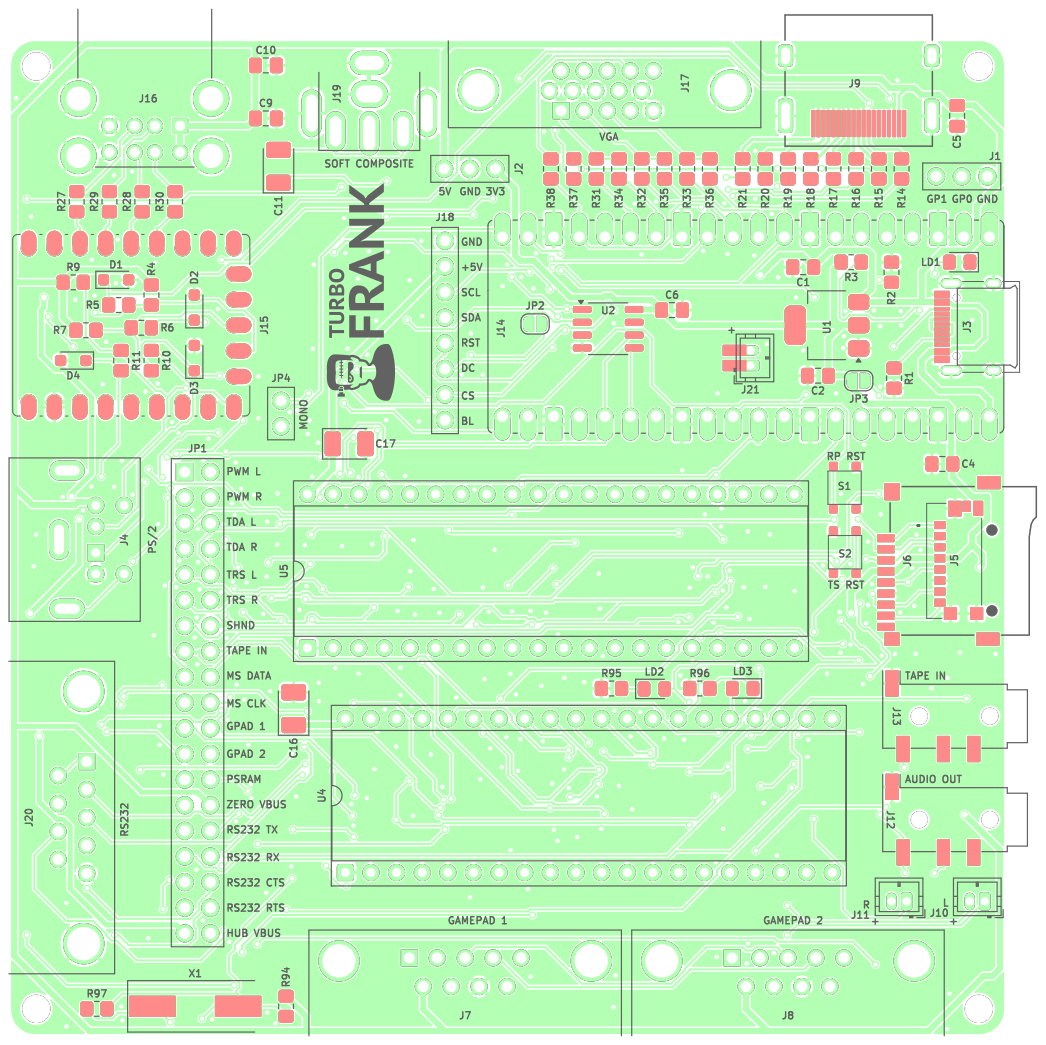
[picture p178: page 3]

LM358 U10 TDA1387T U11 | MW7211A U12 10K
R40 | 300R

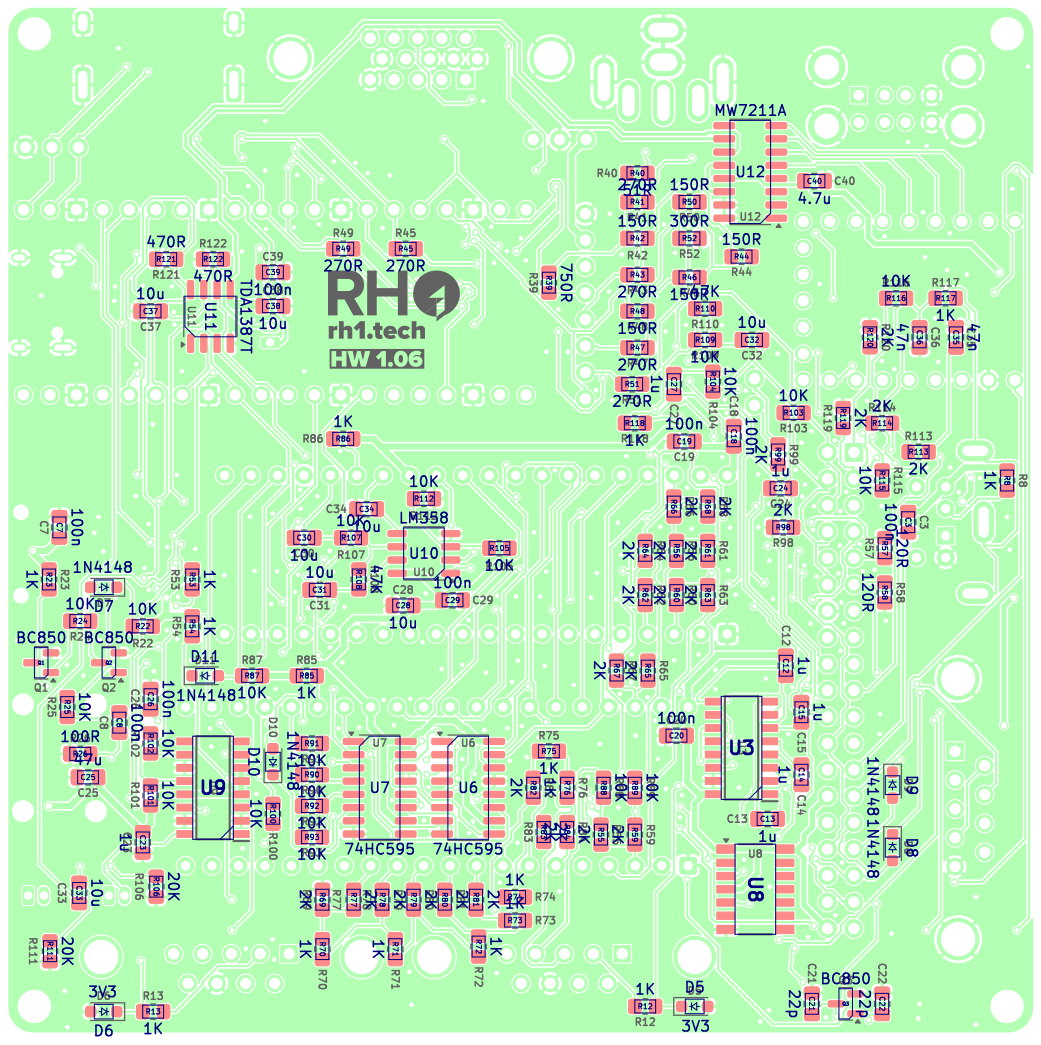
[picture p179: page 4]

https://github.com/xtremespb/frank Colored BOT - Page 4/4 ¹uC23

File: turbofrank.kicad_pcb Sheet: Colored BOT Mikhail Matveev
