ponikrf/frank/hardware/turbofrank/DOCS/1_06/turbofrank.pdf

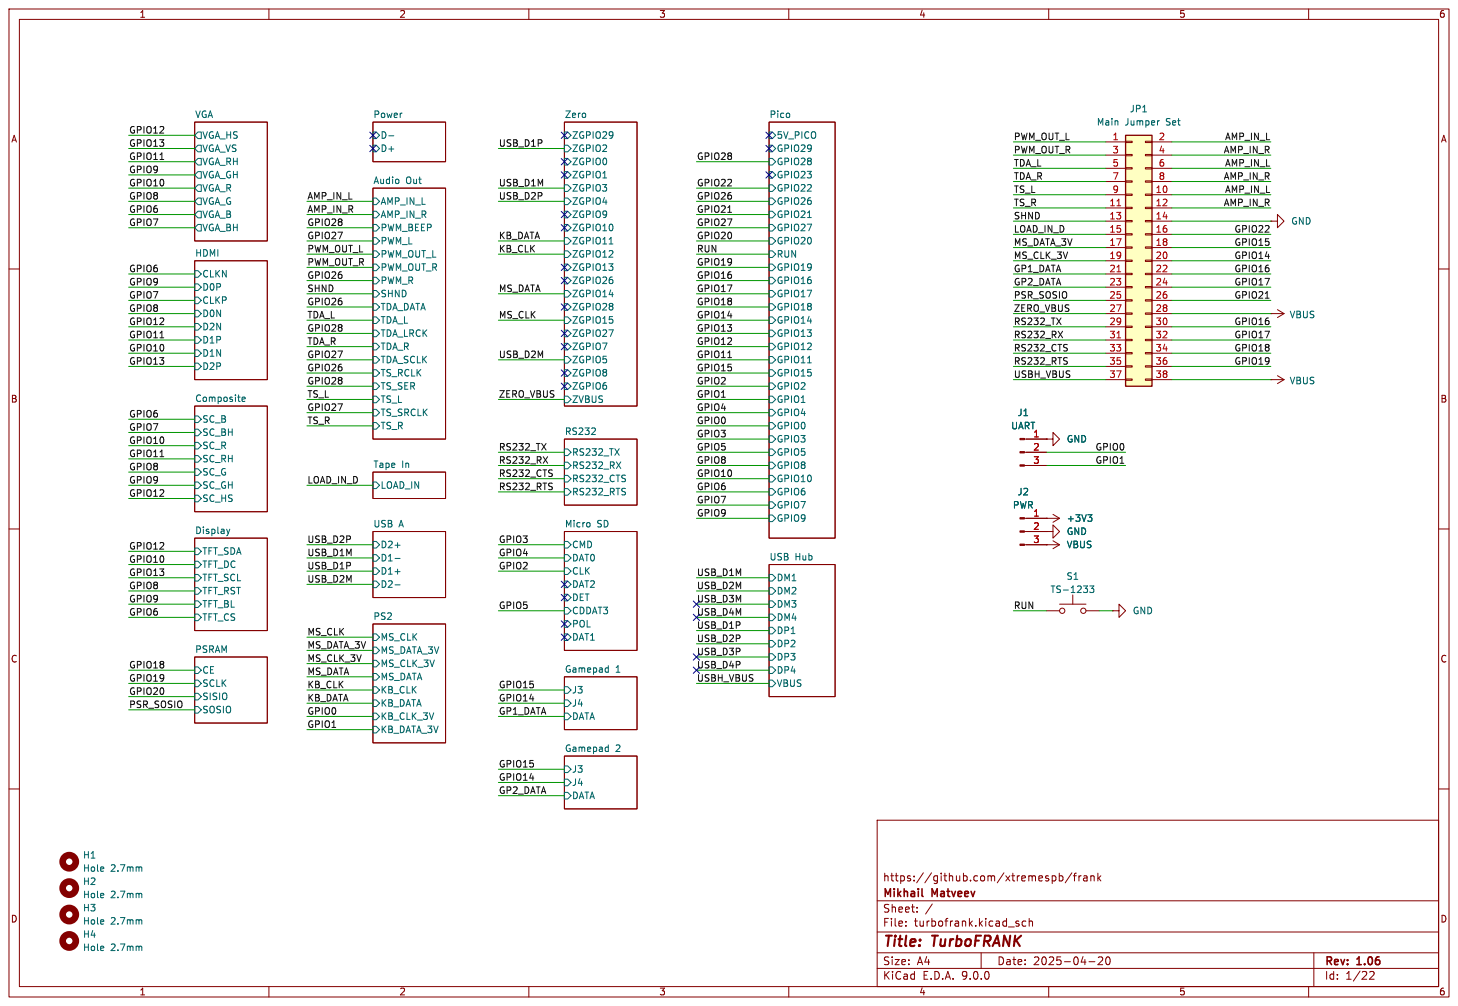
[picture p180: page 1]

DAT0 CLK DAT2 DET CDDAT3 POL DAT1 Micro SD


https://github.com/xtremespb/frank


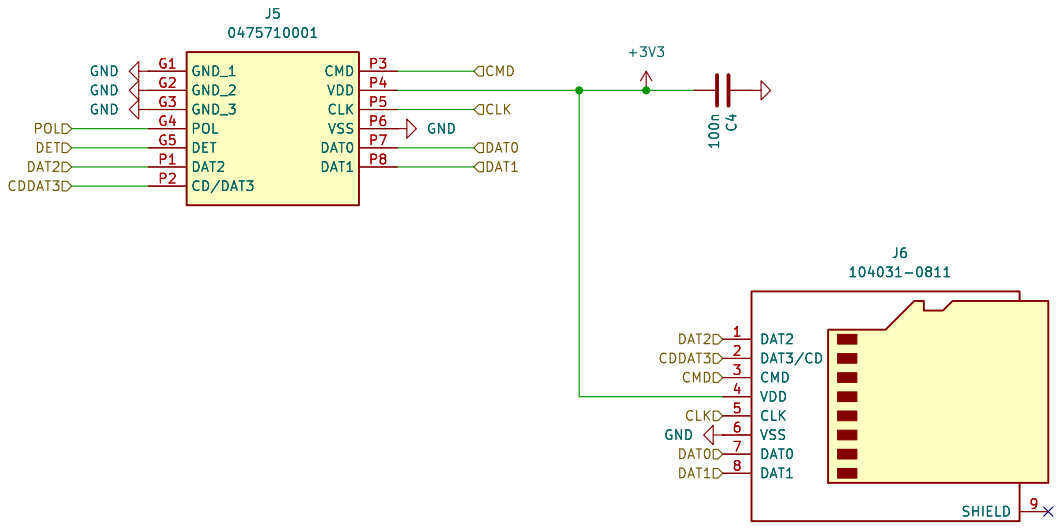
[picture p181: page 4]


https://github.com/xtremespb/frank GND


https://github.com/xtremespb/frank GND


https://github.com/xtremespb/frank GND


4 ~{CE}1 SCLK 6 SIO3 7 SIO2 3 SI/SIO 5 SO/SIO 2 U2 ESP-PSRAM32 C6

4 ~{CE}1 SCLK 6 SIO3 7 SIO2 3 SI/SIO 5 SO/SIO 2 GND

https://github.com/xtremespb/frank

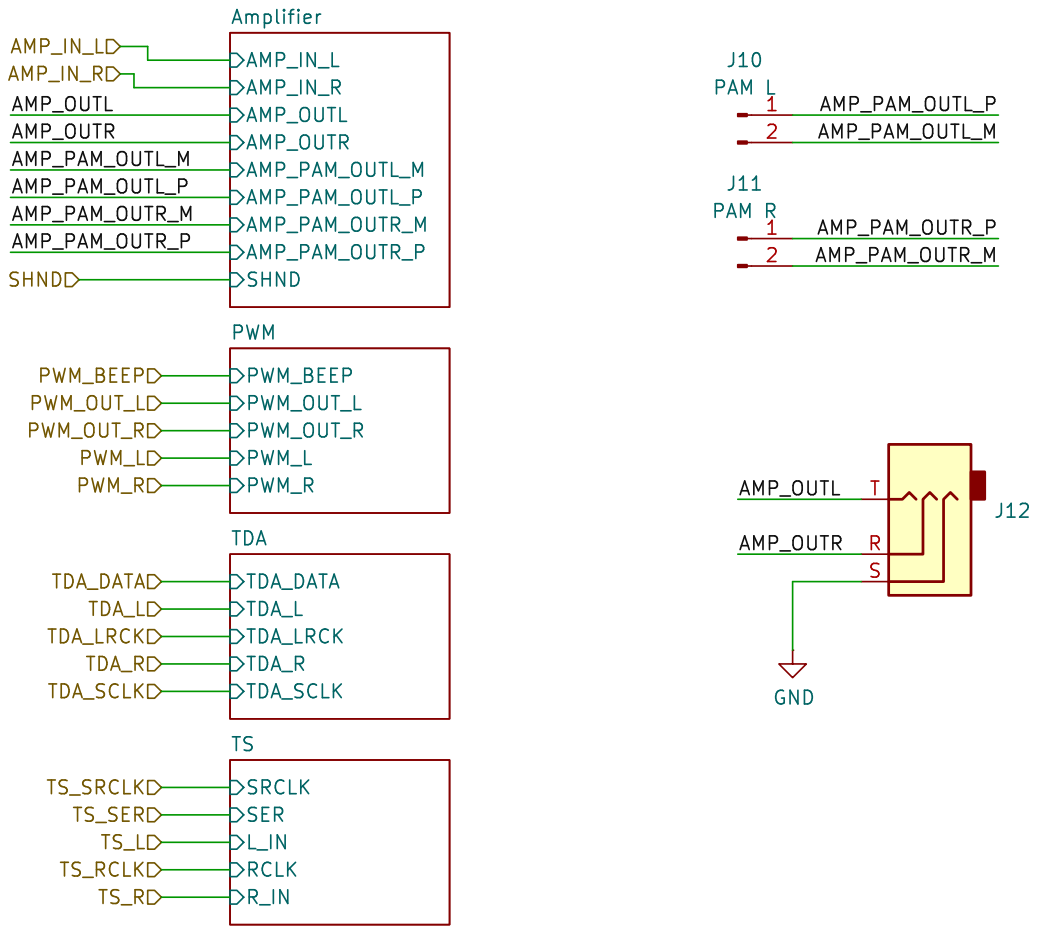
[picture p182: page 9]

https://github.com/xtremespb/frank


https://github.com/xtremespb/frank GND

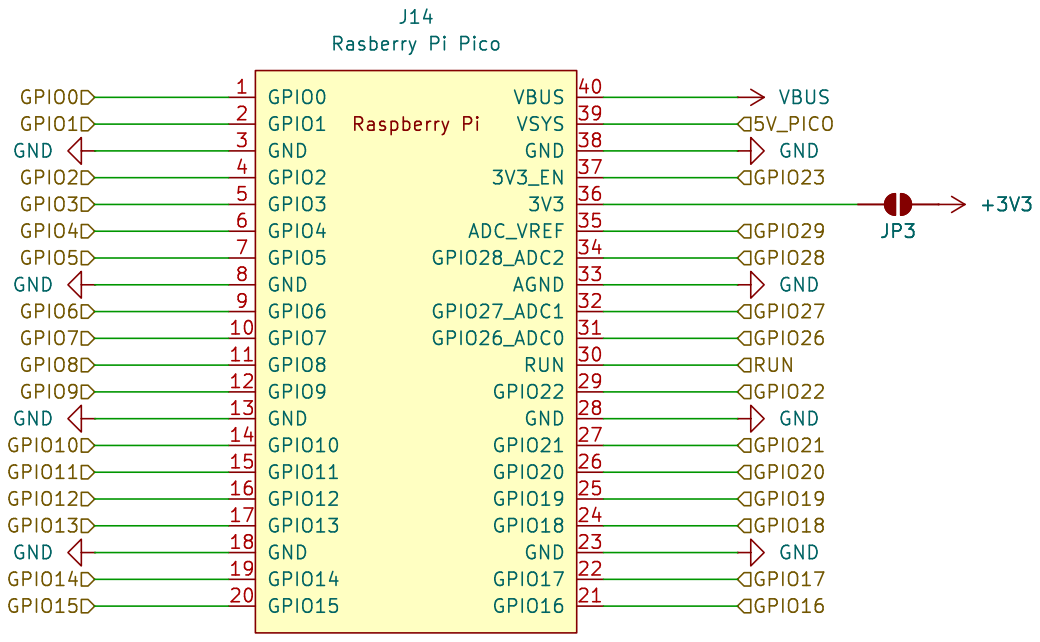
[picture p183: page 11]


https://github.com/xtremespb/frank


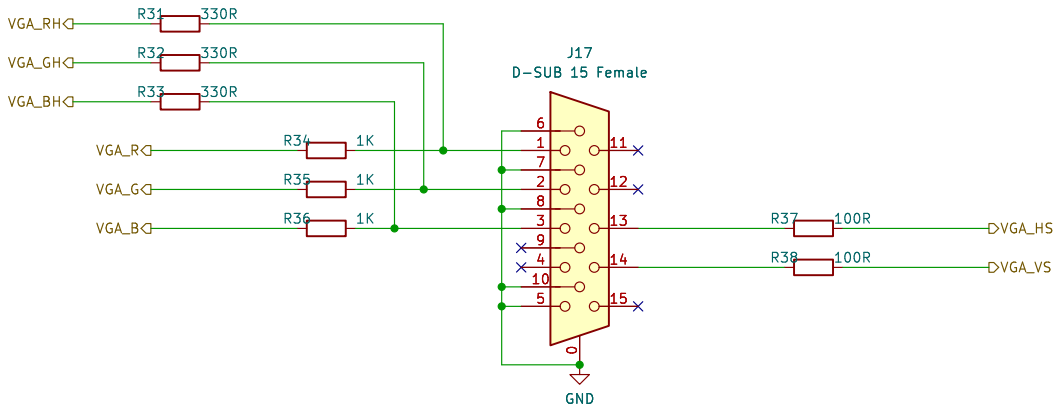
[picture p184: page 14]


https://github.com/xtremespb/frank


https://github.com/xtremespb/frank R46

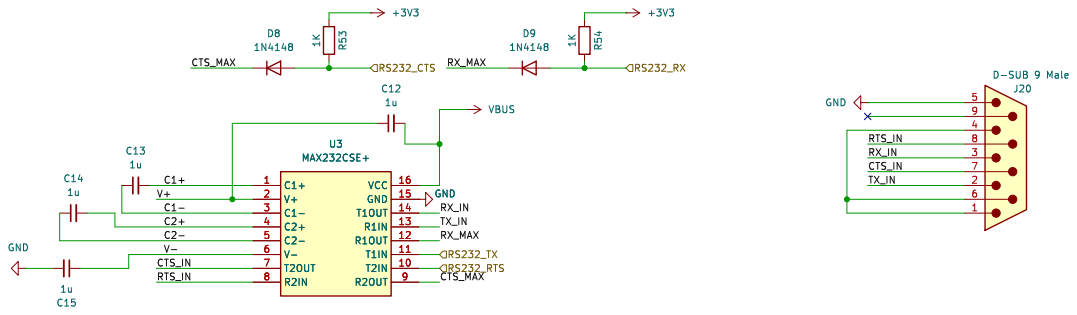
[picture p185: page 17]

https://github.com/xtremespb/frank C13

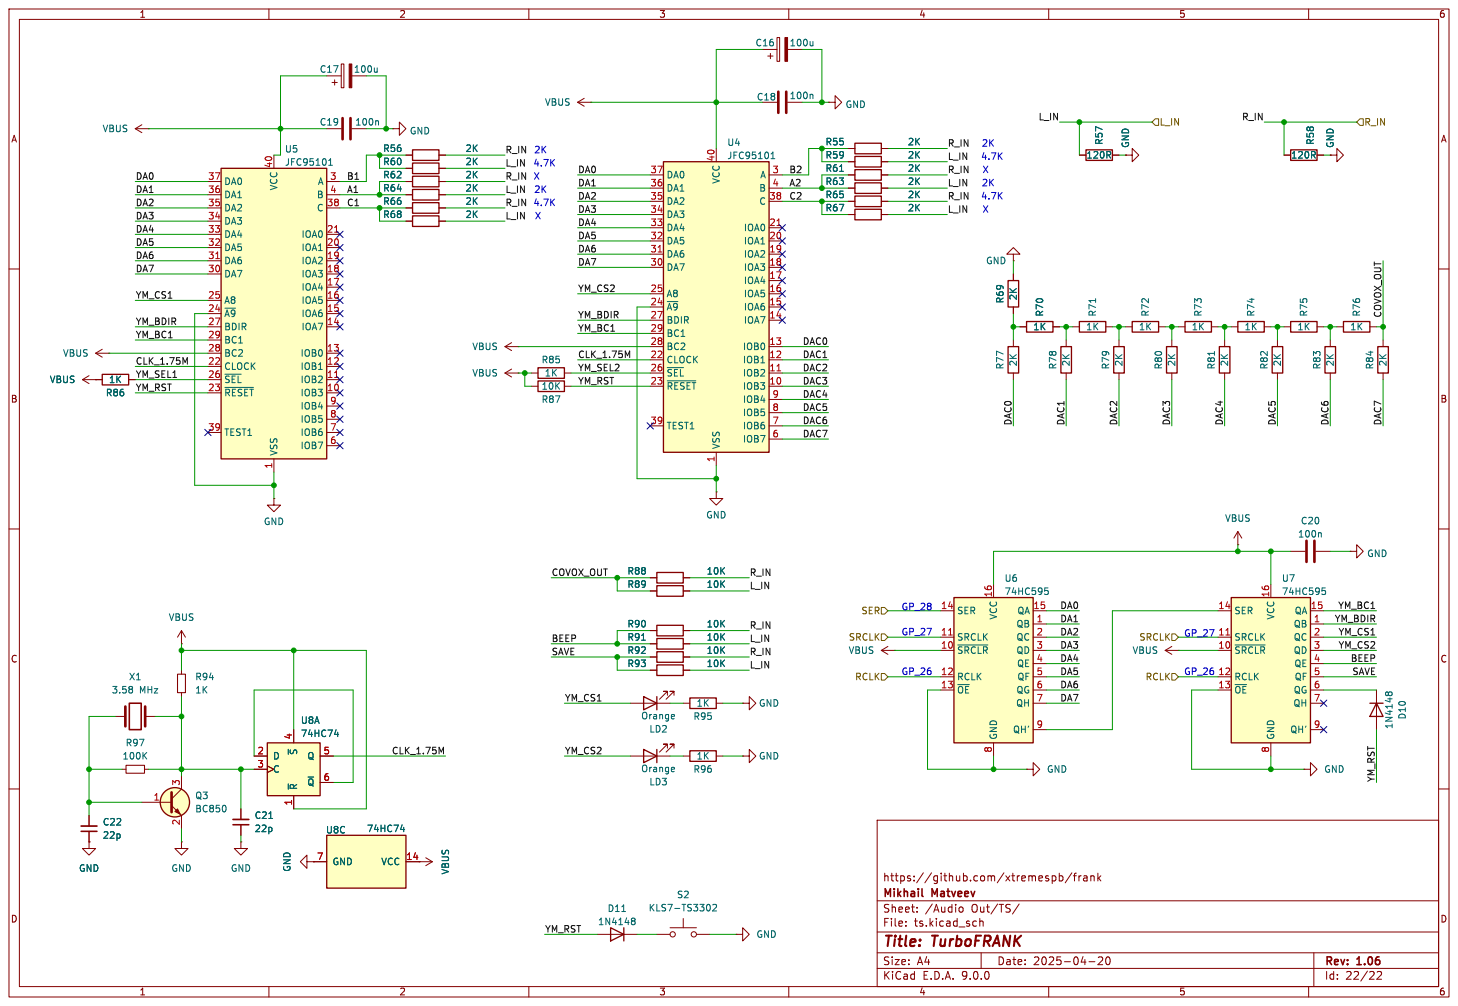
[picture p186: page 18]

https://github.com/xtremespb/frank

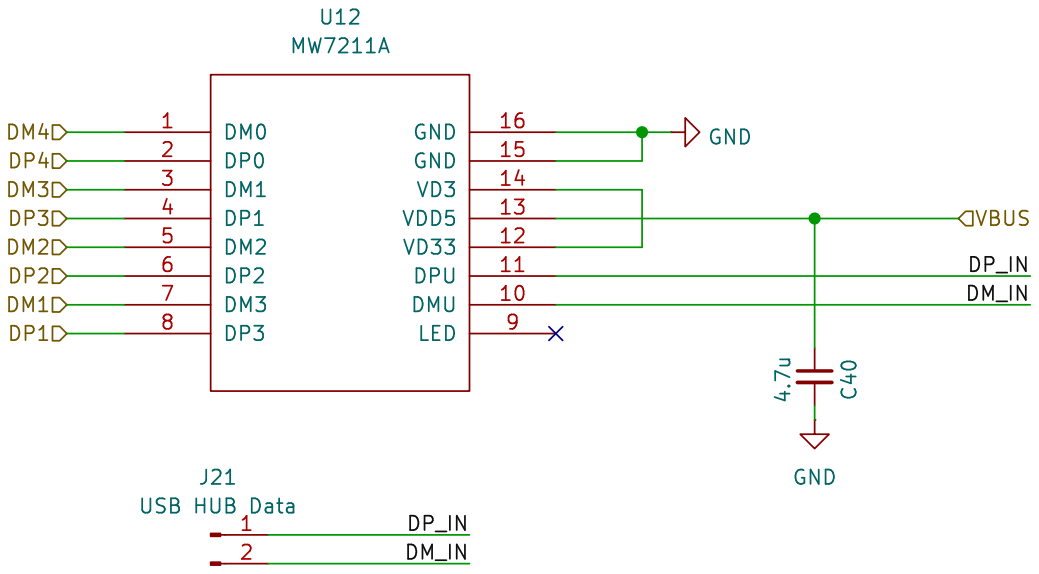
[picture p187: page 19]

https://github.com/xtremespb/frank

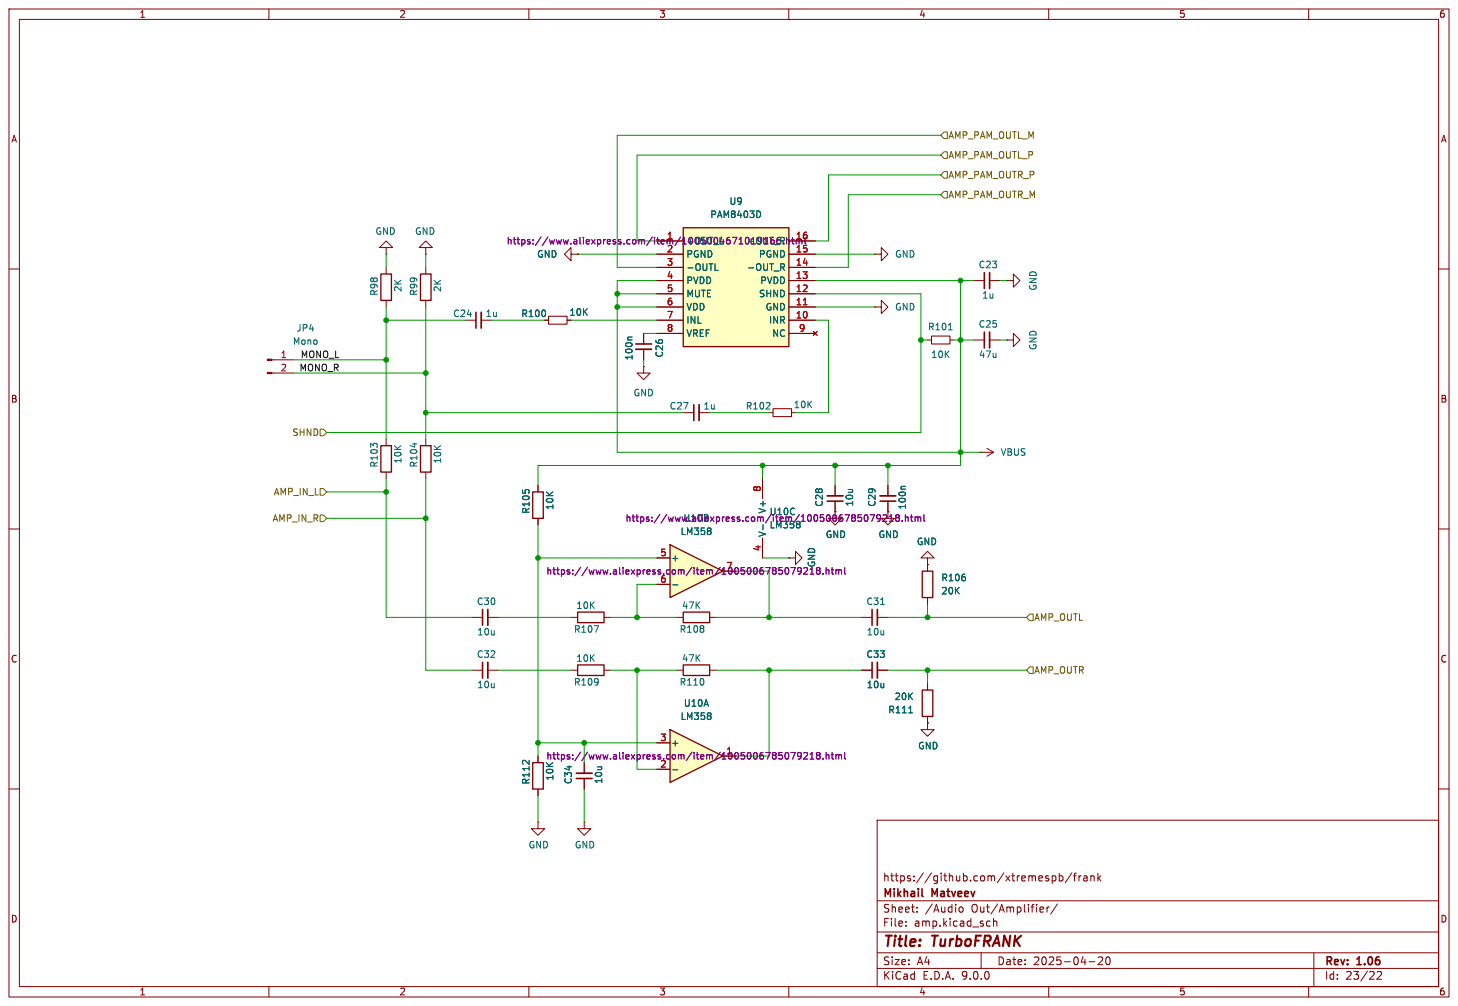
[picture p188: page 20]

LM358 https://www.aliexpress.com/item/1005006785079218.html V+

https://www.aliexpress.com/item/1005006785079218.html +

https://github.com/xtremespb/frank


https://github.com/xtremespb/frank R117
