ponikrf/frank/hardware/turbofrank/DOCS/1_07/turbofrank.pdf

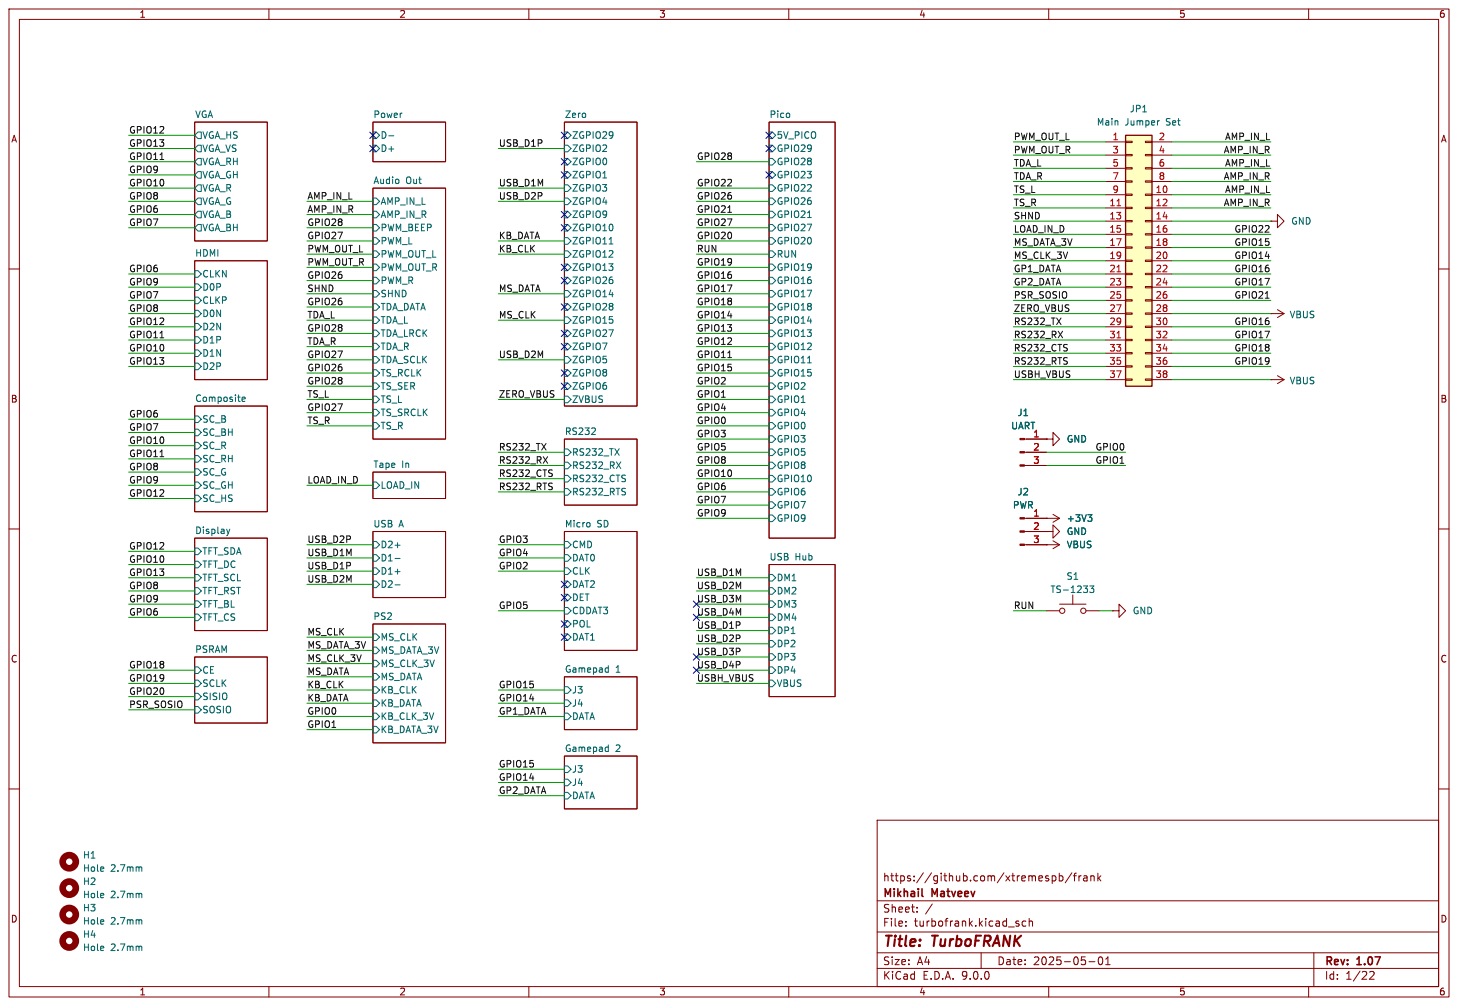
[picture p189: page 1]

DAT0 CLK DAT2 DET CDDAT3 POL DAT1 Micro SD

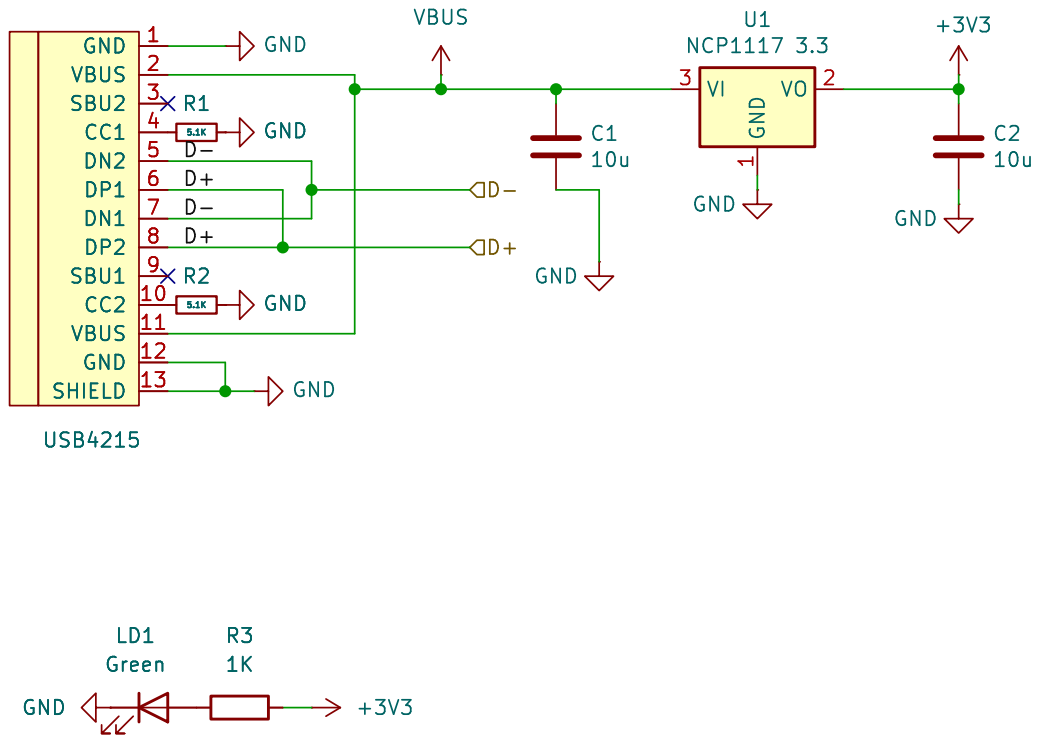
[picture p190: page 2]

https://github.com/xtremespb/frank



https://github.com/xtremespb/frank GND


https://github.com/xtremespb/frank GND


https://github.com/xtremespb/frank GND


https://github.com/xtremespb/frank GND


4 ~{CE}1 SCLK 6 SIO3 7 SIO2 3 SI/SIO 5 SO/SIO 2 +3V3

4 ~{CE}1 SCLK 6 SIO3 7 SIO2 3 SI/SIO 5 SO/SIO 2 U2 ESP-PSRAM32 GND

https://github.com/xtremespb/frank


https://github.com/xtremespb/frank


https://github.com/xtremespb/frank GND



https://github.com/xtremespb/frank




https://github.com/xtremespb/frank


https://github.com/xtremespb/frank R46


https://github.com/xtremespb/frank C13

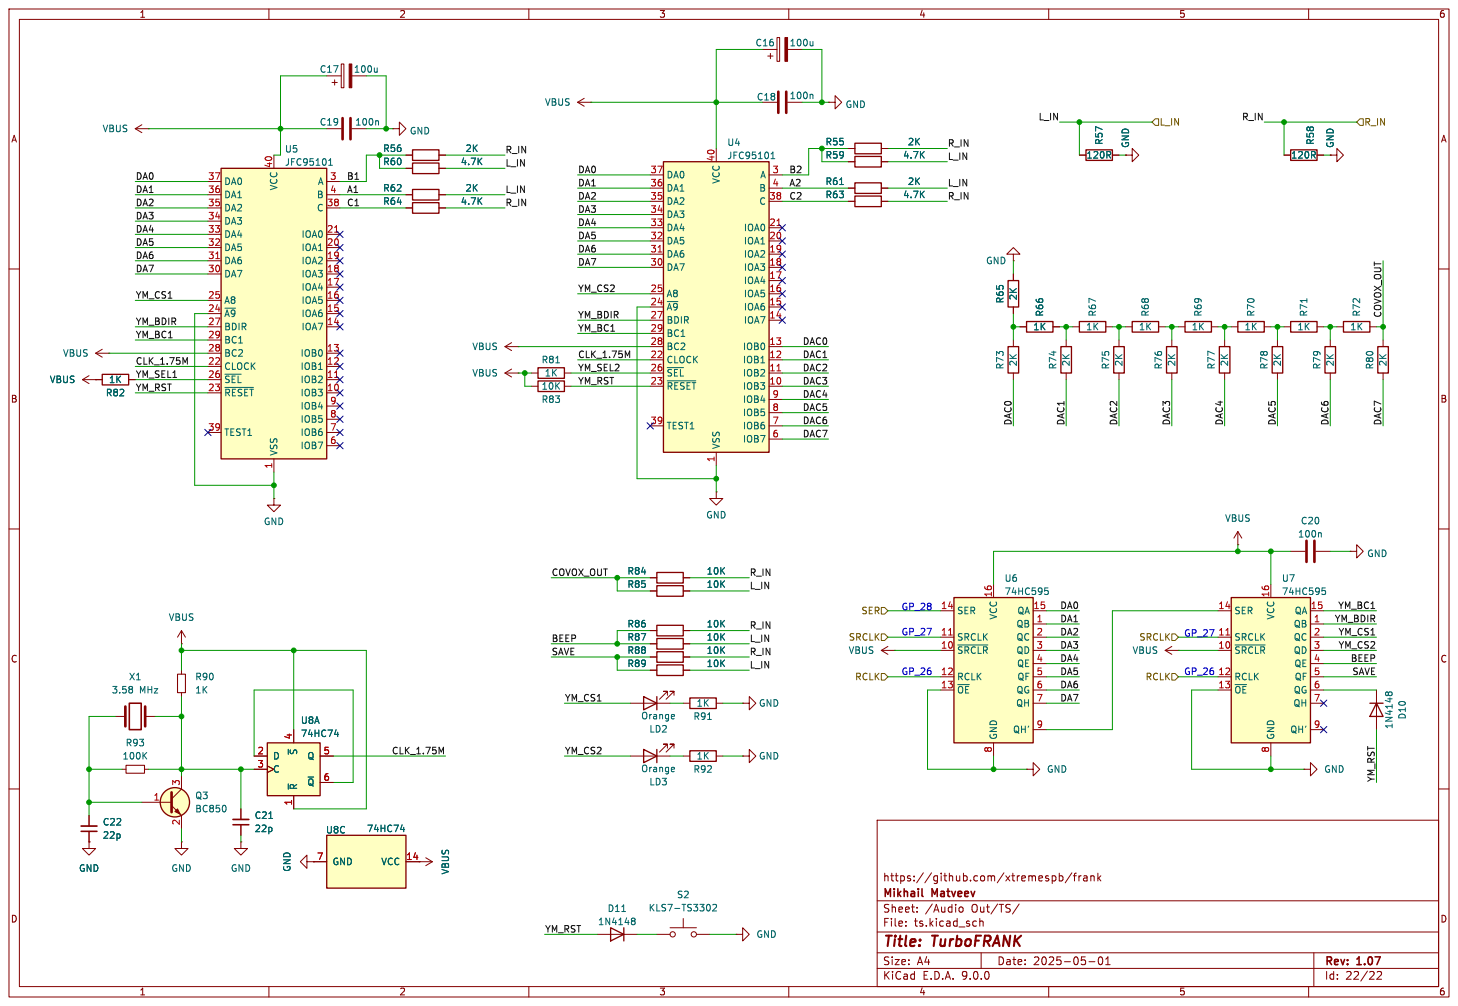
[picture p191: page 18]

https://github.com/xtremespb/frank

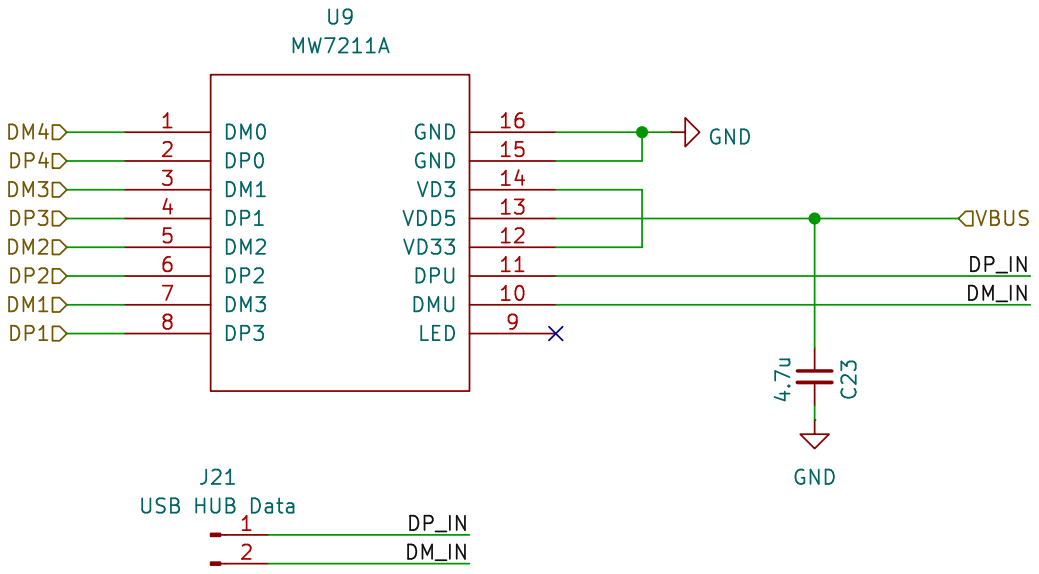
[picture p192: page 19]

https://github.com/xtremespb/frank

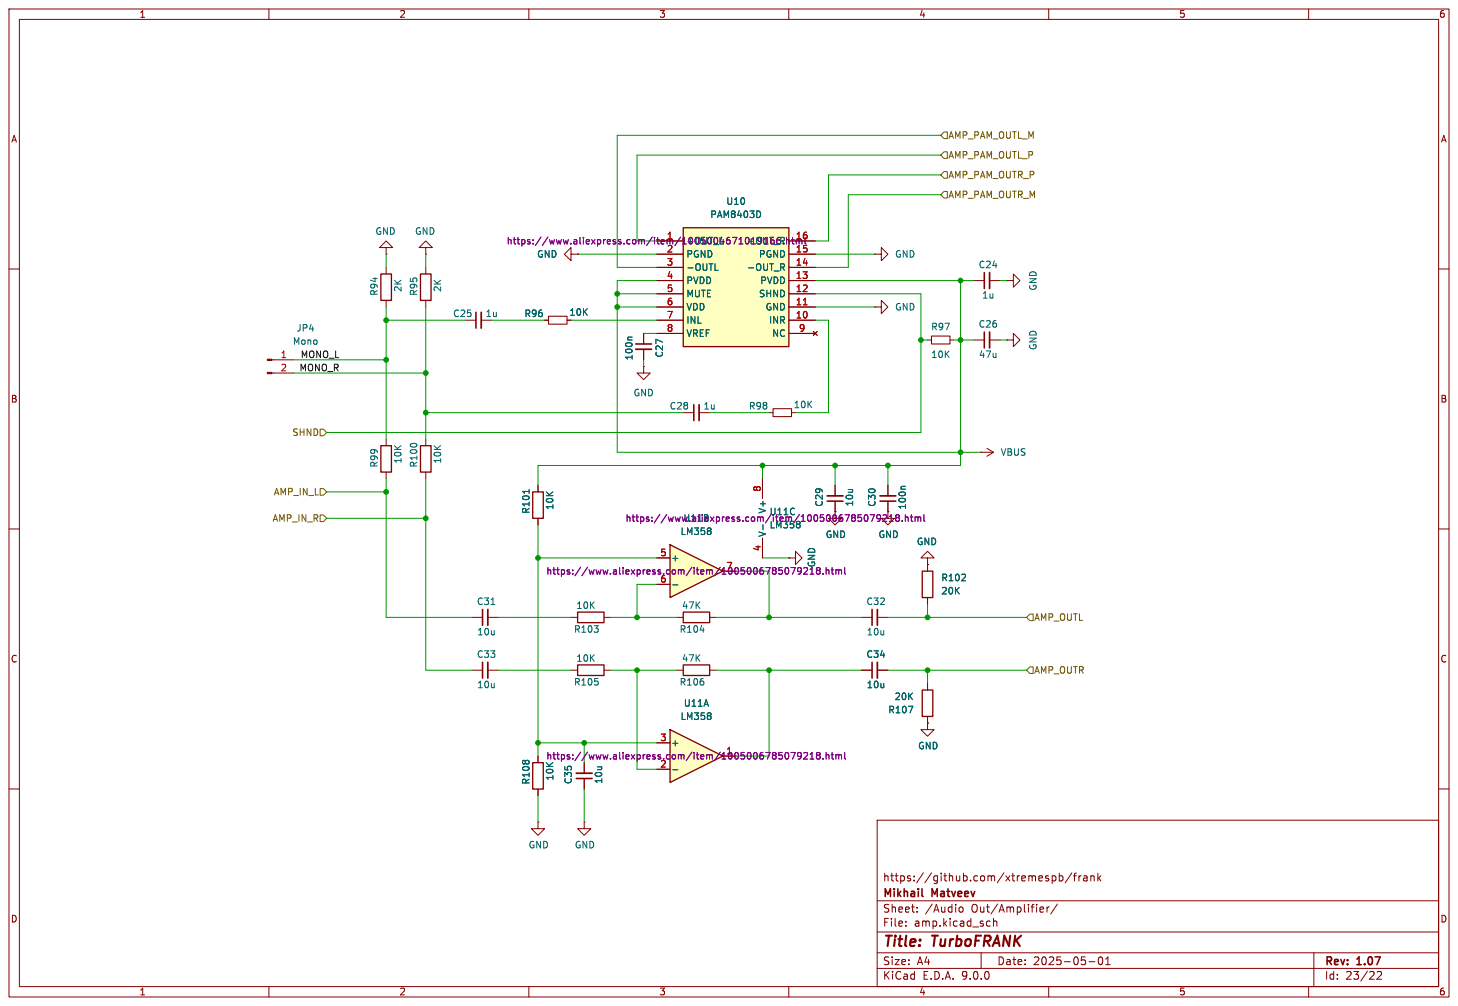
[picture p193: page 20]

https://www.aliexpress.com/item/1005004671019166.html GND

LM358 https://www.aliexpress.com/item/1005006785079218.html V+

https://www.aliexpress.com/item/1005006785079218.html +

https://www.aliexpress.com/item/1005006785079218.html

https://github.com/xtremespb/frank

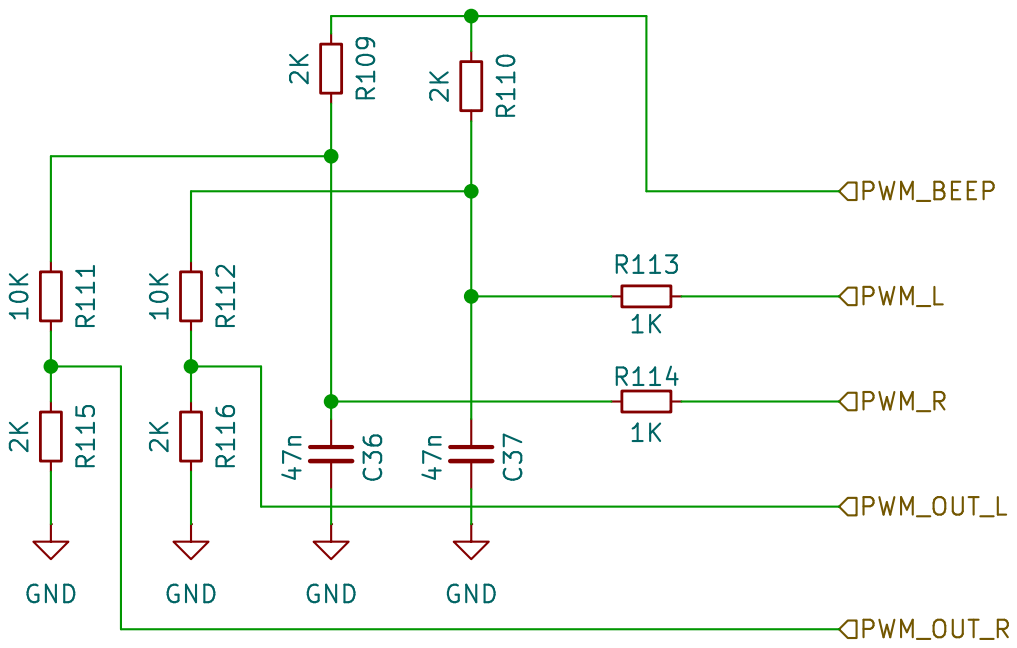
[picture p194: page 21]

https://github.com/xtremespb/frank R113

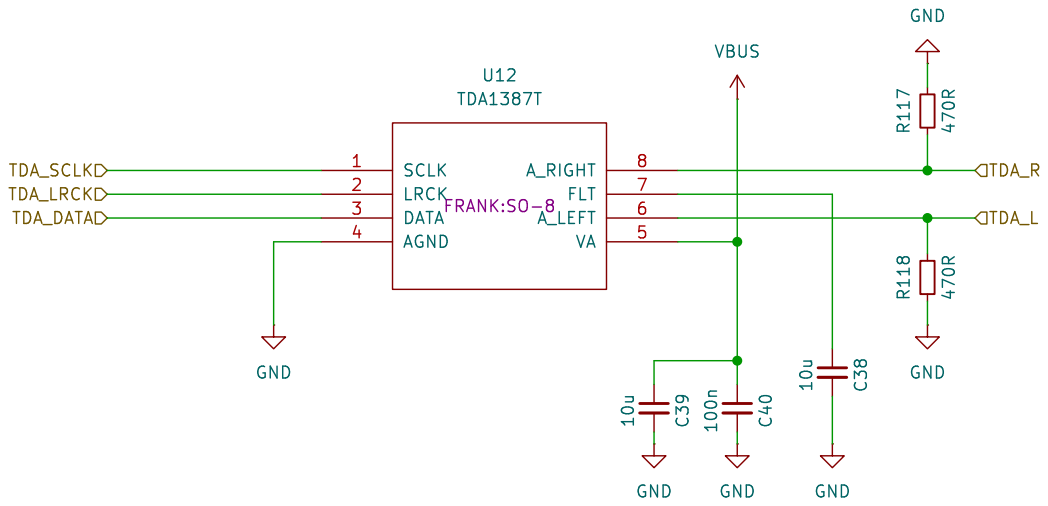
[picture p195: page 22]
