ponikrf/frank/hardware/turbofrank/DOCS/1_07/turbofrank__Assembly.pdf

# J10 R²⁰

1 | 2 | 3 | 4 | 5 | 6

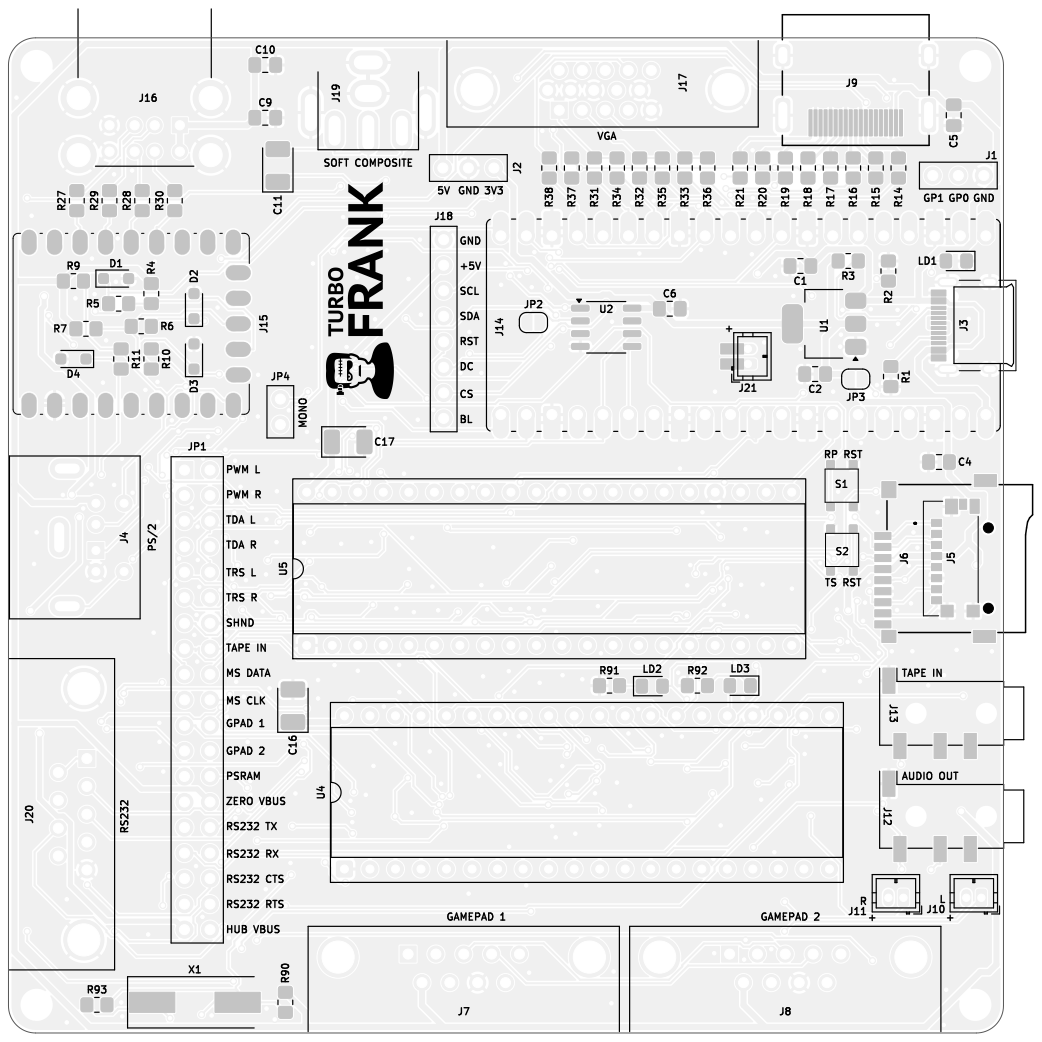
[picture p196: page 1]

https://github.com/xtremespb/frank Black And White TOP - Page 1/4

File: turbofrank.kicad_pcb Sheet: Black And White TOP Mikhail Matveev

R112 R75 R22 C27 | R100 C31R82 | U11 | R42 R39 C35R103 1 | 2 | 3 | 4 | 5 | 6 1 | 2 | 3 | 4 | 5 | 6 ABCD | ABCD Date: 2025-05-01 KiCad E.D.A. 9.0.0 Size: A4 | Rev: 1.07

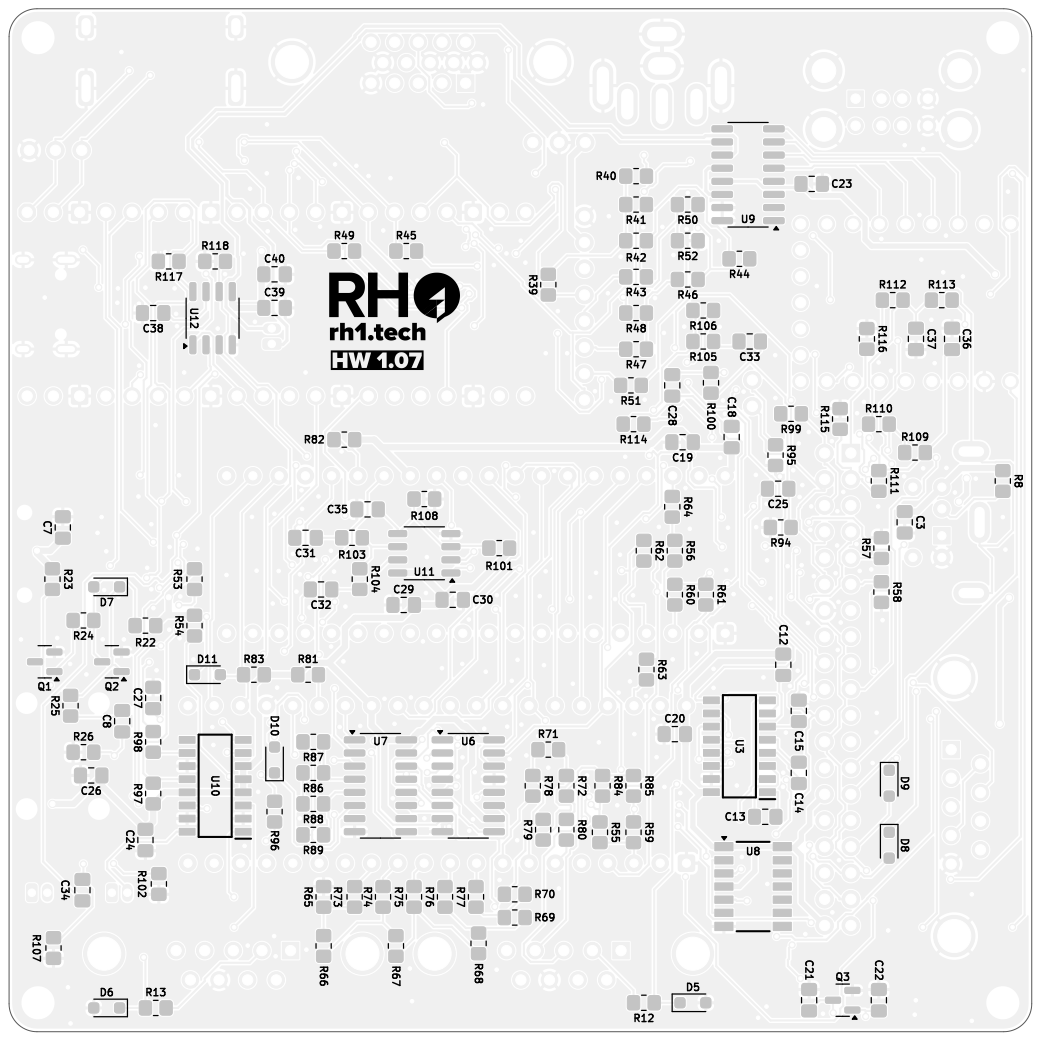
[picture p197: page 2]

https://github.com/xtremespb/frank Black And White BOT - Page 2/4

File: turbofrank.kicad_pcb Sheet: Black And White BOT Mikhail Matveev

1 | 2 | 3 | 4 | 5 | 6

A

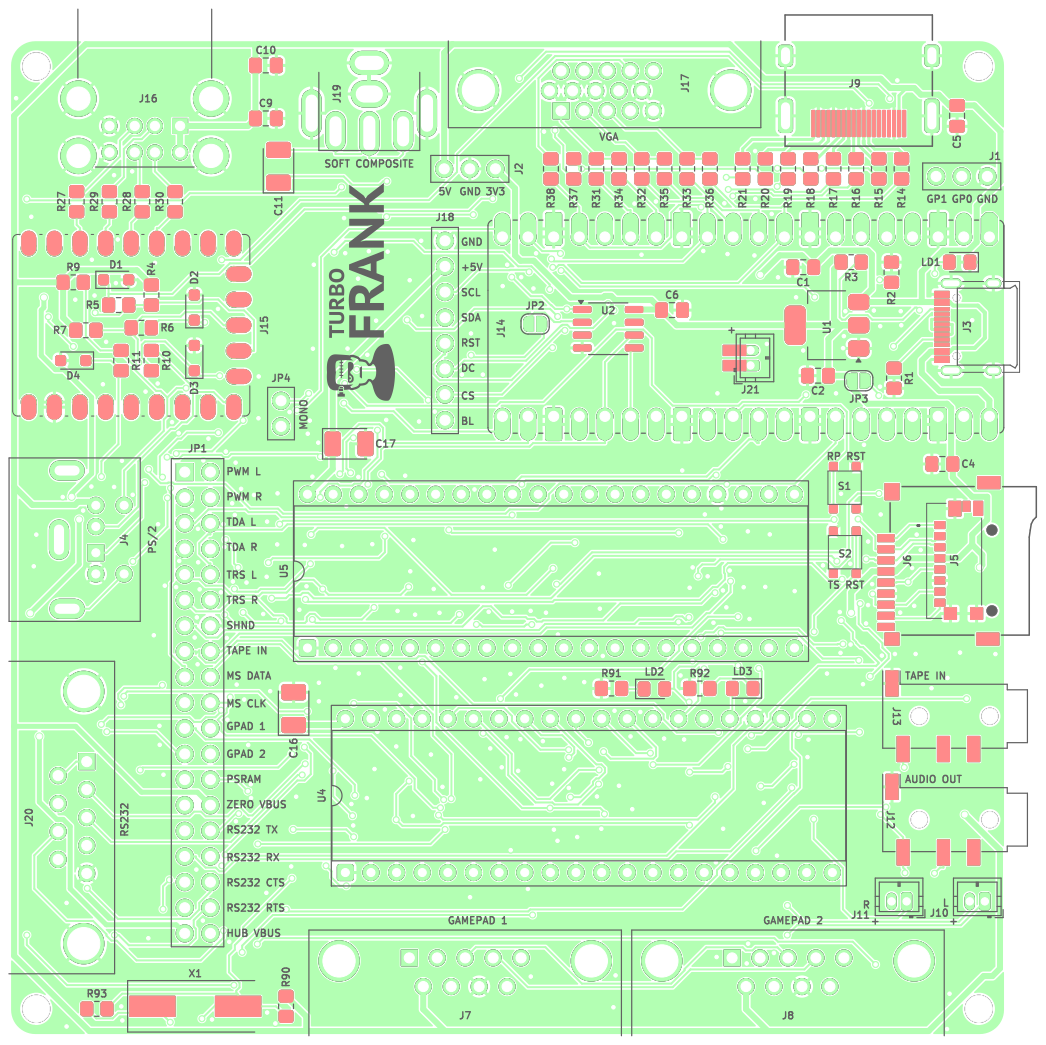
[picture p198: page 3]

R112 R75 R22 C27 | R100 C31R82 | U11 | R42 R39 C35R103 1 | 2 | 3 | 4 | 5 | 6 1 | 2 | 3 | 4 | 5 | 6 ABCD | ABCD Date: 2025-05-01 KiCad E.D.A. 9.0.0 Size: A4 | Rev: 1.07
R40 | 300R

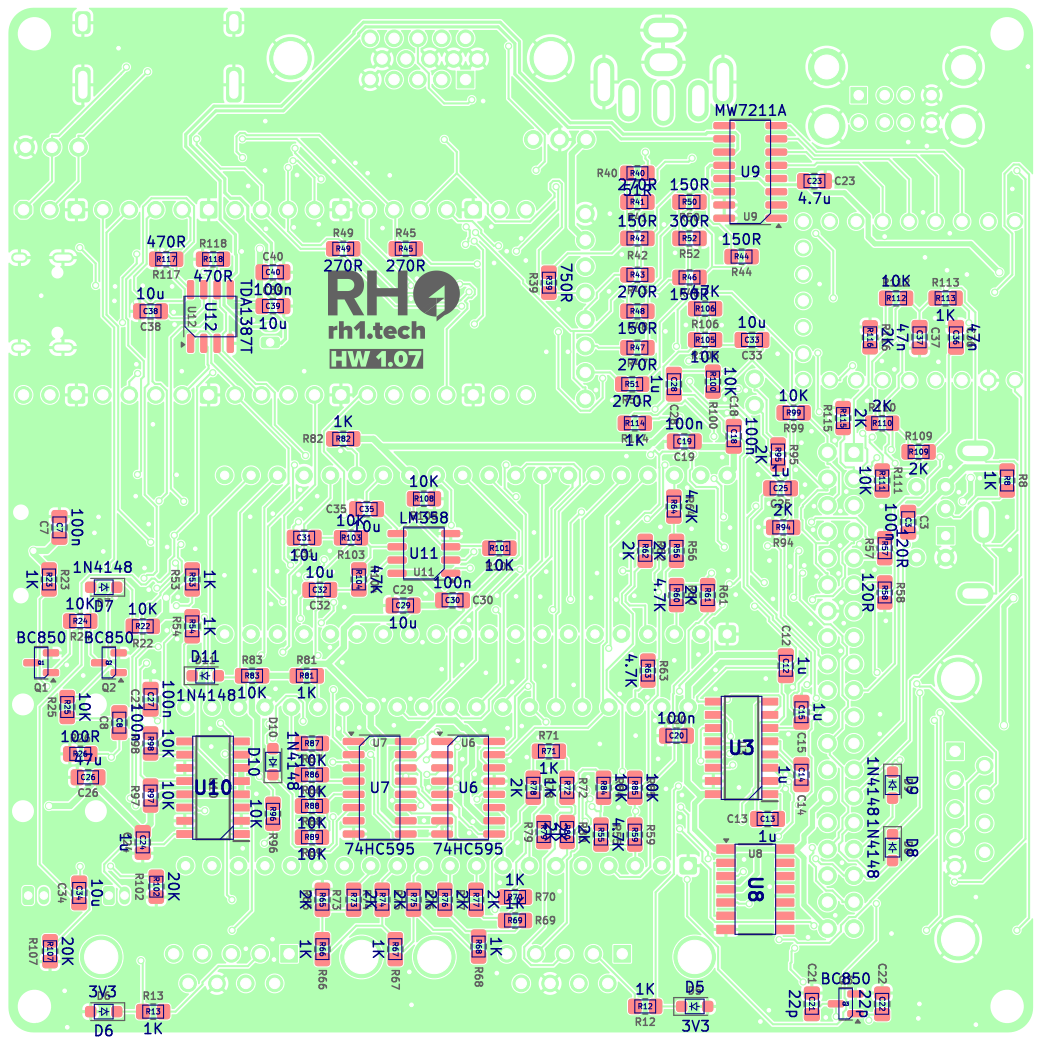
[picture p199: page 4]

https://github.com/xtremespb/frank Colored BOT - Page 4/4

File: turbofrank.kicad_pcb Sheet: Colored BOT Mikhail Matveev
