ponikrf/frank/hardware/usb2ps2/DOCS/1_03/assembly.pdf

# C2 3V3 D3

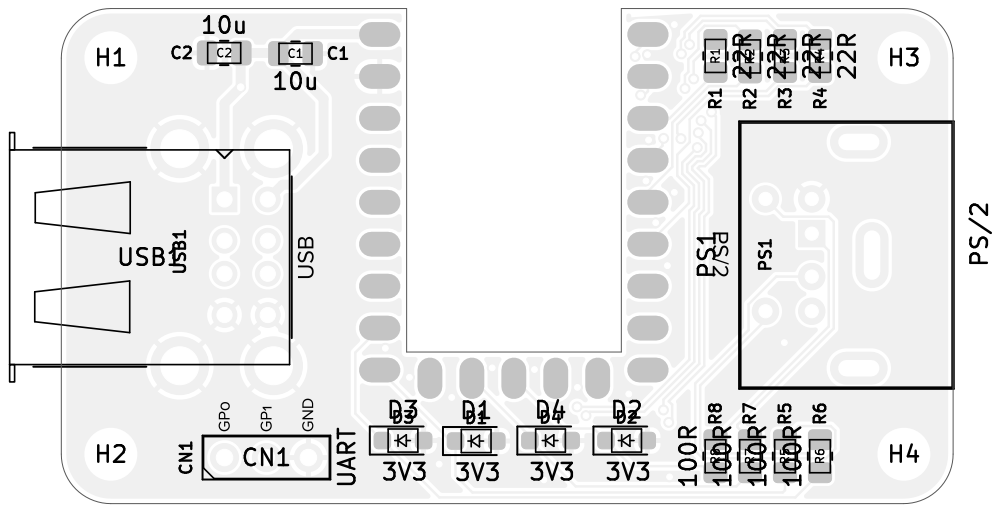
[picture p200: page 1]

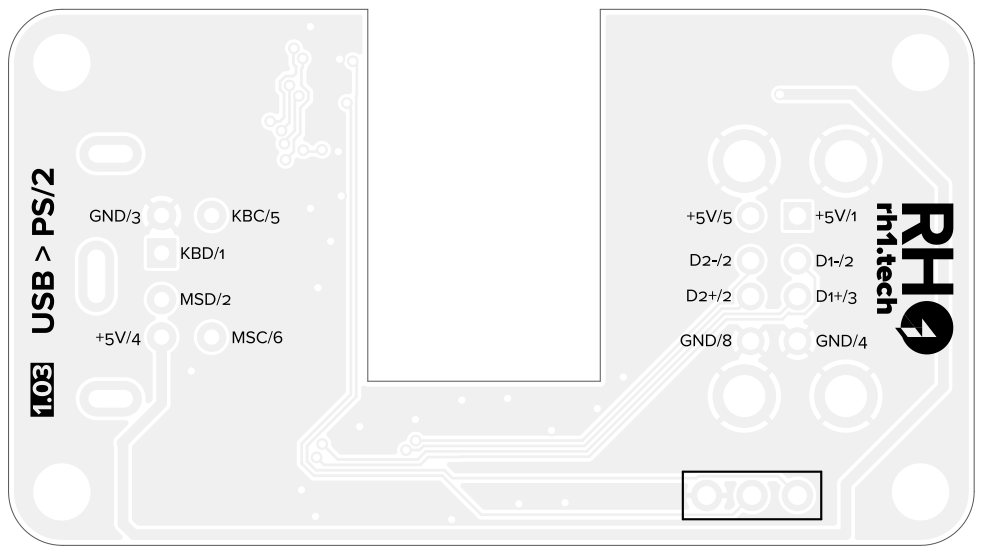
[picture p201: page 2]
D Date: 2025-03-09 KiCad; E.D.A. 9.0.0 Size: A4; Rev: 1.03; Id: /1 Title: USB to PS/2; Adapter File: usb2ps2.kicad_pcb Sheet: Black; And; White; BOT Mikhail; Matveev; https://github.com/xtremespb/frank Black; BOT -; Page 2/2
