ponikrf/frank/hardware/usb2ps2/DOCS/1_03/usb2ps2.pdf

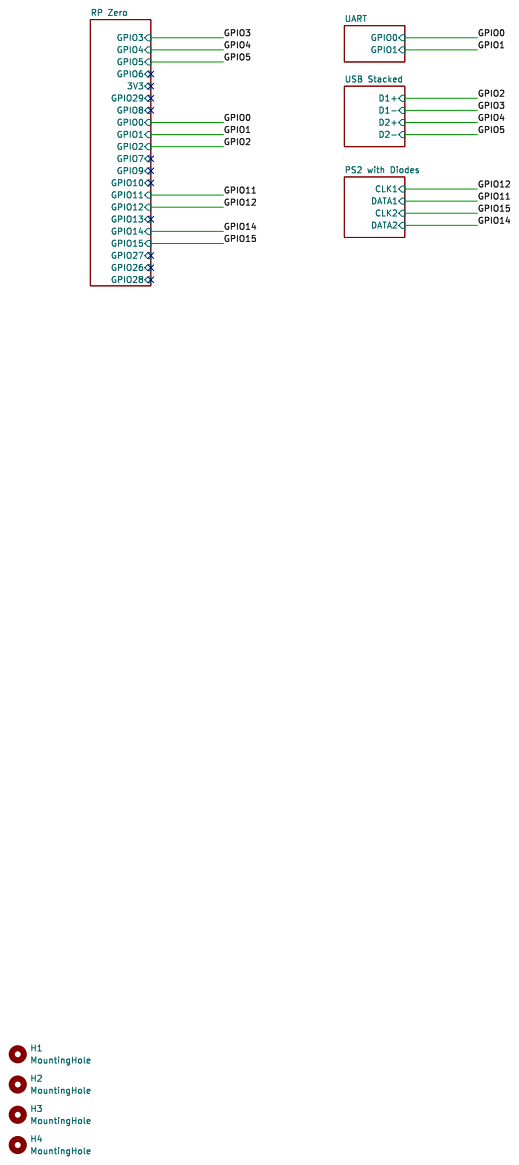
[picture p202: page 1]

H4 MountingHole H3 MountingHole H1 MountingHole H2 MountingHole

https://github.com/xtremespb/frank

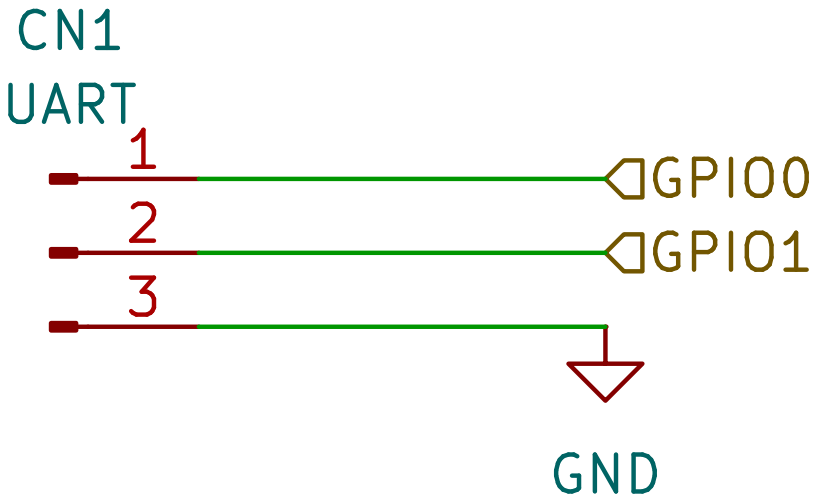
[picture p203: page 2]

https://github.com/xtremespb/frank

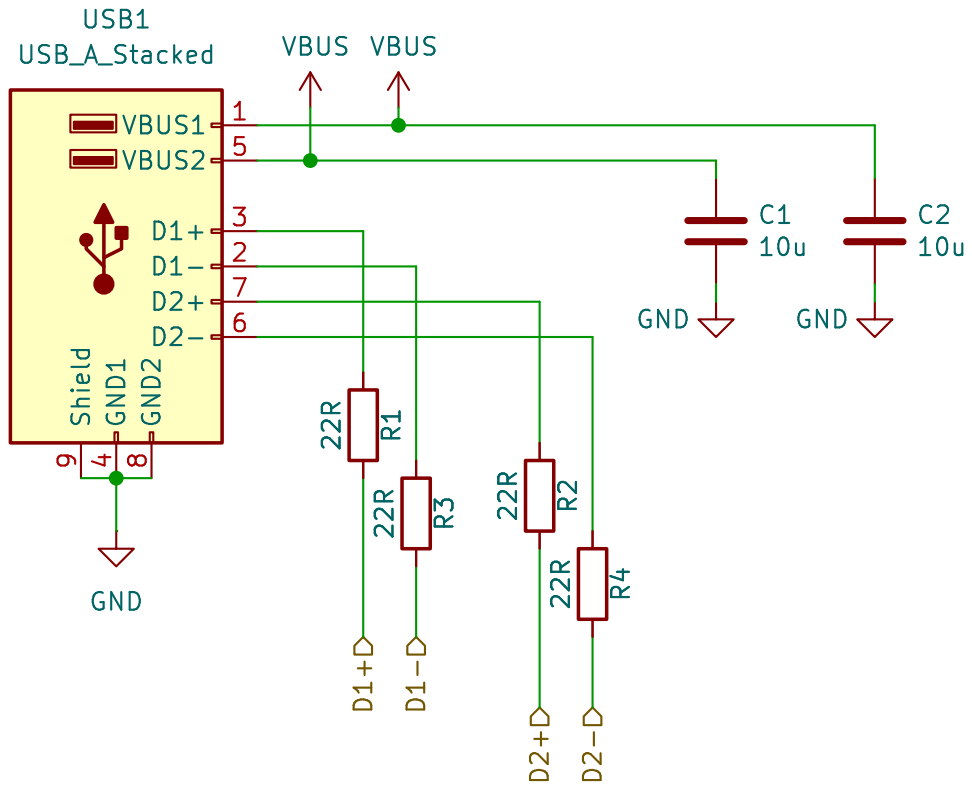
[picture p204: page 3]

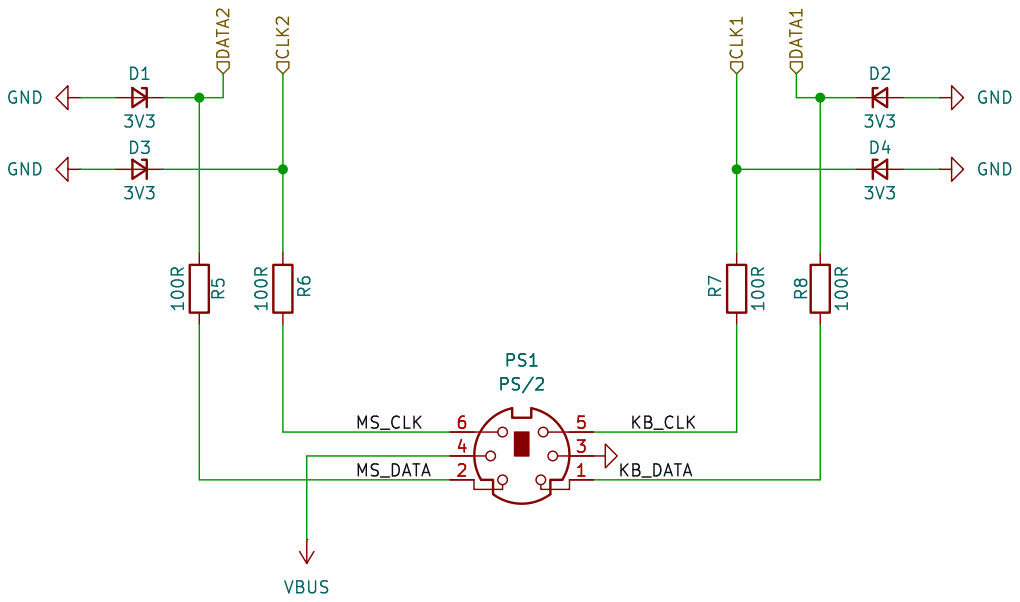
[picture p205: page 4]

https://github.com/xtremespb/frank

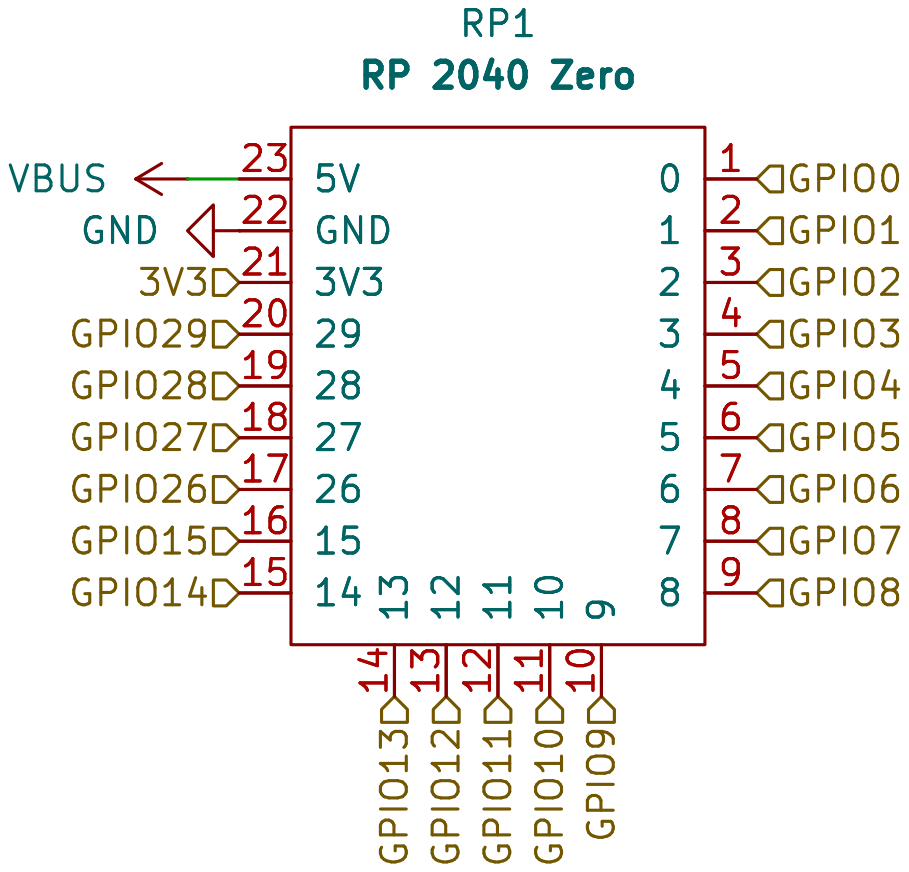
[picture p206: page 5]

https://github.com/xtremespb/frank
