ponikrf/frank/lab/nyx2/DOCS/1_03/assembly.pdf

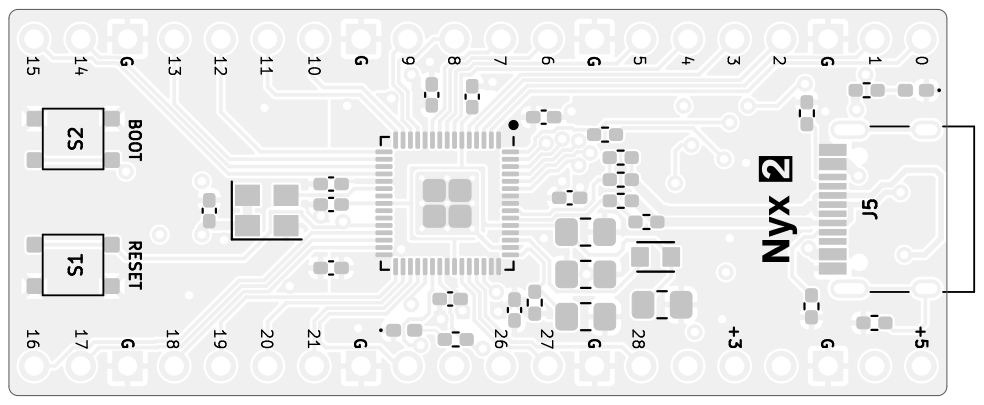
[picture p207: page 1]
BOOT RESET 28G2627G18192021G17 +3+5G 15131110G 9; D Date: 2025-05-07 KiCad; E.D.A. 9.0.0 Size: A4; Rev: 1.03; File: nyx2.kicad_pcb Sheet: Black; And; White; TOP Mikhail; Matveev; https://github.com/xtremespb/frank Black; TOP -; Page

Id: /1 Title: Nyx 2

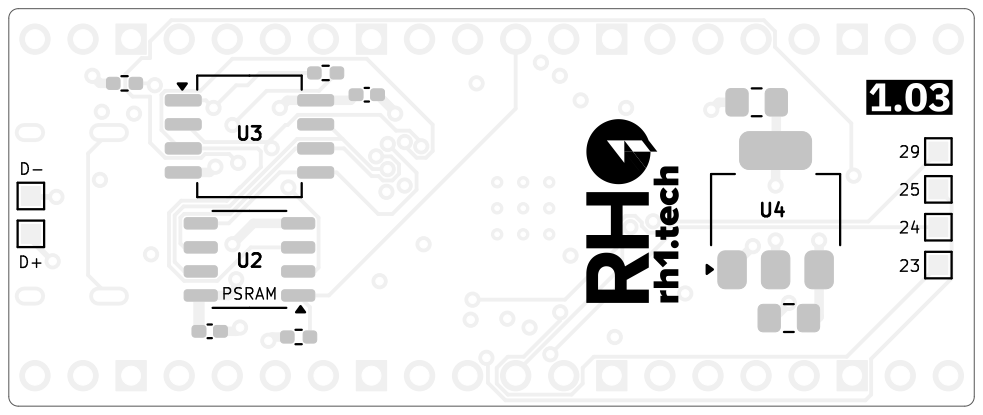
[picture p208: page 2]
PSRAM; D Date: 2025-05-07 KiCad; E.D.A. 9.0.0 Size: A4; Rev: 1.03; File: nyx2.kicad_pcb Sheet: Black; And; White; BOT Mikhail; Matveev; https://github.com/xtremespb/frank Black; BOT -; Page 2/4

Id: /1 Title: Nyx 2

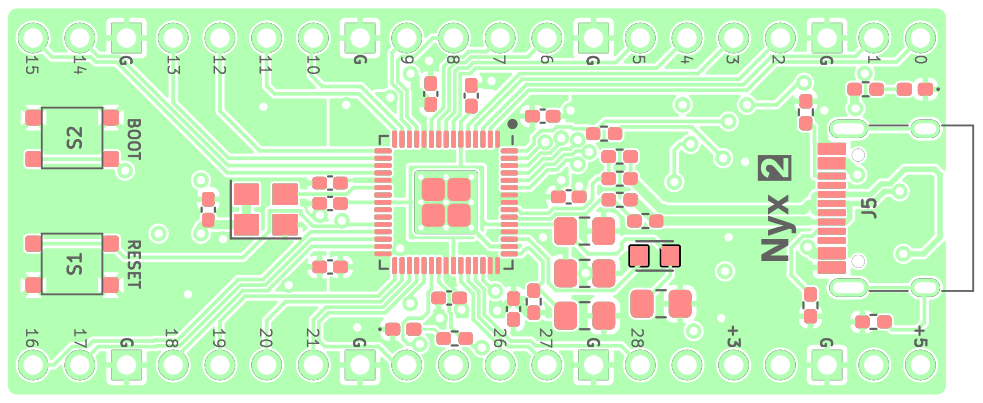
[picture p209: page 3]
D Date: 2025-05-07 KiCad; E.D.A. 9.0.0 Size: A4; Rev: 1.03; File: nyx2.kicad_pcb Sheet: Colored; TOP Mikhail; Matveev; https://github.com/xtremespb/frank Colored; TOP -; Page 3/4 BOOT RESET

Id: /1 Title: Nyx 2

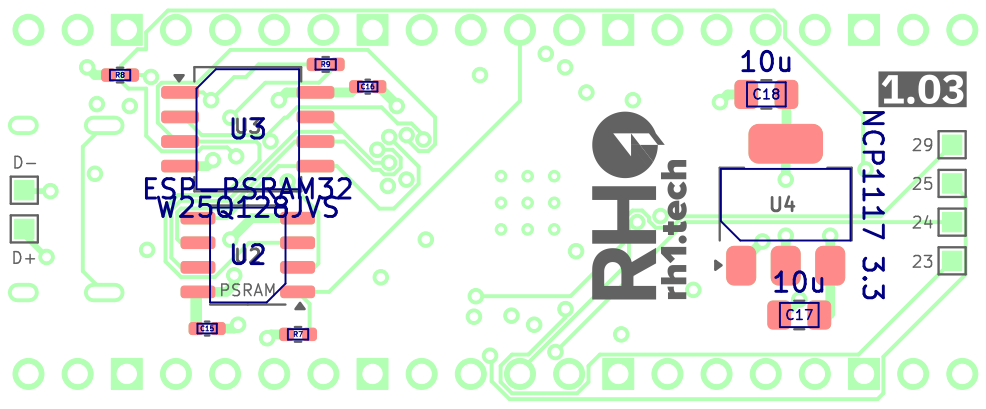
[picture p210: page 4]
