ponikrf/frank/hardware/frank_m1/DOCS/1_15/assembly.pdf

R2 SW1 C6 | C9 1 | 2 | 3 | 4 | 5 | 6 1 | 2 | 3 | 4 | 5 | 6 ABCD | ABCD Date: 2025-03-16 KiCad E.D.A. 9.0.0 Size: A4 | Rev: 1.15

# R46 AV8.4-5 D-SUB 9 Male GP1

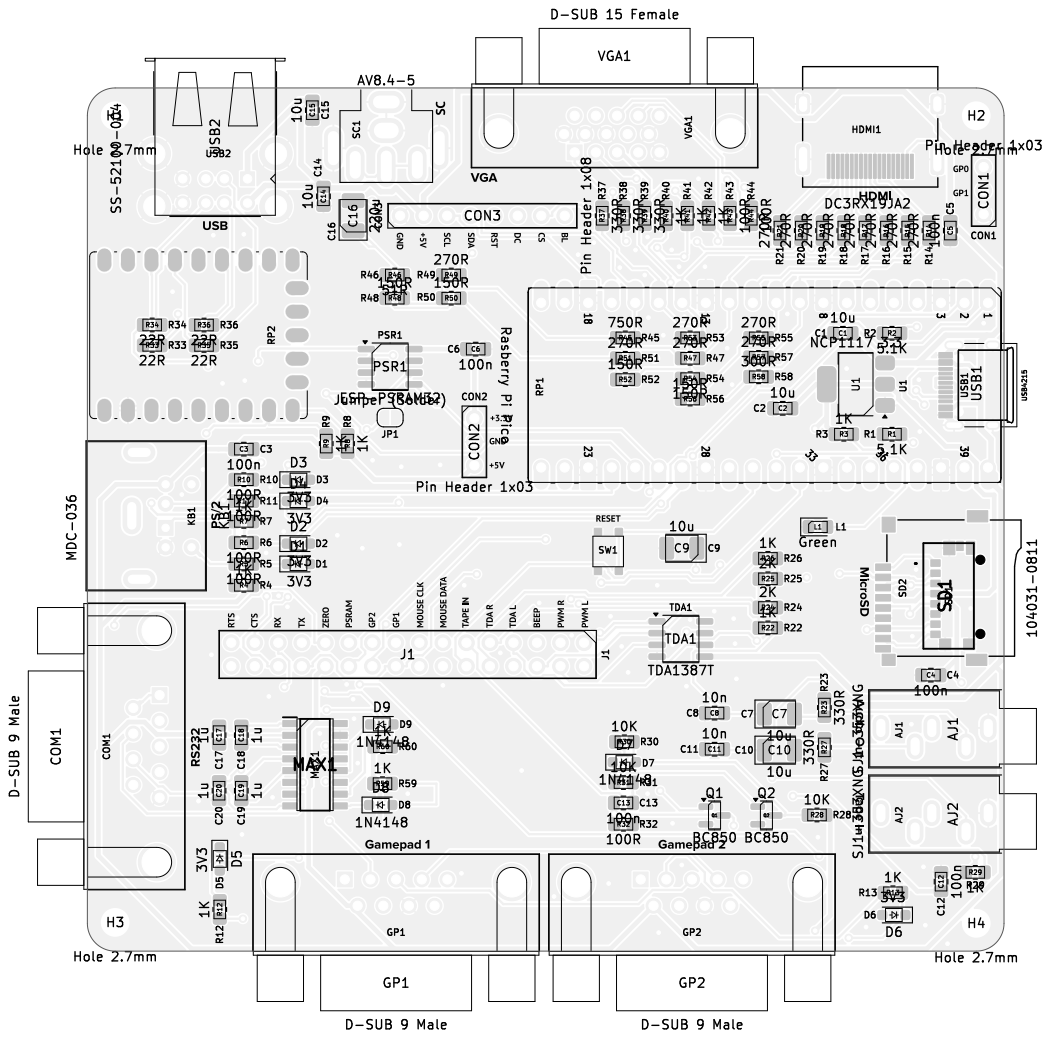
[picture p211: page 1]

https://github.com/xtremespb/frank Black And White TOP - Page 1/2

File: CMZJ2.kicad_pcb Sheet: Black And White TOP Mikhail Matveev

JP2 1 | 2 | 3 | 4 | 5 | 6

A

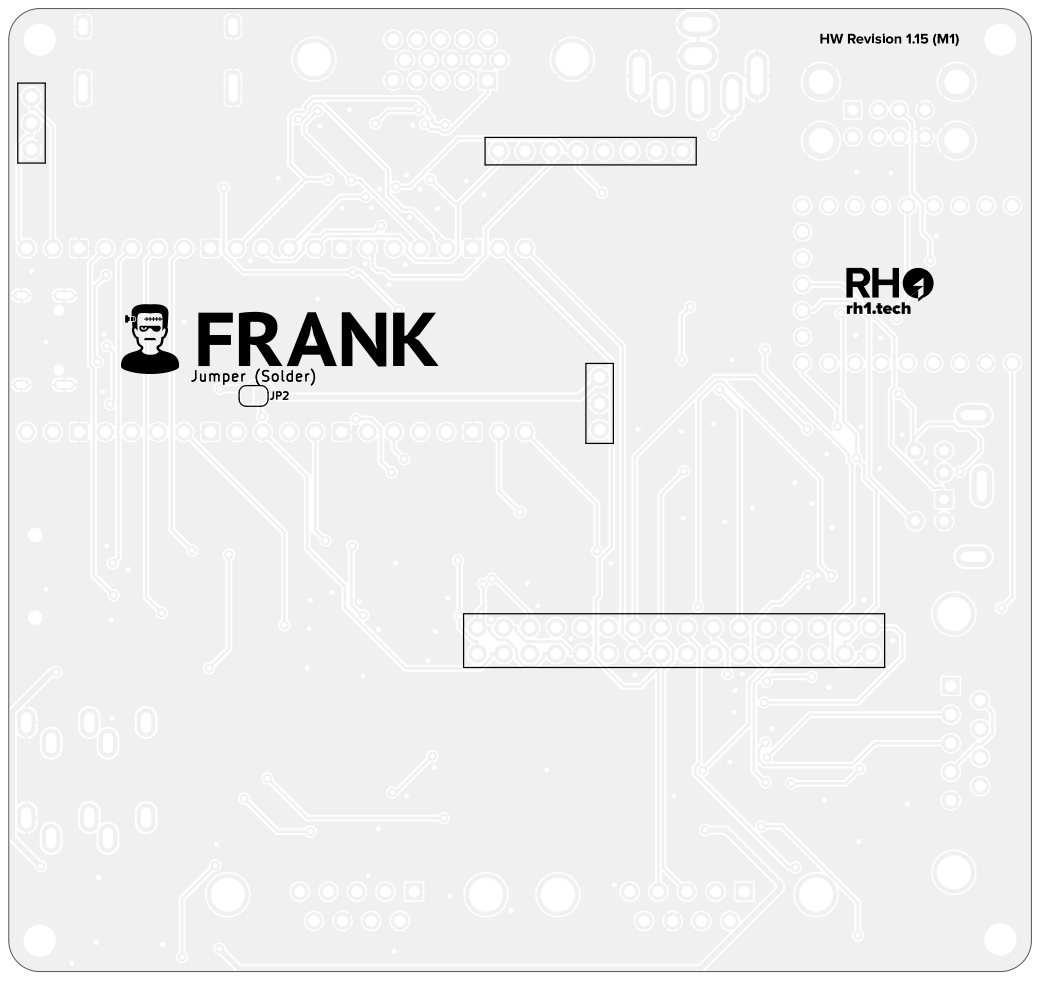
[picture p212: page 2]
D Date: 2025-03-16 KiCad; E.D.A. 9.0.0 Size: A4; Rev: 1.15; File: CMZJ2.kicad_pcb Sheet: Black; And; White; BOT Mikhail; Matveev; https://github.com/xtremespb/frank Black; BOT -; Page 2/2; Jumper (Solder)

Id: /1 Title: FRANK M1
