ponikrf/frank/hardware/frank_m1/DOCS/1_15/CMZJ2.pdf

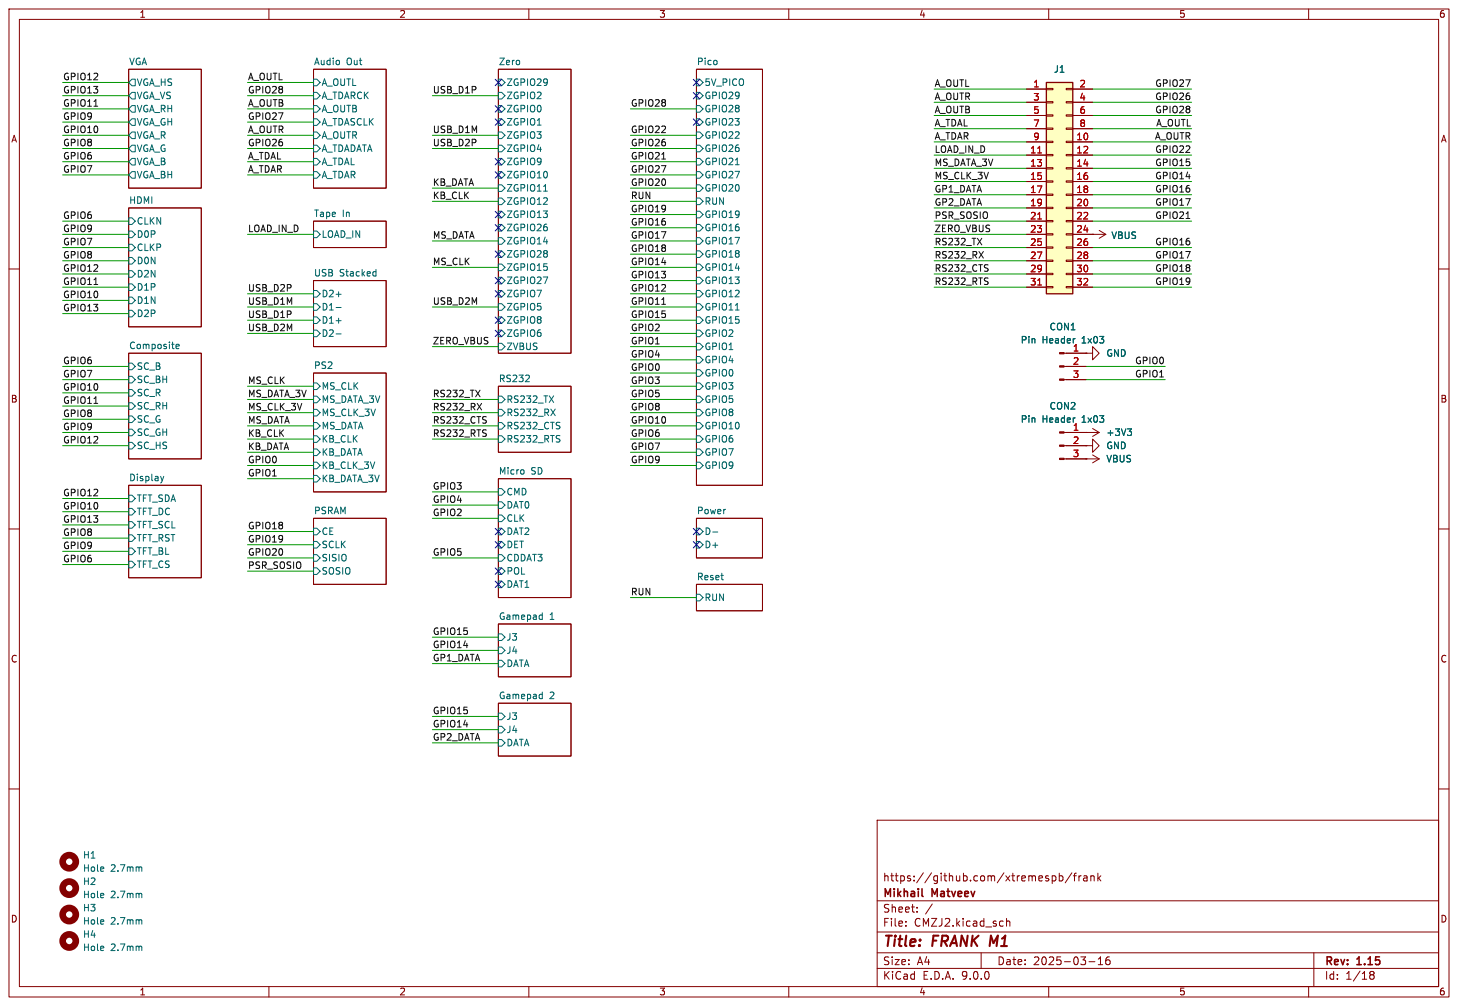
[picture p213: page 1]

Tape In D2+ D1- D1+ D2- USB Stacked CLKN

+3V3 123 CON1 Pin Header 1x03 VBUS H2 Hole 2.7mm

DAT0 CLK DAT2 DET CDDAT3 POL DAT1 Micro SD

https://github.com/xtremespb/frank

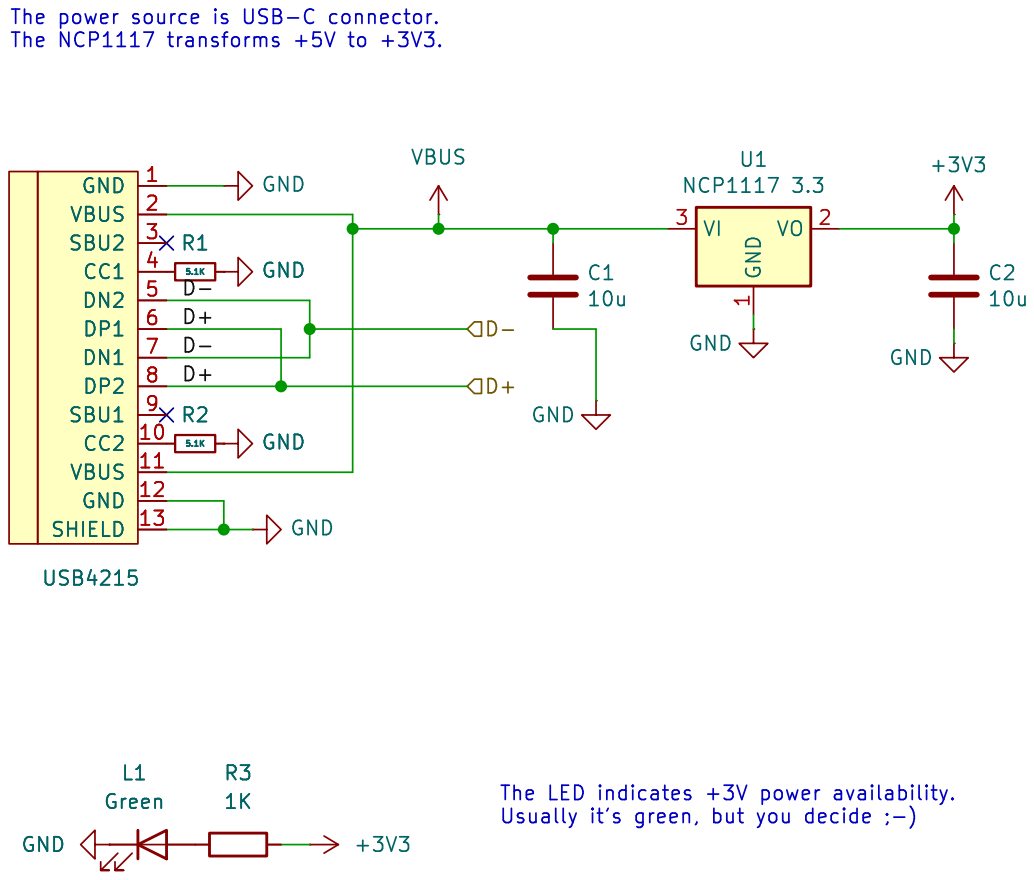
[picture p214: page 2]

Usually it's green, but you decide ;-) GND

https://github.com/xtremespb/frank

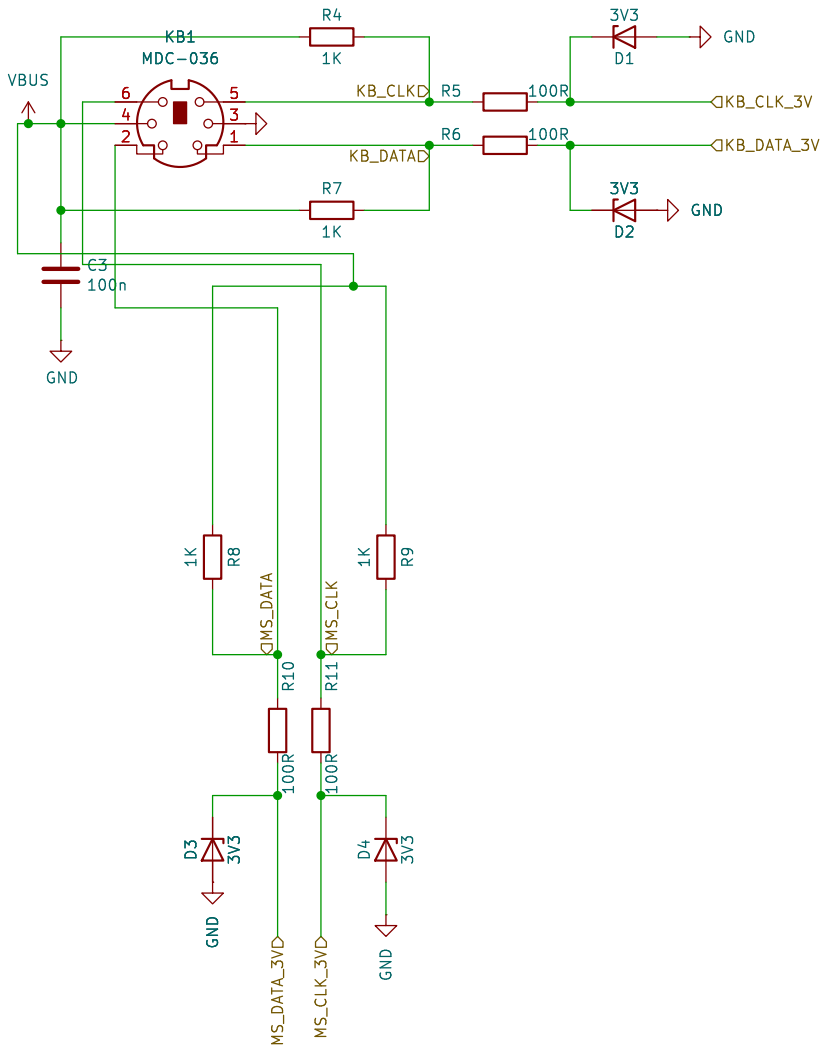
[picture p215: page 3]

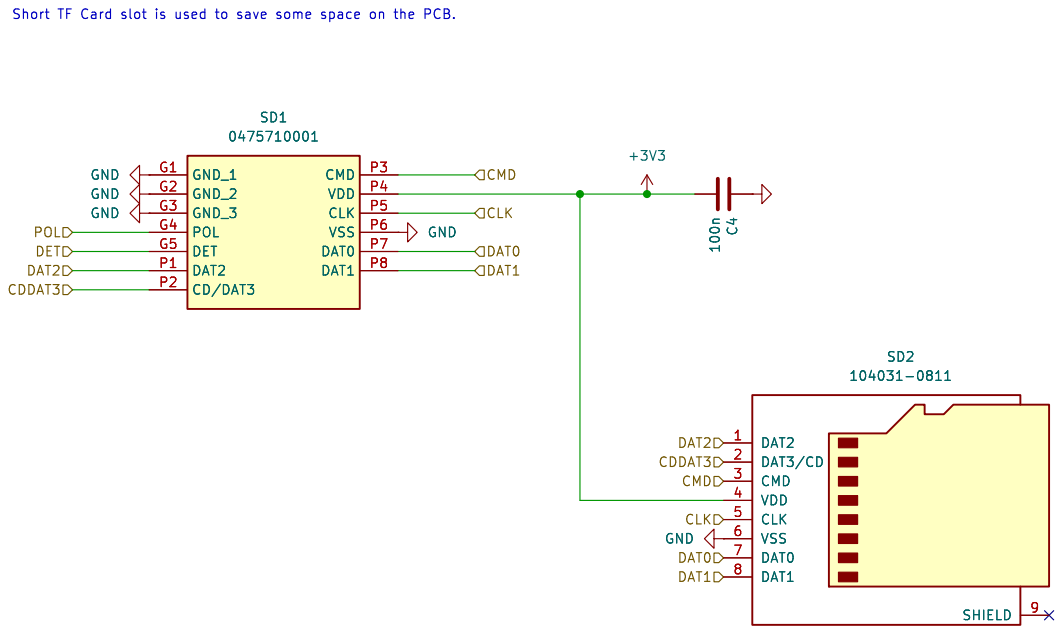
[picture p216: page 4]

https://github.com/xtremespb/frank

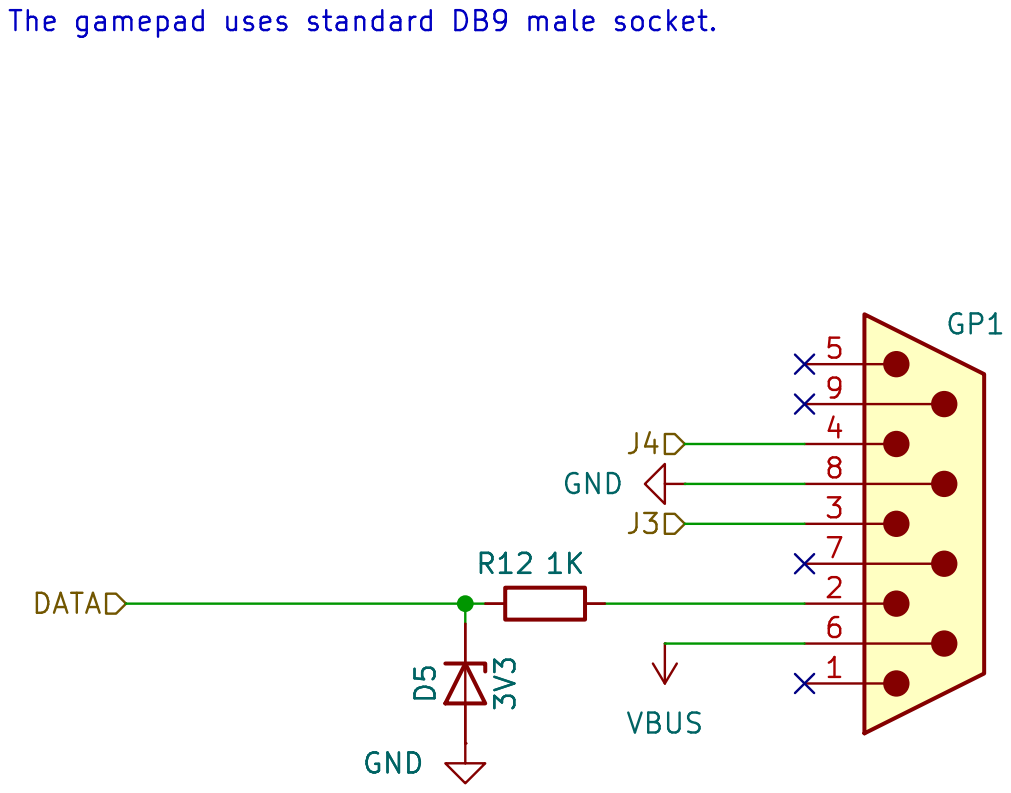
[picture p217: page 5]

https://github.com/xtremespb/frank

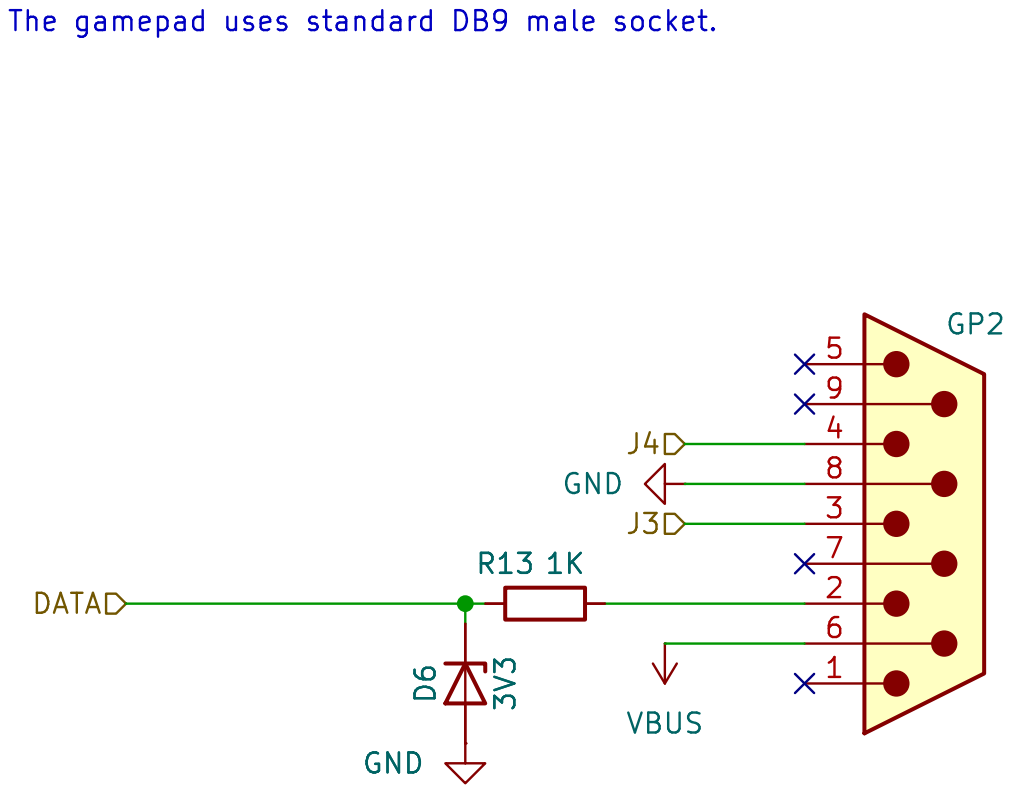
[picture p218: page 6]

https://github.com/xtremespb/frank

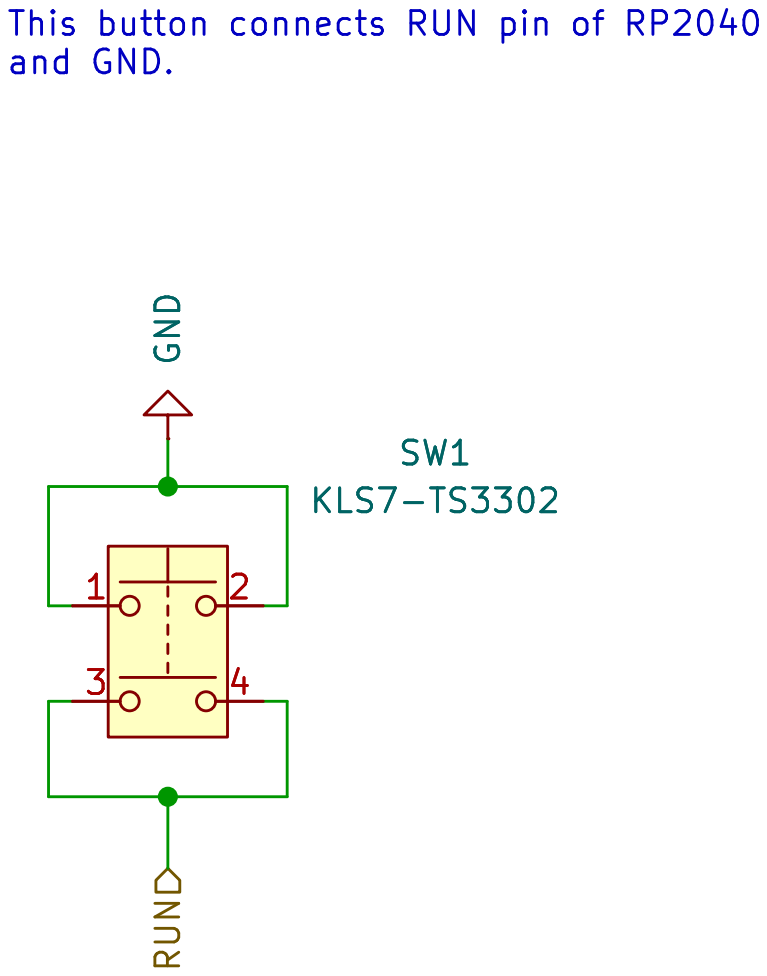
[picture p219: page 7]

https://github.com/xtremespb/frank GND

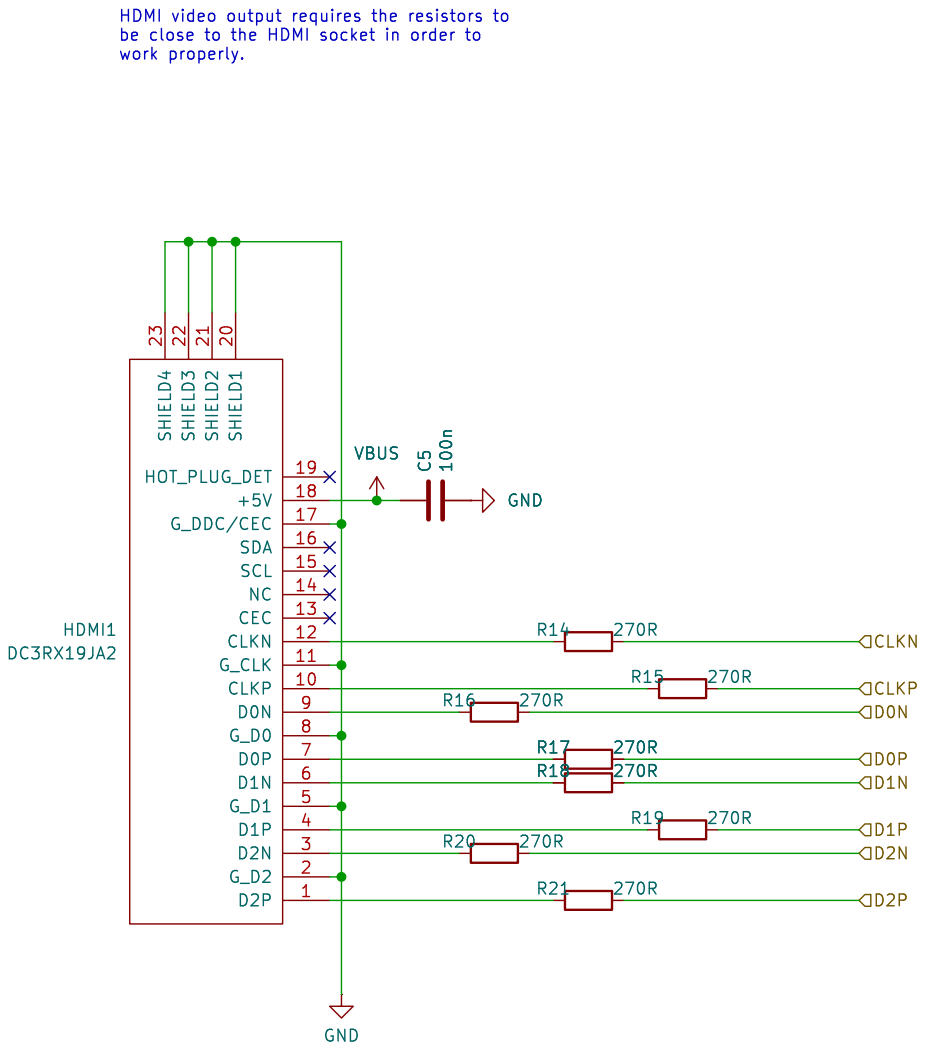
[picture p220: page 8]

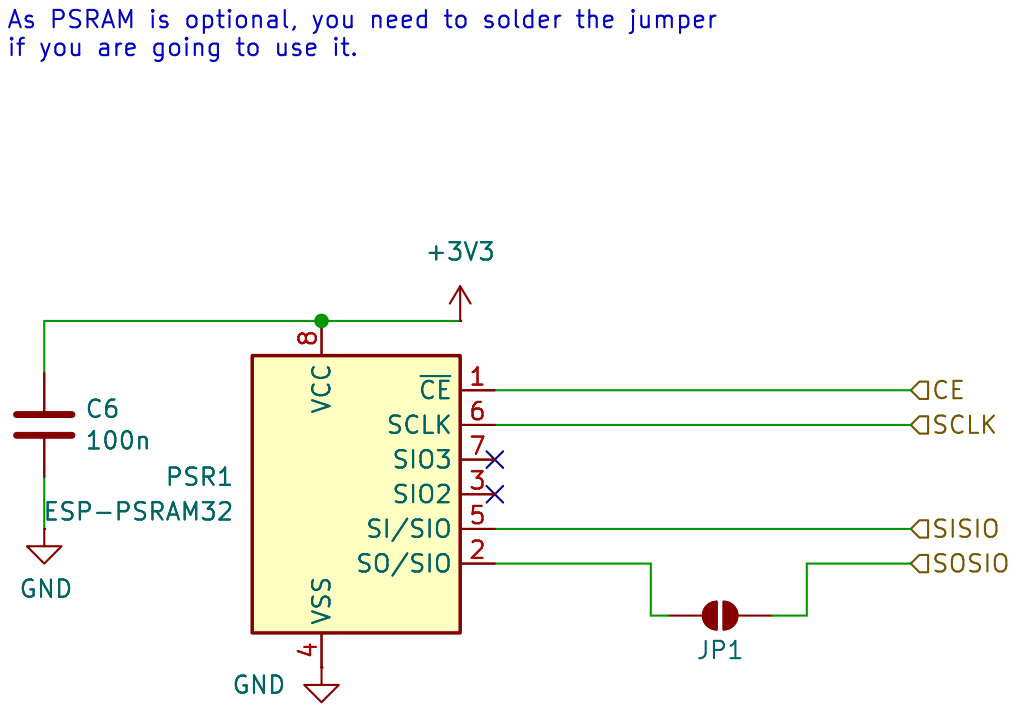
[picture p221: page 9]

if you are going to use it. GND

4 ~{CE}1 SCLK 6 SIO3 7 SIO2 3 SI/SIO 5 SO/SIO 2 +3V3

4 ~{CE}1 SCLK 6 SIO3 7 SIO2 3 SI/SIO 5 SO/SIO 2 PSR1 ESP-PSRAM32

https://github.com/xtremespb/frank

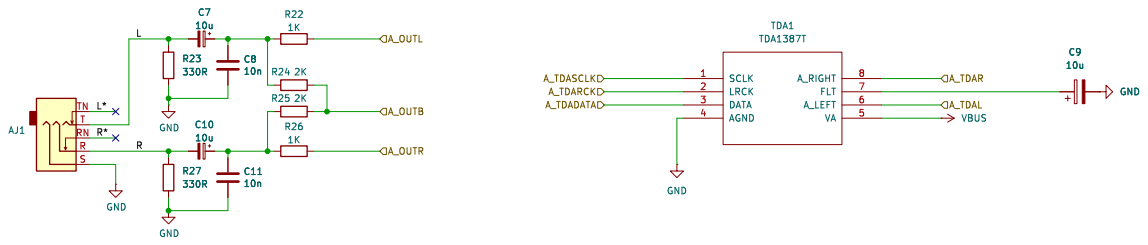
[picture p222: page 10]

https://github.com/xtremespb/frank

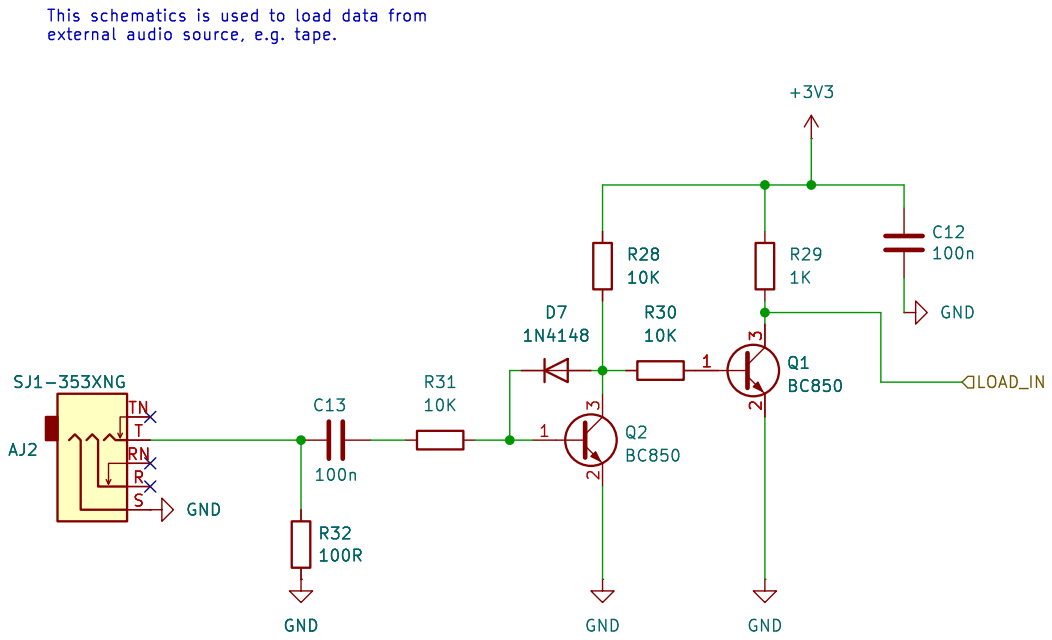
[picture p223: page 11]

https://github.com/xtremespb/frank

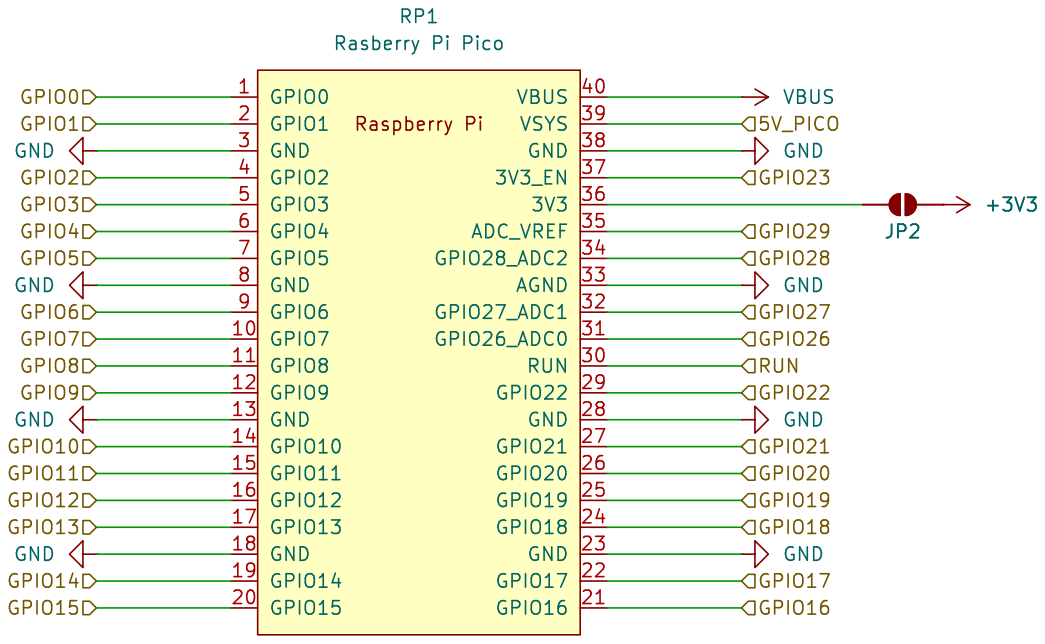
[picture p224: page 12]

https://github.com/xtremespb/frank

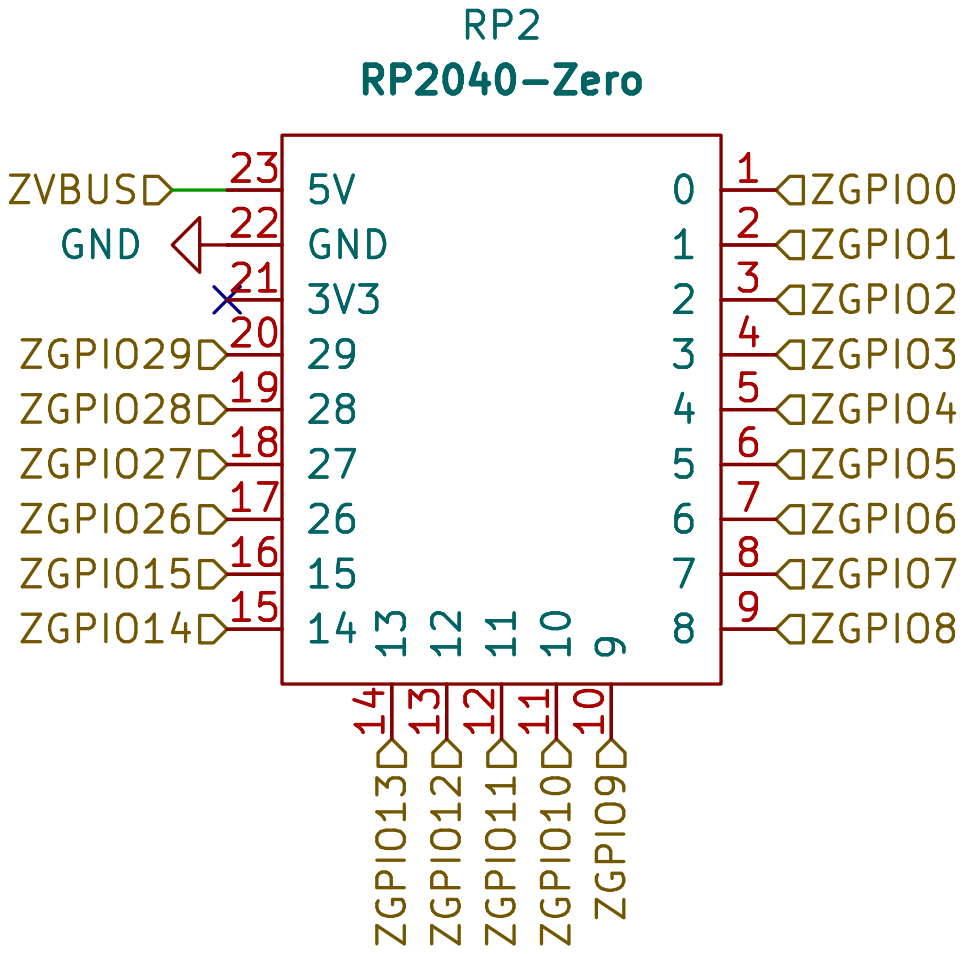
[picture p225: page 13]

https://github.com/xtremespb/frank

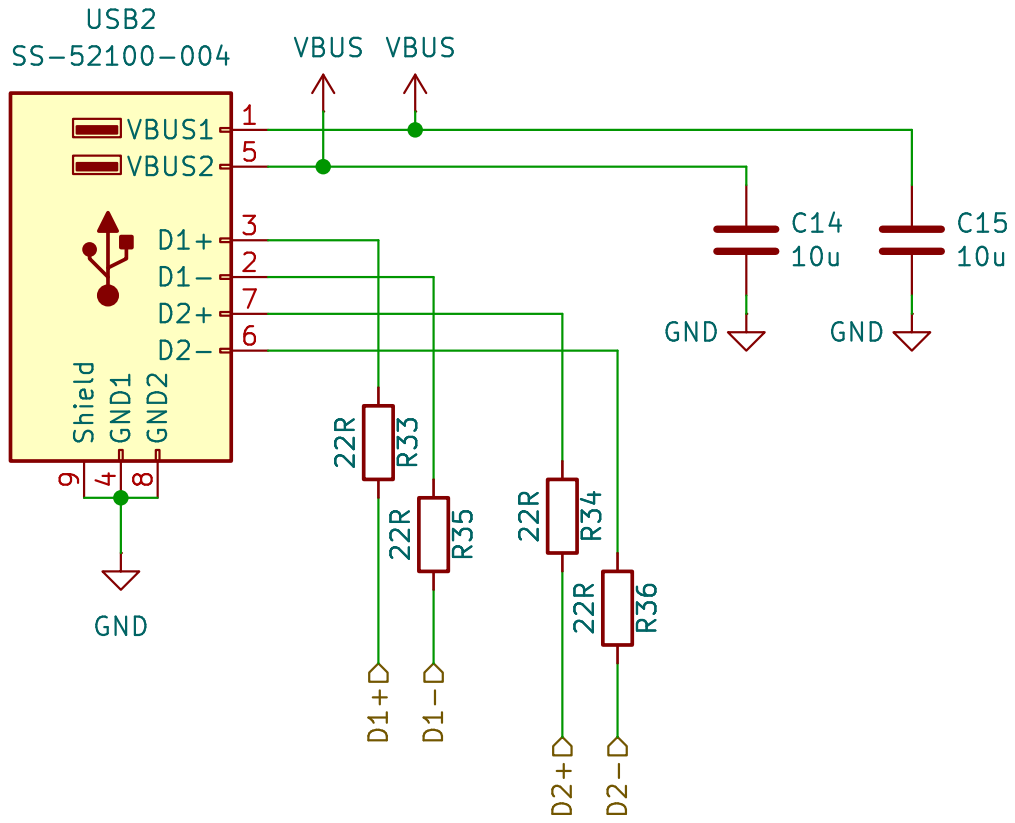
[picture p226: page 14]

https://github.com/xtremespb/frank

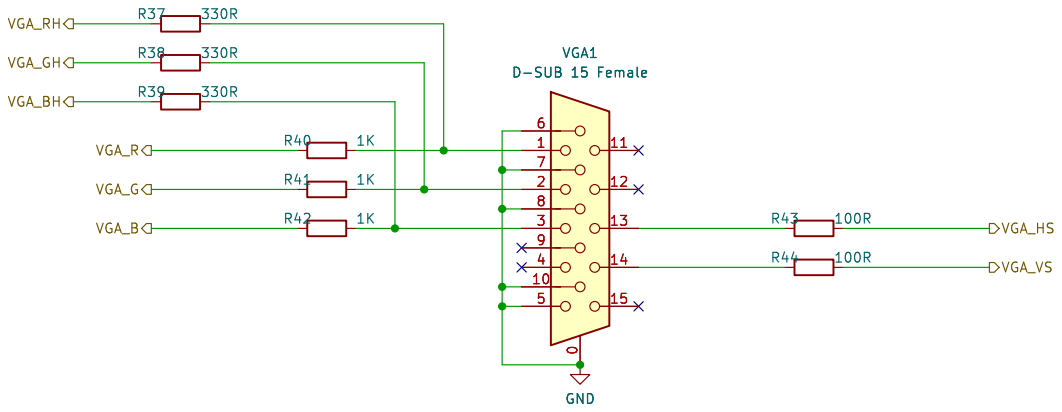
[picture p227: page 15]

https://github.com/xtremespb/frank

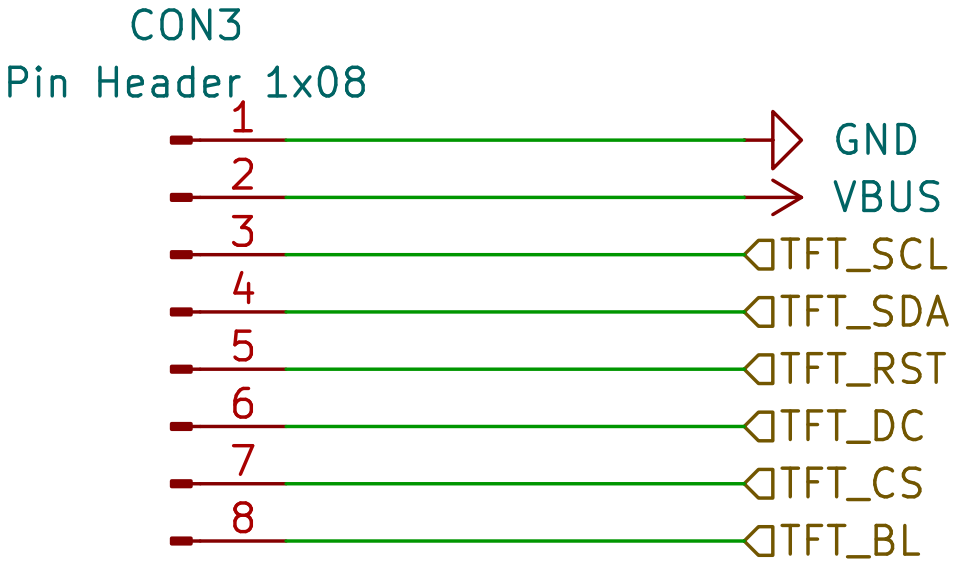
[picture p228: page 16]

https://github.com/xtremespb/frank

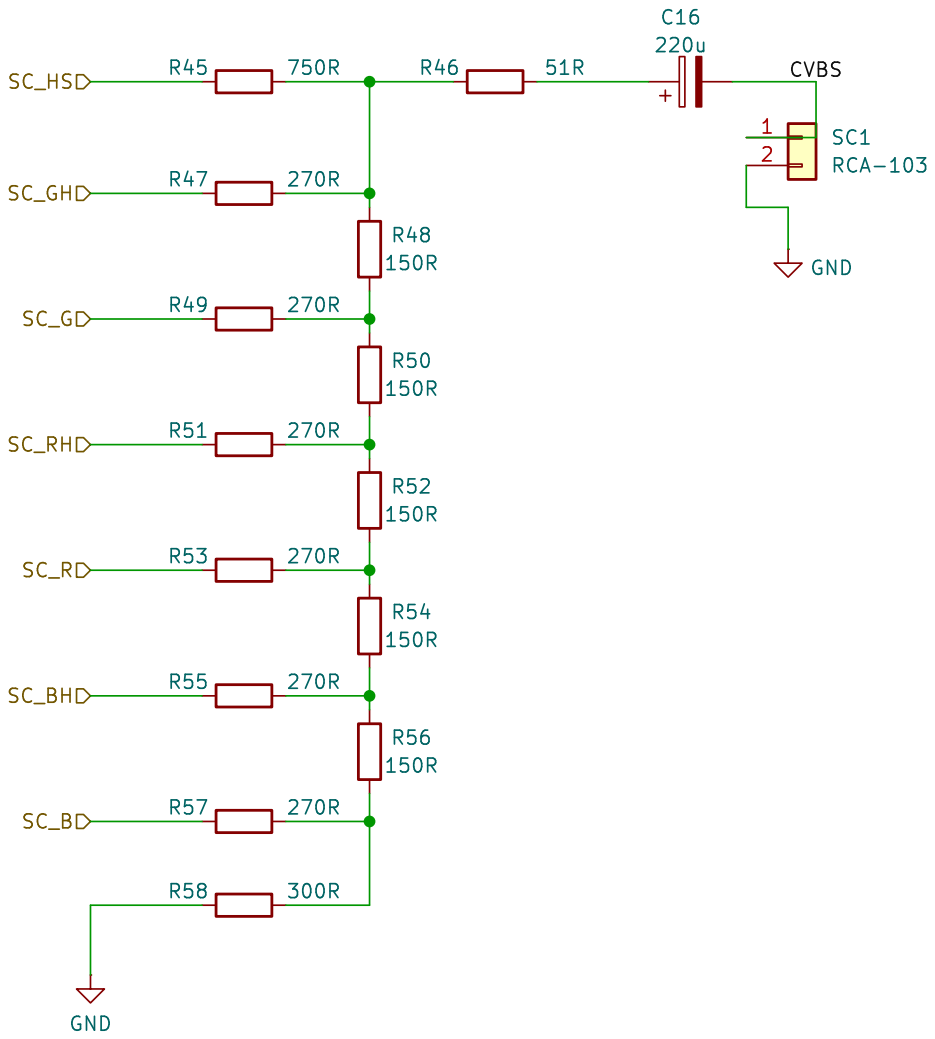
[picture p229: page 17]

https://github.com/xtremespb/frank

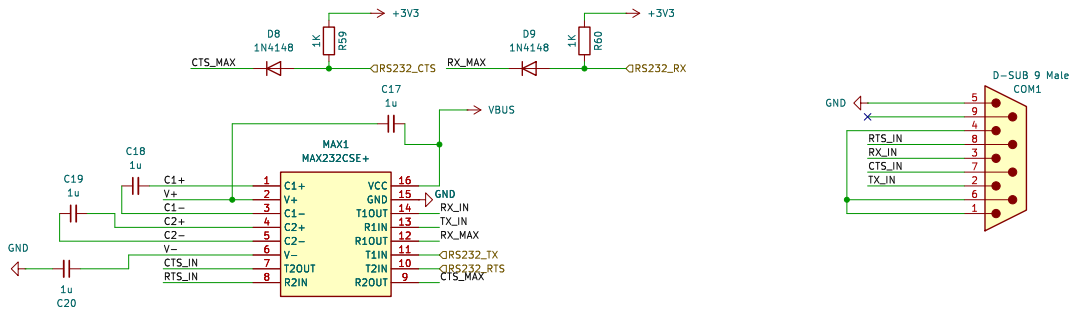
[picture p230: page 18]

https://github.com/xtremespb/frank
