ponikrf/frank/hardware/turbofrank/DOCS/1_03/assembly.pdf

TAPE | BL Gamepad 1 Reset | SDA

# R43 CON¹

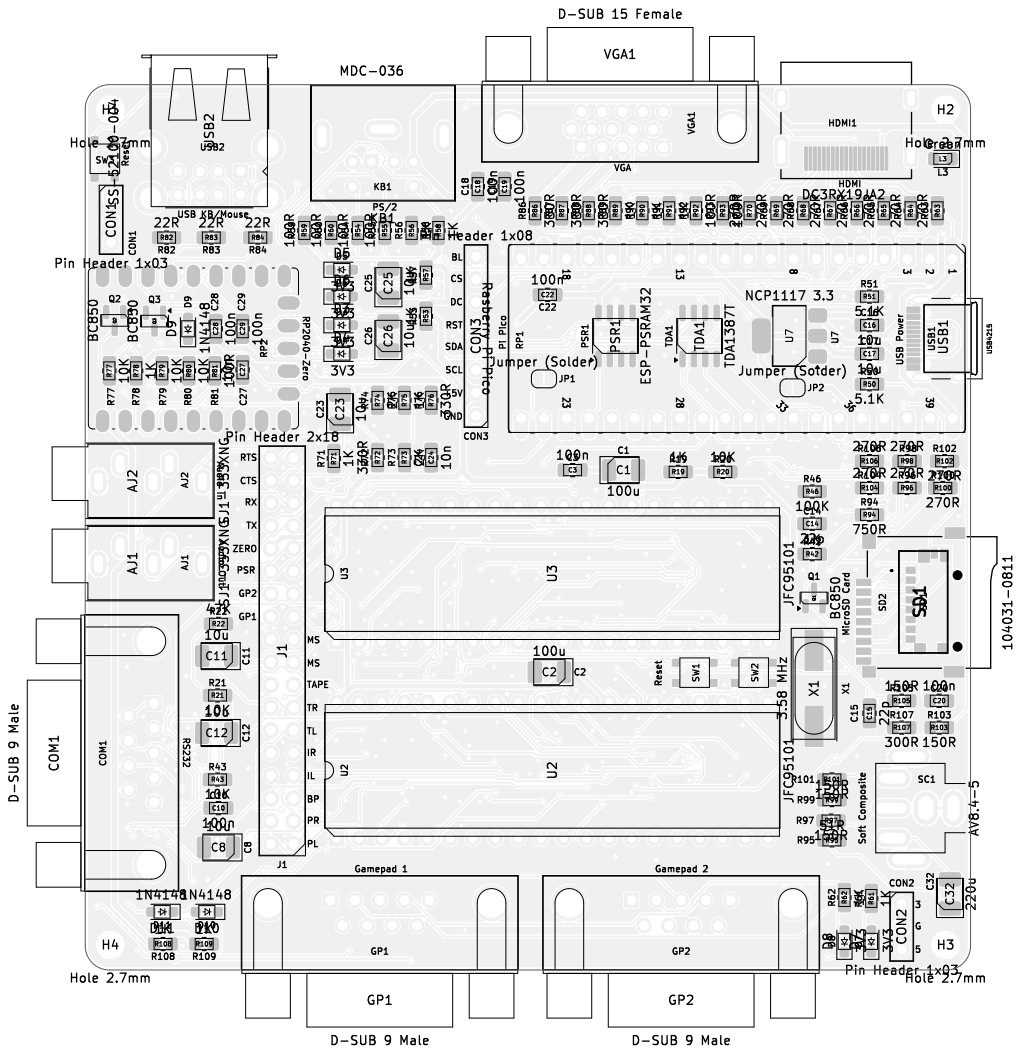
[picture p231: page 1]

R105 Pin Header 1x03 CON² D-SUB 9 Male GP2

File: turbofrank.kicad_pcb Sheet: Black And White TOP Mikhail Matveev

1 | 2 | 3 | 4 | 5 | 6

A

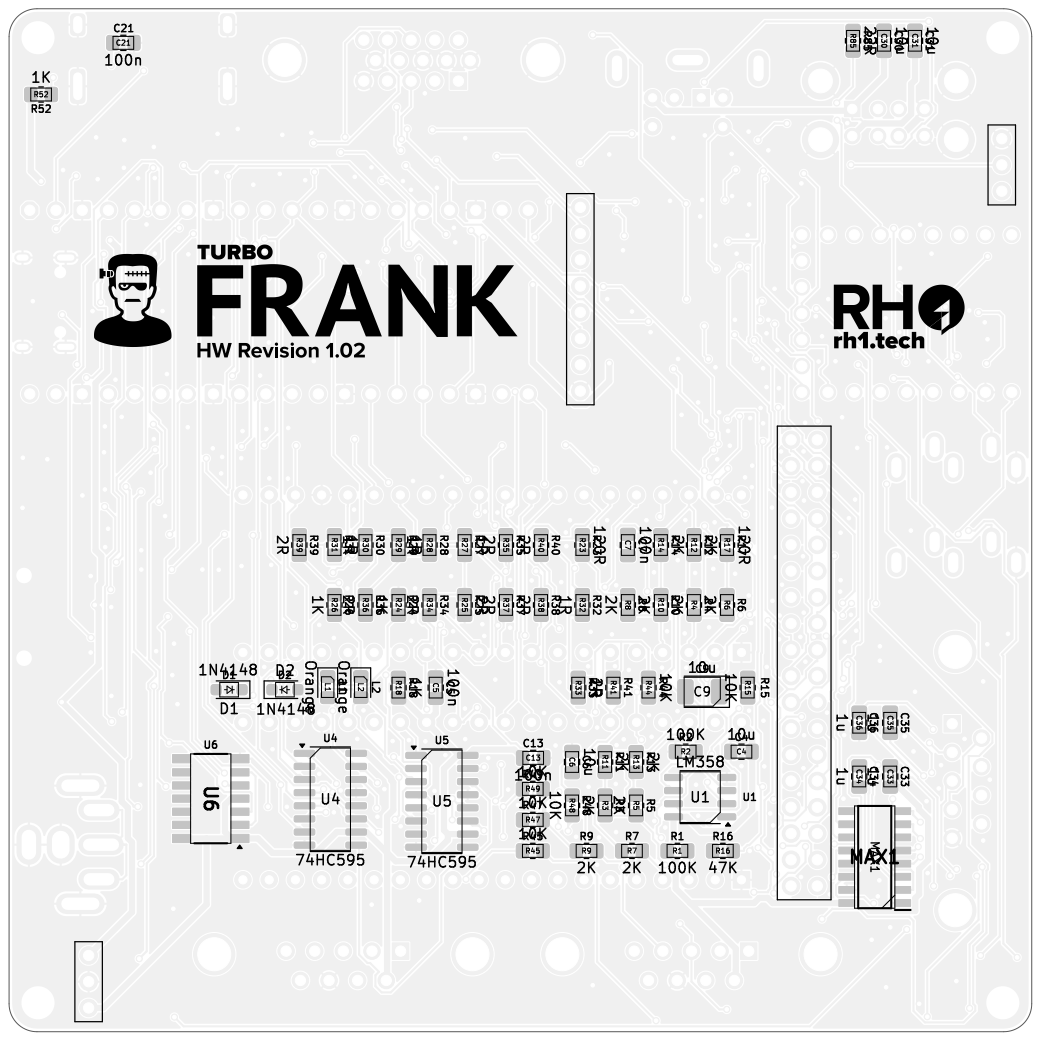
[picture p232: page 2]

File: turbofrank.kicad_pcb Sheet: Black And White BOT Mikhail Matveev
