ponikrf/frank/lab/minifrank_rm2/DOCS/1_02/minifrank_rm2.pdf

HDMI H1 MountingHole H2 MountingHole H3 MountingHole H4 MountingHole

CLK DET CDDAT3 DAT2 SD Card DM1 DM2 DM3 DM4 DM_IN
POL DAT0 DAT1 CMD

Audio Multiplexer D+D- D1+ D1- D2+ D2- SUSB Multiplexer

https://github.com/xtremespb/frank


https://github.com/xtremespb/frank


https://github.com/xtremespb/frank R11


https://github.com/xtremespb/frank R21



https://github.com/xtremespb/frank


https://github.com/xtremespb/frank


https://github.com/xtremespb/frank GND


6 QSPI_IOVDD 54 IOVDD 45 IOVDD 38 GND 61 IOVDD 30 IOVDD 20 IOVDD 11 IOVDD

4 ~{CE}1 SCLK 6 SIO3 7 SIO2 3 SI/SIO 5 SO/SIO 2 U5 ESP-PSRAM32 0R

4 ~{CE}1 SCLK 6 SIO3 7 SIO2 3 SI/SIO 5 SO/SIO 2 GND GND

https://github.com/xtremespb/frank


https://github.com/xtremespb/frank GND





+3V3 GND GND GND GND GND GND




https://github.com/xtremespb/frank
