ponikrf/frank/lab/nyx2/DOCS/1_03/nyx2.pdf

https://github.com/xtremespb/frank


6 QSPI_IOVDD 54 IOVDD 45 IOVDD 38 GND 61 IOVDD 30 IOVDD 20 IOVDD 11 IOVDD

4 ~{CE}1 SCLK 6 SIO3 7 SIO2 3 SI/SIO 5 SO/SIO 2 U2 ESP-PSRAM32 0R

4 ~{CE}1 SCLK 6 SIO3 7 SIO2 3 SI/SIO 5 SO/SIO 2 GND GND

https://github.com/xtremespb/frank


https://github.com/xtremespb/frank
