ponikrf/frank/lab/nyx2/DOCS/1_00/assembly.pdf

https://github.com/xtremespb/frank Colored | BOT - | Page 4/4 C17 W25Q128JVS U4 | R12 ESP-PSRAM32 U3
